Big-Red-Sat/High-Altitude-Student-Platform/HAB Test Data/Battery_Power_Test.txt

Created file at epoch: 1167
(Timestamp: 1169) Temperature Readings: [30.65, 30.65, 244.84, 29.35, 30.00, -26.45, 30.00, -21.94], Solar Cell 1: [Voltage: 0.01V, Current: 0.33mA], Solar Cell 2: [Voltage: 0.01V, Current: 0.65mA]
(Timestamp: 1672) Temperature Readings: [24.19, 22.26, 35.16, 23.23, 23.55, 28.06, 24.19, 28.71], Solar Cell 1: [Voltage: 0.00V, Current: 0.65mA], Solar Cell 2: [Voltage: 0.01V, Current: 0.65mA]
(Timestamp: 2174) Temperature Readings: [24.19, 22.90, 33.23, 23.23, 23.87, 28.71, 24.19, 28.71], Solar Cell 1: [Voltage: 0.00V, Current: 0.65mA], Solar Cell 2: [Voltage: 0.01V, Current: 0.65mA]
(Timestamp: 2677) Temperature Readings: [24.52, 22.90, 32.58, 23.23, 23.87, 28.71, 23.87, 28.39], Solar Cell 1: [Voltage: 0.01V, Current: 0.65mA], Solar Cell 2: [Voltage: 0.01V, Current: 0.65mA]
(Timestamp: 3180) Temperature Readings: [24.19, 26.77, 32.26, 23.23, 23.55, 28.71, 24.19, 28.06], Solar Cell 1: [Voltage: 0.00V, Current: 0.65mA], Solar Cell 2: [Voltage: 0.01V, Current: 0.65mA]
(Timestamp: 3682) Temperature Readings: [24.19, 23.23, 31.94, 23.23, 23.87, 28.06, 24.19, 28.06], Solar Cell 1: [Voltage: 0.00V, Current: 0.65mA], Solar Cell 2: [Voltage: 0.01V, Current: 0.65mA]
(Timestamp: 4185) Temperature Readings: [24.19, 22.58, 31.61, 23.23, 23.55, 28.06, 24.19, 27.74], Solar Cell 1: [Voltage: 0.00V, Current: 0.33mA], Solar Cell 2: [Voltage: 0.01V, Current: 0.65mA]
(Timestamp: 4688) Temperature Readings: [23.87, 22.90, 31.61, 23.23, 23.87, 27.74, 23.87, 26.13], Solar Cell 1: [Voltage: 0.01V, Current: 0.65mA], Solar Cell 2: [Voltage: 0.01V, Current: 0.65mA]
(Timestamp: 5191) Temperature Readings: [25.16, 22.26, 31.94, 23.23, 23.55, 28.06, 24.19, 27.74], Solar Cell 1: [Voltage: 0.00V, Current: 0.33mA], Solar Cell 2: [Voltage: 0.01V, Current: 0.65mA]
(Timestamp: 5694) Temperature Readings: [24.19, 23.23, 31.29, 22.90, 23.87, 27.42, 24.19, 26.45], Solar Cell 1: [Voltage: 0.00V, Current: 0.65mA], Solar Cell 2: [Voltage: 0.01V, Current: 0.65mA]
(Timestamp: 6196) Temperature Readings: [24.52, 22.90, 31.29, 23.23, 23.55, 27.42, 24.19, 25.81], Solar Cell 1: [Voltage: 0.00V, Current: 0.65mA], Solar Cell 2: [Voltage: 0.01V, Current: 0.98mA]
(Timestamp: 6703) Temperature Readings: [24.52, 24.52, 30.97, 23.23, 23.55, 27.10, 24.19, 25.81], Solar Cell 1: [Voltage: 0.00V, Current: 0.65mA], Solar Cell 2: [Voltage: 0.01V, Current: 0.65mA]
(Timestamp: 7205) Temperature Readings: [24.52, 22.58, 30.97, 23.23, 23.55, 26.77, 24.19, 25.81], Solar Cell 1: [Voltage: 0.00V, Current: 0.65mA], Solar Cell 2: [Voltage: 0.01V, Current: 0.65mA]
(Timestamp: 7708) Temperature Readings: [24.84, 22.58, 30.00, 23.55, 23.23, 27.10, 24.19, 25.48], Solar Cell 1: [Voltage: 0.00V, Current: 0.33mA], Solar Cell 2: [Voltage: 0.01V, Current: 0.65mA]
(Timestamp: 8211) Temperature Readings: [25.16, 29.35, 30.65, 23.23, 23.55, 26.77, 24.19, 25.81], Solar Cell 1: [Voltage: 0.00V, Current: 0.65mA], Solar Cell 2: [Voltage: 0.01V, Current: 0.98mA]
(Timestamp: 8714) Temperature Readings: [24.52, 22.90, 30.97, 22.90, 23.23, 26.77, 24.19, 25.48], Solar Cell 1: [Voltage: 0.00V, Current: 0.98mA], Solar Cell 2: [Voltage: 0.01V, Current: 0.65mA]
(Timestamp: 9217) Temperature Readings: [24.52, 23.23, 30.32, 22.90, 23.55, 26.77, 24.19, 25.16], Solar Cell 1: [Voltage: 0.00V, Current: 0.65mA], Solar Cell 2: [Voltage: 0.01V, Current: 0.65mA]
(Timestamp: 9719) Temperature Readings: [24.52, 22.90, 30.32, 23.23, 23.55, 26.77, 24.19, 25.16], Solar Cell 1: [Voltage: 0.00V, Current: 0.33mA], Solar Cell 2: [Voltage: 0.01V, Current: 0.65mA]
(Timestamp: 10222) Temperature Readings: [24.52, 22.90, 30.00, 23.23, 23.55, 27.10, 23.87, 25.16], Solar Cell 1: [Voltage: 0.00V, Current: 0.65mA], Solar Cell 2: [Voltage: 0.01V, Current: 0.65mA]
(Timestamp: 10725) Temperature Readings: [24.52, 22.90, 30.00, 23.23, 23.55, 26.45, 23.87, 25.16], Solar Cell 1: [Voltage: 0.00V, Current: 0.65mA], Solar Cell 2: [Voltage: 0.01V, Current: 0.65mA]
(Timestamp: 11227) Temperature Readings: [24.19, 22.90, 30.00, 23.23, 23.55, 26.45, 24.19, 25.16], Solar Cell 1: [Voltage: 0.01V, Current: 0.65mA], Solar Cell 2: [Voltage: 0.01V, Current: 0.65mA]
(Timestamp: 11730) Temperature Readings: [24.52, 22.90, 30.00, 23.23, 23.55, 26.45, 24.19, 24.84], Solar Cell 1: [Voltage: 0.00V, Current: 0.65mA], Solar Cell 2: [Voltage: 0.01V, Current: 0.98mA]
(Timestamp: 12236) Temperature Readings: [24.52, 22.90, 29.68, 23.55, 23.55, 26.45, 24.19, 24.84], Solar Cell 1: [Voltage: 0.01V, Current: 0.33mA], Solar Cell 2: [Voltage: 0.01V, Current: 0.98mA]
(Timestamp: 12739) Temperature Readings: [24.52, 22.90, 29.68, 23.23, 23.55, 26.45, 24.19, 24.84], Solar Cell 1: [Voltage: 0.01V, Current: 0.65mA], Solar Cell 2: [Voltage: 0.01V, Current: 0.65mA]
(Timestamp: 13241) Temperature Readings: [24.52, 22.90, 29.35, 23.23, 23.55, 26.13, 24.19, 24.52], Solar Cell 1: [Voltage: 0.00V, Current: 0.65mA], Solar Cell 2: [Voltage: 0.01V, Current: 0.65mA]
(Timestamp: 13744) Temperature Readings: [24.52, 22.90, 29.35, 23.23, 23.55, 26.13, 24.19, 24.52], Solar Cell 1: [Voltage: 0.00V, Current: 0.65mA], Solar Cell 2: [Voltage: 0.02V, Current: 0.98mA]
(Timestamp: 14247) Temperature Readings: [24.52, 22.90, 29.35, 23.23, 23.87, 26.13, 24.19, 24.84], Solar Cell 1: [Voltage: 0.00V, Current: 0.65mA], Solar Cell 2: [Voltage: 0.01V, Current: 0.65mA]
(Timestamp: 14749) Temperature Readings: [24.52, 22.90, 29.35, 23.23, 23.55, 25.81, 23.87, 24.52], Solar Cell 1: [Voltage: 0.01V, Current: 0.33mA], Solar Cell 2: [Voltage: 0.01V, Current: 0.98mA]
(Timestamp: 15252) Temperature Readings: [24.19, 22.90, 29.35, 23.23, 23.55, 25.81, 23.87, 24.52], Solar Cell 1: [Voltage: 0.01V, Current: 0.33mA], Solar Cell 2: [Voltage: 0.01V, Current: 0.65mA]
(Timestamp: 15755) Temperature Readings: [24.52, 22.90, 29.35, 23.23, 23.55, 25.81, 24.19, 24.52], Solar Cell 1: [Voltage: 0.00V, Current: 0.65mA], Solar Cell 2: [Voltage: 0.01V, Current: 0.65mA]
(Timestamp: 16258) Temperature Readings: [24.52, 22.90, 29.03, 23.23, 23.55, 25.81, 24.19, 24.52], Solar Cell 1: [Voltage: 0.00V, Current: 0.65mA], Solar Cell 2: [Voltage: 0.01V, Current: 0.65mA]
(Timestamp: 16761) Temperature Readings: [24.19, 23.23, 29.35, 23.23, 23.87, 25.81, 24.19, 24.52], Solar Cell 1: [Voltage: 0.00V, Current: 0.33mA], Solar Cell 2: [Voltage: 0.01V, Current: 0.65mA]
(Timestamp: 17263) Temperature Readings: [24.52, 22.90, 29.03, 23.23, 23.55, 25.81, 24.19, 24.19], Solar Cell 1: [Voltage: 0.00V, Current: 0.65mA], Solar Cell 2: [Voltage: 0.01V, Current: 0.65mA]
(Timestamp: 17766) Temperature Readings: [24.19, 22.90, 29.03, 23.23, 23.55, 25.81, 24.19, 24.19], Solar Cell 1: [Voltage: 0.00V, Current: 0.65mA], Solar Cell 2: [Voltage: 0.01V, Current: 0.65mA]
(Timestamp: 18272) Temperature Readings: [24.52, 22.90, 29.03, 23.55, 23.55, 25.81, 24.19, 24.19], Solar Cell 1: [Voltage: 0.00V, Current: 0.65mA], Solar Cell 2: [Voltage: 0.01V, Current: 0.65mA]
(Timestamp: 18775) Temperature Readings: [24.52, 23.23, 29.03, 23.55, 23.55, 25.81, 24.19, 24.19], Solar Cell 1: [Voltage: 0.00V, Current: 0.65mA], Solar Cell 2: [Voltage: 0.01V, Current: 0.65mA]
(Timestamp: 19278) Temperature Readings: [24.52, 22.90, 29.03, 23.23, 23.87, 25.81, 24.19, 24.19], Solar Cell 1: [Voltage: 0.00V, Current: 0.65mA], Solar Cell 2: [Voltage: 0.01V, Current: 0.65mA]
(Timestamp: 19781) Temperature Readings: [24.52, 22.90, 29.03, 23.23, 23.55, 25.81, 24.19, 24.52], Solar Cell 1: [Voltage: 0.00V, Current: 0.65mA], Solar Cell 2: [Voltage: 0.01V, Current: 0.98mA]
(Timestamp: 20284) Temperature Readings: [24.52, 22.90, 29.03, 23.23, 23.55, 25.48, 24.19, 24.19], Solar Cell 1: [Voltage: 0.00V, Current: 0.65mA], Solar Cell 2: [Voltage: 0.01V, Current: 0.65mA]
(Timestamp: 20786) Temperature Readings: [24.52, 22.90, 29.03, 23.23, 23.55, 25.48, 24.19, 24.19], Solar Cell 1: [Voltage: 0.00V, Current: 0.33mA], Solar Cell 2: [Voltage: 0.01V, Current: 0.65mA]
(Timestamp: 21289) Temperature Readings: [24.19, 22.90, 29.03, 23.55, 23.87, 25.48, 24.19, 24.52], Solar Cell 1: [Voltage: 1.86V, Current: 3.26mA], Solar Cell 2: [Voltage: 2.15V, Current: 4.90mA]
(Timestamp: 21791) Temperature Readings: [24.52, 22.90, 28.39, 23.23, 23.87, 25.48, 23.87, 25.16], Solar Cell 1: [Voltage: 1.55V, Current: 2.94mA], Solar Cell 2: [Voltage: 0.86V, Current: 75.09mA]
(Timestamp: 22294) Temperature Readings: [24.19, 22.90, 29.03, 23.23, 23.55, 25.16, 24.19, 24.52], Solar Cell 1: [Voltage: 1.88V, Current: 3.59mA], Solar Cell 2: [Voltage: 2.52V, Current: 5.22mA]
(Timestamp: 22796) Temperature Readings: [24.52, 22.90, 28.39, 23.23, 23.55, 25.16, 24.19, 24.19], Solar Cell 1: [Voltage: 2.15V, Current: 3.59mA], Solar Cell 2: [Voltage: 2.65V, Current: 5.55mA]
(Timestamp: 23299) Temperature Readings: [24.52, 22.90, 28.39, 23.23, 23.55, 23.87, 24.19, 23.87], Solar Cell 1: [Voltage: 1.82V, Current: 3.26mA], Solar Cell 2: [Voltage: 1.63V, Current: 4.24mA]
(Timestamp: 23801) Temperature Readings: [24.52, 22.90, 28.71, 23.55, 23.87, 25.16, 24.19, 24.52], Solar Cell 1: [Voltage: 2.21V, Current: 3.59mA], Solar Cell 2: [Voltage: 3.00V, Current: 6.20mA]
(Timestamp: 24308) Temperature Readings: [24.52, 22.90, 28.71, 23.55, 23.55, 24.19, 24.19, 24.19], Solar Cell 1: [Voltage: 2.05V, Current: 3.92mA], Solar Cell 2: [Voltage: 2.73V, Current: 5.55mA]
(Timestamp: 24811) Temperature Readings: [24.52, 22.90, 28.71, 23.55, 23.87, 25.16, 24.19, 24.19], Solar Cell 1: [Voltage: 2.22V, Current: 3.59mA], Solar Cell 2: [Voltage: 2.82V, Current: 5.88mA]
(Timestamp: 25313) Temperature Readings: [24.52, 23.23, 28.39, 23.23, 23.87, 25.81, 24.19, 25.81], Solar Cell 1: [Voltage: 1.96V, Current: 3.26mA], Solar Cell 2: [Voltage: 1.16V, Current: 105.13mA]
(Timestamp: 25816) Temperature Readings: [24.84, 23.23, 28.71, 23.23, 23.55, 25.16, 24.19, 24.19], Solar Cell 1: [Voltage: 2.11V, Current: 3.59mA], Solar Cell 2: [Voltage: 2.79V, Current: 5.88mA]
(Timestamp: 26319) Temperature Readings: [24.52, 22.90, 28.71, 23.23, 23.55, 24.19, 24.19, 24.19], Solar Cell 1: [Voltage: 2.23V, Current: 3.92mA], Solar Cell 2: [Voltage: 2.94V, Current: 5.88mA]
(Timestamp: 26822) Temperature Readings: [24.52, 22.90, 28.06, 23.23, 23.87, 24.52, 24.19, 24.84], Solar Cell 1: [Voltage: 1.86V, Current: 3.26mA], Solar Cell 2: [Voltage: 1.03V, Current: 95.01mA]
(Timestamp: 27324) Temperature Readings: [24.52, 22.90, 28.71, 23.55, 23.87, 23.87, 24.19, 24.19], Solar Cell 1: [Voltage: 2.17V, Current: 3.92mA], Solar Cell 2: [Voltage: 3.00V, Current: 6.20mA]
(Timestamp: 27827) Temperature Readings: [24.52, 23.23, 28.39, 23.23, 23.55, 23.87, 24.19, 23.87], Solar Cell 1: [Voltage: 2.18V, Current: 3.92mA], Solar Cell 2: [Voltage: 2.75V, Current: 5.88mA]
(Timestamp: 28330) Temperature Readings: [24.52, 22.90, 28.06, 23.55, 23.55, 23.87, 24.19, 23.23], Solar Cell 1: [Voltage: 1.90V, Current: 3.59mA], Solar Cell 2: [Voltage: 1.81V, Current: 4.57mA]
(Timestamp: 28833) Temperature Readings: [24.52, 22.58, 28.39, 23.55, 23.87, 23.87, 24.19, 24.19], Solar Cell 1: [Voltage: 2.19V, Current: 3.92mA], Solar Cell 2: [Voltage: 3.02V, Current: 6.20mA]
(Timestamp: 29336) Temperature Readings: [24.52, 22.90, 28.39, 23.23, 23.87, 23.87, 24.19, 23.87], Solar Cell 1: [Voltage: 2.14V, Current: 3.59mA], Solar Cell 2: [Voltage: 2.37V, Current: 5.22mA]
(Timestamp: 29838) Temperature Readings: [24.52, 22.90, 28.39, 23.55, 23.55, 23.87, 24.19, 23.87], Solar Cell 1: [Voltage: 1.98V, Current: 3.92mA], Solar Cell 2: [Voltage: 2.55V, Current: 5.55mA]
(Timestamp: 30345) Temperature Readings: [24.52, 22.90, 28.06, 23.23, 23.87, 24.19, 24.19, 24.84], Solar Cell 1: [Voltage: 1.98V, Current: 3.26mA], Solar Cell 2: [Voltage: 0.98V, Current: 86.52mA]
(Timestamp: 30848) Temperature Readings: [24.52, 23.23, 28.39, 23.55, 23.87, 23.87, 24.19, 23.87], Solar Cell 1: [Voltage: 2.21V, Current: 3.59mA], Solar Cell 2: [Voltage: 2.95V, Current: 6.20mA]
(Timestamp: 31350) Temperature Readings: [24.84, 22.58, 28.39, 23.55, 23.87, 23.87, 24.19, 24.19], Solar Cell 1: [Voltage: 2.34V, Current: 3.92mA], Solar Cell 2: [Voltage: 2.95V, Current: 5.88mA]
(Timestamp: 31853) Temperature Readings: [24.52, 22.90, 27.74, 23.23, 23.87, 23.87, 24.19, 24.84], Solar Cell 1: [Voltage: 2.05V, Current: 3.59mA], Solar Cell 2: [Voltage: 0.95V, Current: 83.26mA]
(Timestamp: 32355) Temperature Readings: [24.84, 23.23, 28.06, 23.55, 23.55, 23.55, 24.19, 23.87], Solar Cell 1: [Voltage: 2.24V, Current: 3.92mA], Solar Cell 2: [Voltage: 2.94V, Current: 5.88mA]
(Timestamp: 32858) Temperature Readings: [24.52, 22.90, 28.39, 23.55, 23.87, 24.19, 24.19, 23.87], Solar Cell 1: [Voltage: 2.33V, Current: 3.92mA], Solar Cell 2: [Voltage: 2.94V, Current: 5.88mA]
(Timestamp: 33360) Temperature Readings: [24.52, 23.23, 27.74, 23.23, 23.87, 23.87, 24.19, 24.84], Solar Cell 1: [Voltage: 2.02V, Current: 3.59mA], Solar Cell 2: [Voltage: 0.95V, Current: 83.58mA]
(Timestamp: 33863) Temperature Readings: [24.84, 22.90, 28.06, 23.55, 23.55, 23.55, 24.19, 23.87], Solar Cell 1: [Voltage: 2.19V, Current: 3.92mA], Solar Cell 2: [Voltage: 2.93V, Current: 5.88mA]
(Timestamp: 34366) Temperature Readings: [24.52, 22.90, 28.39, 23.55, 23.87, 23.55, 24.19, 24.19], Solar Cell 1: [Voltage: 2.26V, Current: 3.92mA], Solar Cell 2: [Voltage: 2.95V, Current: 5.88mA]
(Timestamp: 34868) Temperature Readings: [24.52, 22.90, 27.74, 23.23, 23.55, 23.87, 24.19, 24.52], Solar Cell 1: [Voltage: 1.90V, Current: 3.26mA], Solar Cell 2: [Voltage: 1.02V, Current: 93.38mA]
(Timestamp: 35371) Temperature Readings: [24.52, 22.90, 27.74, 23.23, 23.55, 23.55, 24.19, 23.87], Solar Cell 1: [Voltage: 2.16V, Current: 3.92mA], Solar Cell 2: [Voltage: 2.99V, Current: 6.20mA]
(Timestamp: 35878) Temperature Readings: [24.52, 22.90, 28.06, 23.23, 23.87, 23.23, 24.19, 23.23], Solar Cell 1: [Voltage: 1.97V, Current: 3.59mA], Solar Cell 2: [Voltage: 2.45V, Current: 5.22mA]
(Timestamp: 36380) Temperature Readings: [24.52, 22.90, 28.06, 23.55, 23.87, 23.55, 24.19, 23.87], Solar Cell 1: [Voltage: 2.23V, Current: 3.92mA], Solar Cell 2: [Voltage: 3.03V, Current: 6.20mA]
(Timestamp: 36883) Temperature Readings: [24.52, 22.90, 28.06, 23.55, 23.87, 23.23, 24.19, 23.23], Solar Cell 1: [Voltage: 2.12V, Current: 3.59mA], Solar Cell 2: [Voltage: 1.86V, Current: 4.57mA]
(Timestamp: 37386) Temperature Readings: [24.52, 22.90, 27.74, 23.55, 23.87, 23.23, 24.19, 23.87], Solar Cell 1: [Voltage: 2.06V, Current: 3.92mA], Solar Cell 2: [Voltage: 2.75V, Current: 5.88mA]
(Timestamp: 37889) Temperature Readings: [24.52, 23.23, 28.06, 23.55, 23.55, 23.23, 24.19, 23.87], Solar Cell 1: [Voltage: 2.26V, Current: 3.92mA], Solar Cell 2: [Voltage: 3.00V, Current: 6.20mA]
(Timestamp: 38392) Temperature Readings: [24.52, 22.90, 27.74, 23.55, 23.87, 23.23, 24.19, 24.19], Solar Cell 1: [Voltage: 2.02V, Current: 3.59mA], Solar Cell 2: [Voltage: 1.29V, Current: 115.58mA]
(Timestamp: 38894) Temperature Readings: [24.84, 22.90, 27.74, 23.55, 23.87, 23.23, 24.19, 23.87], Solar Cell 1: [Voltage: 2.10V, Current: 3.92mA], Solar Cell 2: [Voltage: 2.87V, Current: 5.88mA]
(Timestamp: 39397) Temperature Readings: [24.52, 22.90, 27.74, 23.55, 23.87, 23.23, 24.19, 23.87], Solar Cell 1: [Voltage: 2.24V, Current: 3.92mA], Solar Cell 2: [Voltage: 2.96V, Current: 5.88mA]
(Timestamp: 39900) Temperature Readings: [24.84, 23.23, 27.74, 23.23, 23.87, 23.87, 24.19, 24.19], Solar Cell 1: [Voltage: 1.99V, Current: 3.26mA], Solar Cell 2: [Voltage: 0.95V, Current: 83.91mA]
(Timestamp: 40403) Temperature Readings: [24.84, 23.23, 28.06, 23.55, 23.87, 23.23, 24.19, 23.87], Solar Cell 1: [Voltage: 2.17V, Current: 3.59mA], Solar Cell 2: [Voltage: 2.93V, Current: 5.88mA]
(Timestamp: 40905) Temperature Readings: [24.52, 23.23, 27.74, 23.55, 23.55, 23.23, 24.19, 23.87], Solar Cell 1: [Voltage: 2.23V, Current: 3.92mA], Solar Cell 2: [Voltage: 2.85V, Current: 5.88mA]
(Timestamp: 41408) Temperature Readings: [24.52, 22.90, 27.42, 23.55, 23.87, 23.87, 24.19, 25.16], Solar Cell 1: [Voltage: 1.90V, Current: 3.59mA], Solar Cell 2: [Voltage: 1.26V, Current: 115.91mA]
(Timestamp: 41914) Temperature Readings: [24.52, 23.23, 27.42, 23.55, 23.87, 23.23, 24.19, 23.23], Solar Cell 1: [Voltage: 2.17V, Current: 3.59mA], Solar Cell 2: [Voltage: 2.48V, Current: 5.22mA]
(Timestamp: 42417) Temperature Readings: [24.52, 23.23, 27.42, 23.55, 23.87, 23.23, 24.19, 22.90], Solar Cell 1: [Voltage: 1.95V, Current: 3.59mA], Solar Cell 2: [Voltage: 2.14V, Current: 4.90mA]
(Timestamp: 42919) Temperature Readings: [24.84, 23.23, 27.74, 23.55, 23.87, 23.23, 24.19, 23.87], Solar Cell 1: [Voltage: 2.19V, Current: 3.92mA], Solar Cell 2: [Voltage: 2.86V, Current: 5.88mA]
(Timestamp: 43422) Temperature Readings: [24.52, 22.90, 27.74, 23.55, 23.87, 23.23, 24.19, 23.23], Solar Cell 1: [Voltage: 2.16V, Current: 3.92mA], Solar Cell 2: [Voltage: 2.41V, Current: 5.22mA]
(Timestamp: 43925) Temperature Readings: [24.52, 23.23, 27.74, 23.55, 23.87, 23.23, 24.19, 22.90], Solar Cell 1: [Voltage: 1.93V, Current: 3.59mA], Solar Cell 2: [Voltage: 2.05V, Current: 4.90mA]
(Timestamp: 44427) Temperature Readings: [24.84, 23.23, 27.74, 23.55, 23.87, 23.23, 24.19, 23.87], Solar Cell 1: [Voltage: 2.17V, Current: 4.24mA], Solar Cell 2: [Voltage: 3.01V, Current: 6.20mA]
(Timestamp: 44930) Temperature Readings: [24.84, 22.90, 27.74, 23.55, 23.55, 23.23, 24.19, 23.23], Solar Cell 1: [Voltage: 2.13V, Current: 3.59mA], Solar Cell 2: [Voltage: 2.33V, Current: 5.22mA]
(Timestamp: 45433) Temperature Readings: [24.84, 23.23, 27.42, 23.55, 23.87, 23.23, 24.19, 23.23], Solar Cell 1: [Voltage: 1.95V, Current: 3.59mA], Solar Cell 2: [Voltage: 2.45V, Current: 5.22mA]
(Timestamp: 45935) Temperature Readings: [24.84, 22.90, 27.74, 23.55, 23.87, 22.90, 24.19, 23.87], Solar Cell 1: [Voltage: 2.17V, Current: 3.92mA], Solar Cell 2: [Voltage: 3.03V, Current: 6.20mA]
(Timestamp: 46438) Temperature Readings: [24.52, 22.90, 27.42, 23.23, 23.87, 22.58, 24.19, 22.58], Solar Cell 1: [Voltage: 2.04V, Current: 3.59mA], Solar Cell 2: [Voltage: 1.68V, Current: 4.24mA]
(Timestamp: 46941) Temperature Readings: [24.52, 23.23, 27.42, 23.55, 23.55, 23.23, 24.19, 23.23], Solar Cell 1: [Voltage: 2.03V, Current: 3.59mA], Solar Cell 2: [Voltage: 2.84V, Current: 5.88mA]
(Timestamp: 47444) Temperature Readings: [24.52, 22.90, 27.74, 23.55, 23.55, 23.23, 24.19, 23.23], Solar Cell 1: [Voltage: 2.18V, Current: 3.59mA], Solar Cell 2: [Voltage: 3.01V, Current: 6.20mA]
(Timestamp: 47950) Temperature Readings: [24.52, 23.23, 27.42, 23.55, 23.87, 23.23, 24.19, 23.23], Solar Cell 1: [Voltage: 2.14V, Current: 3.92mA], Solar Cell 2: [Voltage: 2.99V, Current: 6.20mA]
(Timestamp: 48453) Temperature Readings: [24.52, 23.23, 27.42, 23.55, 23.87, 23.23, 24.19, 23.23], Solar Cell 1: [Voltage: 2.14V, Current: 3.59mA], Solar Cell 2: [Voltage: 2.72V, Current: 5.55mA]
(Timestamp: 48956) Temperature Readings: [24.84, 23.23, 27.42, 23.23, 23.87, 22.58, 24.19, 22.58], Solar Cell 1: [Voltage: 1.90V, Current: 3.59mA], Solar Cell 2: [Voltage: 2.01V, Current: 4.90mA]
(Timestamp: 49458) Temperature Readings: [24.52, 22.90, 27.42, 23.55, 23.87, 23.23, 24.19, 23.55], Solar Cell 1: [Voltage: 2.17V, Current: 3.92mA], Solar Cell 2: [Voltage: 3.06V, Current: 6.20mA]
(Timestamp: 49961) Temperature Readings: [24.84, 22.90, 27.42, 23.55, 23.55, 22.58, 24.19, 22.90], Solar Cell 1: [Voltage: 2.10V, Current: 3.59mA], Solar Cell 2: [Voltage: 2.28V, Current: 5.22mA]
(Timestamp: 50464) Temperature Readings: [24.84, 23.23, 27.42, 23.55, 23.87, 22.90, 24.19, 23.23], Solar Cell 1: [Voltage: 1.97V, Current: 3.92mA], Solar Cell 2: [Voltage: 2.69V, Current: 5.55mA]
(Timestamp: 50967) Temperature Readings: [24.52, 23.23, 27.42, 23.55, 23.87, 22.90, 24.19, 23.55], Solar Cell 1: [Voltage: 2.17V, Current: 3.92mA], Solar Cell 2: [Voltage: 3.07V, Current: 6.20mA]
(Timestamp: 51469) Temperature Readings: [24.52, 22.90, 27.42, 23.55, 23.87, 22.58, 24.19, 22.26], Solar Cell 1: [Voltage: 2.00V, Current: 3.59mA], Solar Cell 2: [Voltage: 1.39V, Current: 34.28mA]
(Timestamp: 51972) Temperature Readings: [24.84, 23.23, 27.42, 23.55, 23.55, 22.90, 24.19, 23.23], Solar Cell 1: [Voltage: 2.05V, Current: 3.59mA], Solar Cell 2: [Voltage: 2.94V, Current: 5.88mA]
(Timestamp: 52475) Temperature Readings: [24.84, 22.90, 27.42, 23.55, 23.87, 22.58, 24.19, 23.87], Solar Cell 1: [Voltage: 1.03V, Current: 112.32mA], Solar Cell 2: [Voltage: 3.05V, Current: 5.88mA]
(Timestamp: 52977) Temperature Readings: [24.84, 23.23, 27.42, 23.55, 23.87, 23.23, 24.19, 24.84], Solar Cell 1: [Voltage: 1.99V, Current: 3.59mA], Solar Cell 2: [Voltage: 1.17V, Current: 106.77mA]
(Timestamp: 53483) Temperature Readings: [24.84, 23.23, 27.42, 23.55, 23.55, 22.58, 24.19, 23.23], Solar Cell 1: [Voltage: 2.21V, Current: 3.92mA], Solar Cell 2: [Voltage: 2.86V, Current: 5.88mA]
(Timestamp: 53986) Temperature Readings: [24.84, 23.23, 27.10, 23.55, 23.87, 23.23, 24.19, 24.84], Solar Cell 1: [Voltage: 1.86V, Current: 3.59mA], Solar Cell 2: [Voltage: 1.30V, Current: 95.01mA]
(Timestamp: 54489) Temperature Readings: [24.84, 23.23, 27.42, 23.55, 23.87, 22.58, 24.19, 23.23], Solar Cell 1: [Voltage: 2.16V, Current: 3.92mA], Solar Cell 2: [Voltage: 3.03V, Current: 6.20mA]
(Timestamp: 54991) Temperature Readings: [24.84, 23.23, 27.42, 23.55, 23.87, 22.58, 24.19, 23.23], Solar Cell 1: [Voltage: 2.21V, Current: 3.92mA], Solar Cell 2: [Voltage: 2.86V, Current: 5.88mA]
(Timestamp: 55494) Temperature Readings: [24.84, 23.23, 27.10, 23.55, 23.87, 22.58, 24.19, 22.26], Solar Cell 1: [Voltage: 1.89V, Current: 3.59mA], Solar Cell 2: [Voltage: 1.54V, Current: 4.24mA]
(Timestamp: 55997) Temperature Readings: [24.84, 23.23, 27.42, 23.55, 23.87, 22.58, 24.19, 23.23], Solar Cell 1: [Voltage: 2.20V, Current: 3.92mA], Solar Cell 2: [Voltage: 3.05V, Current: 6.20mA]
(Timestamp: 56499) Temperature Readings: [24.84, 23.23, 27.42, 23.55, 23.87, 22.90, 24.19, 22.90], Solar Cell 1: [Voltage: 2.15V, Current: 3.92mA], Solar Cell 2: [Voltage: 2.57V, Current: 5.55mA]
(Timestamp: 57002) Temperature Readings: [24.84, 23.23, 27.10, 23.55, 23.87, 22.58, 24.19, 22.90], Solar Cell 1: [Voltage: 1.95V, Current: 3.59mA], Solar Cell 2: [Voltage: 2.42V, Current: 5.22mA]
(Timestamp: 57505) Temperature Readings: [24.84, 23.23, 27.42, 23.23, 23.87, 22.58, 24.19, 23.23], Solar Cell 1: [Voltage: 2.21V, Current: 3.59mA], Solar Cell 2: [Voltage: 3.06V, Current: 6.20mA]
(Timestamp: 58008) Temperature Readings: [24.84, 23.23, 27.42, 23.55, 23.87, 22.58, 24.19, 22.26], Solar Cell 1: [Voltage: 2.09V, Current: 3.59mA], Solar Cell 2: [Voltage: 1.86V, Current: 4.24mA]
(Timestamp: 58510) Temperature Readings: [24.84, 23.23, 27.10, 23.55, 23.87, 22.26, 24.19, 22.90], Solar Cell 1: [Voltage: 2.06V, Current: 3.92mA], Solar Cell 2: [Voltage: 2.83V, Current: 5.88mA]
(Timestamp: 59013) Temperature Readings: [24.84, 23.55, 27.42, 23.55, 23.87, 22.58, 24.19, 23.23], Solar Cell 1: [Voltage: 2.23V, Current: 3.92mA], Solar Cell 2: [Voltage: 3.04V, Current: 6.20mA]
(Timestamp: 59520) Temperature Readings: [25.16, 23.23, 27.10, 23.55, 23.87, 22.58, 24.19, 23.23], Solar Cell 1: [Voltage: 2.17V, Current: 3.92mA], Solar Cell 2: [Voltage: 3.02V, Current: 6.20mA]
(Timestamp: 60022) Temperature Readings: [24.84, 23.23, 27.42, 23.55, 23.87, 22.58, 24.52, 23.23], Solar Cell 1: [Voltage: 2.20V, Current: 3.92mA], Solar Cell 2: [Voltage: 2.83V, Current: 5.88mA]
(Timestamp: 60525) Temperature Readings: [24.84, 23.23, 27.10, 23.55, 23.87, 22.58, 24.19, 22.26], Solar Cell 1: [Voltage: 1.90V, Current: 3.59mA], Solar Cell 2: [Voltage: 1.79V, Current: 4.57mA]
(Timestamp: 61028) Temperature Readings: [24.84, 22.90, 27.10, 23.55, 23.87, 22.58, 24.19, 23.23], Solar Cell 1: [Voltage: 2.24V, Current: 3.92mA], Solar Cell 2: [Voltage: 3.07V, Current: 6.20mA]
(Timestamp: 61531) Temperature Readings: [24.84, 23.23, 27.10, 23.55, 23.87, 22.58, 24.19, 22.90], Solar Cell 1: [Voltage: 2.15V, Current: 3.92mA], Solar Cell 2: [Voltage: 2.48V, Current: 5.22mA]
(Timestamp: 62033) Temperature Readings: [24.84, 23.23, 27.10, 23.55, 23.87, 22.58, 24.19, 22.58], Solar Cell 1: [Voltage: 2.00V, Current: 3.92mA], Solar Cell 2: [Voltage: 2.54V, Current: 5.55mA]
(Timestamp: 62536) Temperature Readings: [24.84, 23.23, 27.10, 23.55, 23.87, 22.58, 24.19, 22.90], Solar Cell 1: [Voltage: 2.24V, Current: 3.92mA], Solar Cell 2: [Voltage: 2.25V, Current: 5.22mA]
(Timestamp: 63039) Temperature Readings: [24.84, 23.23, 27.10, 23.55, 23.87, 22.26, 24.19, 22.58], Solar Cell 1: [Voltage: 2.13V, Current: 3.92mA], Solar Cell 2: [Voltage: 1.83V, Current: 4.57mA]
(Timestamp: 63541) Temperature Readings: [24.84, 23.23, 27.10, 23.55, 23.87, 22.58, 24.19, 22.90], Solar Cell 1: [Voltage: 1.96V, Current: 3.59mA], Solar Cell 2: [Voltage: 2.50V, Current: 5.55mA]
(Timestamp: 64044) Temperature Readings: [25.16, 23.23, 27.42, 23.55, 23.87, 22.58, 24.19, 23.23], Solar Cell 1: [Voltage: 2.20V, Current: 3.92mA], Solar Cell 2: [Voltage: 3.12V, Current: 6.20mA]
(Timestamp: 64546) Temperature Readings: [25.16, 23.23, 27.10, 23.55, 23.87, 22.58, 24.19, 22.26], Solar Cell 1: [Voltage: 2.10V, Current: 3.59mA], Solar Cell 2: [Voltage: 2.20V, Current: 4.90mA]
(Timestamp: 65049) Temperature Readings: [24.84, 23.23, 27.10, 23.55, 23.87, 22.58, 24.19, 22.90], Solar Cell 1: [Voltage: 1.97V, Current: 3.59mA], Solar Cell 2: [Voltage: 2.59V, Current: 5.55mA]
(Timestamp: 65555) Temperature Readings: [24.84, 23.23, 27.10, 23.55, 23.87, 22.90, 24.19, 24.52], Solar Cell 1: [Voltage: 2.00V, Current: 3.59mA], Solar Cell 2: [Voltage: 1.25V, Current: 112.64mA]
(Timestamp: 66058) Temperature Readings: [25.16, 23.23, 27.10, 23.55, 23.87, 22.58, 24.19, 22.90], Solar Cell 1: [Voltage: 2.08V, Current: 3.92mA], Solar Cell 2: [Voltage: 2.99V, Current: 6.20mA]
(Timestamp: 66560) Temperature Readings: [24.84, 23.23, 27.10, 23.55, 24.19, 22.58, 24.19, 22.90], Solar Cell 1: [Voltage: 2.21V, Current: 3.92mA], Solar Cell 2: [Voltage: 3.05V, Current: 6.20mA]
(Timestamp: 67063) Temperature Readings: [24.84, 23.55, 26.77, 23.55, 23.87, 22.58, 24.19, 23.55], Solar Cell 1: [Voltage: 1.88V, Current: 3.26mA], Solar Cell 2: [Voltage: 0.94V, Current: 82.93mA]
(Timestamp: 67566) Temperature Readings: [24.84, 23.23, 27.10, 23.55, 23.87, 22.58, 24.19, 22.58], Solar Cell 1: [Voltage: 2.13V, Current: 3.92mA], Solar Cell 2: [Voltage: 3.07V, Current: 6.20mA]
(Timestamp: 68069) Temperature Readings: [25.16, 23.23, 27.10, 23.55, 23.55, 22.58, 24.19, 22.90], Solar Cell 1: [Voltage: 2.18V, Current: 3.92mA], Solar Cell 2: [Voltage: 2.92V, Current: 5.88mA]
(Timestamp: 68572) Temperature Readings: [24.84, 23.23, 26.77, 23.55, 23.87, 22.26, 24.19, 21.61], Solar Cell 1: [Voltage: 1.86V, Current: 3.59mA], Solar Cell 2: [Voltage: 1.60V, Current: 4.24mA]
(Timestamp: 69074) Temperature Readings: [24.84, 23.55, 27.10, 23.55, 23.87, 22.58, 24.19, 22.90], Solar Cell 1: [Voltage: 2.19V, Current: 3.92mA], Solar Cell 2: [Voltage: 3.11V, Current: 6.20mA]
(Timestamp: 69577) Temperature Readings: [25.16, 23.23, 27.10, 23.55, 23.87, 22.58, 24.19, 22.90], Solar Cell 1: [Voltage: 2.17V, Current: 3.92mA], Solar Cell 2: [Voltage: 2.57V, Current: 5.55mA]
(Timestamp: 70080) Temperature Readings: [25.16, 23.23, 27.10, 23.55, 23.87, 22.26, 24.19, 22.26], Solar Cell 1: [Voltage: 1.95V, Current: 3.59mA], Solar Cell 2: [Voltage: 2.46V, Current: 5.55mA]
(Timestamp: 70583) Temperature Readings: [25.16, 23.55, 27.10, 23.55, 23.87, 22.58, 24.19, 22.90], Solar Cell 1: [Voltage: 2.23V, Current: 3.92mA], Solar Cell 2: [Voltage: 3.12V, Current: 6.20mA]
(Timestamp: 71085) Temperature Readings: [25.16, 23.55, 26.77, 23.55, 23.87, 22.26, 24.19, 22.26], Solar Cell 1: [Voltage: 2.05V, Current: 3.59mA], Solar Cell 2: [Voltage: 1.90V, Current: 4.57mA]
(Timestamp: 71592) Temperature Readings: [25.16, 23.23, 27.10, 23.55, 23.87, 22.26, 24.19, 22.58], Solar Cell 1: [Voltage: 2.20V, Current: 3.92mA], Solar Cell 2: [Voltage: 3.03V, Current: 6.20mA]
(Timestamp: 72095) Temperature Readings: [25.16, 23.23, 26.77, 23.55, 23.87, 22.58, 24.19, 23.23], Solar Cell 1: [Voltage: 1.84V, Current: 3.59mA], Solar Cell 2: [Voltage: 1.01V, Current: 91.75mA]
(Timestamp: 72597) Temperature Readings: [25.16, 23.55, 27.10, 23.55, 23.87, 22.26, 24.52, 22.90], Solar Cell 1: [Voltage: 2.12V, Current: 3.92mA], Solar Cell 2: [Voltage: 3.07V, Current: 6.20mA]
(Timestamp: 73100) Temperature Readings: [25.16, 23.55, 27.42, 23.55, 23.87, 22.26, 24.19, 22.58], Solar Cell 1: [Voltage: 2.17V, Current: 3.92mA], Solar Cell 2: [Voltage: 2.93V, Current: 5.88mA]
(Timestamp: 73602) Temperature Readings: [25.16, 23.23, 26.77, 23.55, 23.87, 22.58, 24.19, 24.19], Solar Cell 1: [Voltage: 1.85V, Current: 3.59mA], Solar Cell 2: [Voltage: 1.19V, Current: 111.34mA]
(Timestamp: 74105) Temperature Readings: [25.48, 23.55, 26.77, 23.87, 23.87, 21.94, 24.19, 22.90], Solar Cell 1: [Voltage: 2.13V, Current: 3.92mA], Solar Cell 2: [Voltage: 3.07V, Current: 6.20mA]
(Timestamp: 74608) Temperature Readings: [24.84, 23.55, 27.10, 23.55, 23.87, 22.26, 24.19, 22.90], Solar Cell 1: [Voltage: 2.18V, Current: 3.92mA], Solar Cell 2: [Voltage: 2.90V, Current: 5.88mA]
(Timestamp: 75110) Temperature Readings: [25.16, 23.23, 26.77, 23.55, 23.87, 22.90, 24.19, 24.19], Solar Cell 1: [Voltage: 1.83V, Current: 3.59mA], Solar Cell 2: [Voltage: 1.19V, Current: 111.99mA]
(Timestamp: 75613) Temperature Readings: [25.48, 23.55, 26.77, 23.55, 23.87, 22.26, 24.19, 22.58], Solar Cell 1: [Voltage: 2.11V, Current: 3.92mA], Solar Cell 2: [Voltage: 3.06V, Current: 6.20mA]
(Timestamp: 76116) Temperature Readings: [24.84, 23.55, 27.10, 23.55, 24.19, 22.26, 23.87, 22.90], Solar Cell 1: [Voltage: 2.16V, Current: 3.59mA], Solar Cell 2: [Voltage: 2.92V, Current: 5.88mA]
(Timestamp: 76618) Temperature Readings: [25.16, 23.55, 26.45, 23.55, 23.87, 21.94, 24.19, 21.29], Solar Cell 1: [Voltage: 1.83V, Current: 3.59mA], Solar Cell 2: [Voltage: 1.51V, Current: 4.24mA]
(Timestamp: 77125) Temperature Readings: [25.16, 23.55, 26.77, 23.55, 23.87, 21.94, 24.19, 22.26], Solar Cell 1: [Voltage: 2.05V, Current: 3.59mA], Solar Cell 2: [Voltage: 1.94V, Current: 4.57mA]
(Timestamp: 77628) Temperature Readings: [25.16, 23.23, 26.77, 23.55, 23.87, 22.26, 24.19, 22.58], Solar Cell 1: [Voltage: 2.01V, Current: 3.92mA], Solar Cell 2: [Voltage: 2.83V, Current: 5.88mA]
(Timestamp: 78130) Temperature Readings: [25.16, 23.23, 26.77, 23.87, 24.19, 22.26, 24.19, 22.90], Solar Cell 1: [Voltage: 2.17V, Current: 3.92mA], Solar Cell 2: [Voltage: 3.10V, Current: 6.20mA]
(Timestamp: 78633) Temperature Readings: [25.16, 23.55, 26.77, 23.55, 23.87, 21.94, 24.19, 22.26], Solar Cell 1: [Voltage: 1.95V, Current: 3.59mA], Solar Cell 2: [Voltage: 1.32V, Current: 115.91mA]
(Timestamp: 79136) Temperature Readings: [25.48, 23.55, 26.77, 23.55, 24.19, 22.26, 24.19, 22.58], Solar Cell 1: [Voltage: 2.04V, Current: 3.92mA], Solar Cell 2: [Voltage: 2.95V, Current: 5.88mA]
(Timestamp: 79639) Temperature Readings: [25.16, 23.23, 27.10, 23.87, 23.87, 22.58, 24.19, 22.58], Solar Cell 1: [Voltage: 2.17V, Current: 3.92mA], Solar Cell 2: [Voltage: 3.08V, Current: 6.20mA]
(Timestamp: 80141) Temperature Readings: [25.16, 23.55, 26.45, 23.55, 24.19, 22.58, 24.19, 23.87], Solar Cell 1: [Voltage: 1.87V, Current: 3.26mA], Solar Cell 2: [Voltage: 0.97V, Current: 85.87mA]
(Timestamp: 80644) Temperature Readings: [25.48, 23.55, 26.77, 23.87, 23.87, 22.26, 24.19, 22.58], Solar Cell 1: [Voltage: 2.06V, Current: 3.92mA], Solar Cell 2: [Voltage: 3.03V, Current: 6.20mA]
(Timestamp: 81147) Temperature Readings: [25.16, 23.23, 26.77, 23.87, 23.87, 22.26, 24.19, 22.90], Solar Cell 1: [Voltage: 2.17V, Current: 3.92mA], Solar Cell 2: [Voltage: 3.03V, Current: 6.20mA]
(Timestamp: 81650) Temperature Readings: [25.16, 23.55, 26.45, 23.55, 23.87, 22.26, 24.19, 23.55], Solar Cell 1: [Voltage: 1.81V, Current: 3.59mA], Solar Cell 2: [Voltage: 0.98V, Current: 89.46mA]
(Timestamp: 82152) Temperature Readings: [25.16, 23.55, 26.77, 23.55, 23.87, 22.26, 24.19, 22.90], Solar Cell 1: [Voltage: 2.11V, Current: 3.92mA], Solar Cell 2: [Voltage: 3.06V, Current: 6.20mA]
(Timestamp: 82655) Temperature Readings: [25.48, 23.23, 27.10, 23.87, 23.87, 22.26, 24.52, 22.58], Solar Cell 1: [Voltage: 2.17V, Current: 3.92mA], Solar Cell 2: [Voltage: 2.90V, Current: 5.88mA]
(Timestamp: 83162) Temperature Readings: [25.16, 23.23, 26.77, 23.55, 23.87, 22.26, 24.19, 22.90], Solar Cell 1: [Voltage: 2.16V, Current: 3.92mA], Solar Cell 2: [Voltage: 3.11V, Current: 6.20mA]
(Timestamp: 83664) Temperature Readings: [25.16, 23.55, 26.77, 23.87, 23.87, 22.26, 24.19, 22.26], Solar Cell 1: [Voltage: 2.08V, Current: 3.92mA], Solar Cell 2: [Voltage: 2.34V, Current: 5.22mA]
(Timestamp: 84167) Temperature Readings: [25.48, 23.55, 26.45, 23.55, 23.87, 21.94, 24.19, 21.94], Solar Cell 1: [Voltage: 1.90V, Current: 3.92mA], Solar Cell 2: [Voltage: 2.39V, Current: 5.22mA]
(Timestamp: 84669) Temperature Readings: [25.48, 23.23, 26.77, 23.87, 23.87, 21.94, 24.19, 22.90], Solar Cell 1: [Voltage: 2.15V, Current: 3.92mA], Solar Cell 2: [Voltage: 3.10V, Current: 6.20mA]
(Timestamp: 85172) Temperature Readings: [25.16, 23.55, 26.77, 23.87, 23.87, 21.94, 24.19, 22.26], Solar Cell 1: [Voltage: 2.10V, Current: 3.59mA], Solar Cell 2: [Voltage: 2.48V, Current: 5.22mA]
(Timestamp: 85674) Temperature Readings: [25.16, 23.55, 26.45, 23.55, 24.19, 21.94, 24.19, 21.94], Solar Cell 1: [Voltage: 1.88V, Current: 3.59mA], Solar Cell 2: [Voltage: 2.18V, Current: 5.22mA]
(Timestamp: 86177) Temperature Readings: [25.16, 23.23, 26.77, 23.87, 24.19, 22.26, 24.19, 22.90], Solar Cell 1: [Voltage: 2.16V, Current: 3.92mA], Solar Cell 2: [Voltage: 3.09V, Current: 6.20mA]
(Timestamp: 86680) Temperature Readings: [25.48, 23.55, 26.77, 23.87, 24.19, 21.94, 24.19, 22.26], Solar Cell 1: [Voltage: 2.12V, Current: 3.92mA], Solar Cell 2: [Voltage: 2.57V, Current: 5.55mA]
(Timestamp: 87183) Temperature Readings: [25.48, 23.55, 26.45, 23.55, 23.87, 22.26, 24.19, 21.94], Solar Cell 1: [Voltage: 1.92V, Current: 3.59mA], Solar Cell 2: [Voltage: 2.35V, Current: 5.22mA]
(Timestamp: 87685) Temperature Readings: [25.48, 23.23, 26.77, 23.87, 23.87, 21.94, 24.19, 22.58], Solar Cell 1: [Voltage: 2.17V, Current: 3.92mA], Solar Cell 2: [Voltage: 3.10V, Current: 6.20mA]
(Timestamp: 88188) Temperature Readings: [25.16, 23.55, 26.77, 23.55, 23.87, 21.94, 24.19, 21.94], Solar Cell 1: [Voltage: 2.07V, Current: 3.59mA], Solar Cell 2: [Voltage: 2.19V, Current: 4.90mA]
(Timestamp: 88691) Temperature Readings: [25.48, 23.23, 26.45, 23.87, 23.87, 21.94, 24.19, 22.26], Solar Cell 1: [Voltage: 1.94V, Current: 3.92mA], Solar Cell 2: [Voltage: 2.70V, Current: 5.55mA]
(Timestamp: 89197) Temperature Readings: [25.48, 23.55, 26.45, 23.87, 23.87, 22.26, 24.19, 23.55], Solar Cell 1: [Voltage: 1.87V, Current: 3.26mA], Solar Cell 2: [Voltage: 0.96V, Current: 84.24mA]
(Timestamp: 89700) Temperature Readings: [25.48, 23.23, 26.77, 23.87, 24.19, 21.94, 24.19, 22.90], Solar Cell 1: [Voltage: 2.07V, Current: 3.92mA], Solar Cell 2: [Voltage: 3.02V, Current: 5.88mA]
(Timestamp: 90203) Temperature Readings: [25.48, 23.55, 26.77, 23.87, 23.87, 21.94, 24.19, 22.90], Solar Cell 1: [Voltage: 2.18V, Current: 3.92mA], Solar Cell 2: [Voltage: 3.01V, Current: 6.20mA]
(Timestamp: 90705) Temperature Readings: [25.48, 23.55, 26.45, 23.87, 23.87, 22.26, 24.19, 23.23], Solar Cell 1: [Voltage: 1.81V, Current: 3.26mA], Solar Cell 2: [Voltage: 0.96V, Current: 87.18mA]
(Timestamp: 91208) Temperature Readings: [25.48, 23.55, 26.77, 23.87, 24.19, 21.94, 24.19, 22.90], Solar Cell 1: [Voltage: 2.26V, Current: 3.92mA], Solar Cell 2: [Voltage: 2.21V, Current: 4.90mA]
(Timestamp: 91711) Temperature Readings: [25.48, 23.55, 26.77, 23.55, 23.87, 21.94, 24.52, 22.26], Solar Cell 1: [Voltage: 2.17V, Current: 3.92mA], Solar Cell 2: [Voltage: 2.19V, Current: 4.90mA]
(Timestamp: 92214) Temperature Readings: [25.48, 23.55, 26.45, 23.87, 23.87, 22.26, 24.52, 23.87], Solar Cell 1: [Voltage: 1.81V, Current: 3.59mA], Solar Cell 2: [Voltage: 1.17V, Current: 109.38mA]
(Timestamp: 92717) Temperature Readings: [25.81, 23.55, 26.77, 23.55, 24.19, 21.94, 24.19, 22.58], Solar Cell 1: [Voltage: 2.13V, Current: 3.92mA], Solar Cell 2: [Voltage: 2.39V, Current: 5.22mA]
(Timestamp: 93219) Temperature Readings: [25.81, 23.55, 26.77, 23.87, 23.87, 21.94, 24.52, 22.26], Solar Cell 1: [Voltage: 2.13V, Current: 3.92mA], Solar Cell 2: [Voltage: 2.05V, Current: 4.90mA]
(Timestamp: 93722) Temperature Readings: [25.81, 23.55, 26.45, 23.87, 24.19, 21.61, 24.52, 21.61], Solar Cell 1: [Voltage: 1.84V, Current: 3.59mA], Solar Cell 2: [Voltage: 1.82V, Current: 4.24mA]
(Timestamp: 94225) Temperature Readings: [25.48, 23.55, 26.77, 23.87, 23.87, 21.94, 24.19, 22.26], Solar Cell 1: [Voltage: 2.13V, Current: 3.92mA], Solar Cell 2: [Voltage: 2.15V, Current: 4.90mA]
(Timestamp: 94727) Temperature Readings: [25.48, 23.55, 26.77, 23.87, 24.19, 21.94, 24.19, 22.26], Solar Cell 1: [Voltage: 2.18V, Current: 3.92mA], Solar Cell 2: [Voltage: 2.06V, Current: 4.90mA]
(Timestamp: 95233) Temperature Readings: [25.48, 23.55, 26.77, 23.87, 24.19, 21.94, 24.52, 22.26], Solar Cell 1: [Voltage: 2.15V, Current: 3.92mA], Solar Cell 2: [Voltage: 2.24V, Current: 4.90mA]
(Timestamp: 95736) Temperature Readings: [25.48, 23.55, 26.77, 23.87, 23.87, 21.94, 24.19, 22.26], Solar Cell 1: [Voltage: 2.08V, Current: 3.59mA], Solar Cell 2: [Voltage: 1.92V, Current: 4.57mA]
(Timestamp: 96238) Temperature Readings: [25.48, 23.87, 26.45, 23.87, 24.19, 21.94, 24.52, 21.29], Solar Cell 1: [Voltage: 1.88V, Current: 3.92mA], Solar Cell 2: [Voltage: 2.16V, Current: 4.90mA]
(Timestamp: 96741) Temperature Readings: [25.48, 23.55, 26.77, 23.87, 23.87, 21.94, 24.52, 22.58], Solar Cell 1: [Voltage: 2.14V, Current: 4.24mA], Solar Cell 2: [Voltage: 3.12V, Current: 6.20mA]
(Timestamp: 97244) Temperature Readings: [25.48, 23.55, 26.77, 23.87, 23.87, 21.94, 24.52, 22.26], Solar Cell 1: [Voltage: 2.12V, Current: 3.92mA], Solar Cell 2: [Voltage: 2.63V, Current: 5.55mA]
(Timestamp: 97747) Temperature Readings: [25.48, 23.55, 26.45, 23.87, 24.19, 21.94, 24.19, 21.94], Solar Cell 1: [Voltage: 1.88V, Current: 3.92mA], Solar Cell 2: [Voltage: 2.31V, Current: 5.22mA]
(Timestamp: 98249) Temperature Readings: [25.48, 23.55, 26.77, 23.87, 23.87, 21.94, 24.52, 22.58], Solar Cell 1: [Voltage: 2.20V, Current: 3.92mA], Solar Cell 2: [Voltage: 3.13V, Current: 6.20mA]
(Timestamp: 98752) Temperature Readings: [25.48, 23.87, 26.45, 23.87, 24.19, 21.94, 24.52, 21.94], Solar Cell 1: [Voltage: 2.08V, Current: 3.59mA], Solar Cell 2: [Voltage: 2.24V, Current: 4.90mA]
(Timestamp: 99255) Temperature Readings: [25.48, 23.87, 26.45, 23.87, 24.19, 21.94, 24.52, 21.94], Solar Cell 1: [Voltage: 1.95V, Current: 3.92mA], Solar Cell 2: [Voltage: 2.67V, Current: 5.55mA]
(Timestamp: 99758) Temperature Readings: [25.81, 23.55, 26.45, 23.87, 24.19, 21.94, 24.19, 22.90], Solar Cell 1: [Voltage: 2.17V, Current: 3.92mA], Solar Cell 2: [Voltage: 3.14V, Current: 6.20mA]
(Timestamp: 100260) Temperature Readings: [25.81, 23.87, 26.45, 23.87, 24.19, 21.94, 24.52, 21.61], Solar Cell 1: [Voltage: 2.04V, Current: 3.59mA], Solar Cell 2: [Voltage: 1.86V, Current: 4.57mA]
(Timestamp: 100767) Temperature Readings: [25.48, 23.87, 26.77, 23.87, 24.19, 21.94, 24.52, 22.58], Solar Cell 1: [Voltage: 2.19V, Current: 3.92mA], Solar Cell 2: [Voltage: 3.09V, Current: 6.20mA]
(Timestamp: 101270) Temperature Readings: [25.48, 23.55, 26.45, 23.87, 24.19, 21.94, 24.52, 22.90], Solar Cell 1: [Voltage: 1.81V, Current: 3.59mA], Solar Cell 2: [Voltage: 0.93V, Current: 82.28mA]
(Timestamp: 101772) Temperature Readings: [25.81, 23.55, 26.45, 23.87, 23.87, 21.94, 24.52, 22.90], Solar Cell 1: [Voltage: 2.09V, Current: 3.92mA], Solar Cell 2: [Voltage: 3.08V, Current: 6.20mA]
(Timestamp: 102275) Temperature Readings: [25.81, 23.55, 26.45, 23.87, 24.19, 21.94, 24.19, 22.58], Solar Cell 1: [Voltage: 2.16V, Current: 3.92mA], Solar Cell 2: [Voltage: 2.98V, Current: 6.20mA]
(Timestamp: 102778) Temperature Readings: [25.48, 23.87, 26.45, 23.87, 24.19, 22.26, 24.19, 23.87], Solar Cell 1: [Voltage: 1.79V, Current: 3.59mA], Solar Cell 2: [Voltage: 1.20V, Current: 112.64mA]
(Timestamp: 103281) Temperature Readings: [25.81, 23.87, 26.77, 23.87, 24.19, 21.94, 24.52, 22.90], Solar Cell 1: [Voltage: 2.10V, Current: 3.92mA], Solar Cell 2: [Voltage: 3.10V, Current: 6.20mA]
(Timestamp: 103783) Temperature Readings: [25.48, 23.87, 26.45, 23.87, 23.87, 21.94, 24.52, 22.26], Solar Cell 1: [Voltage: 2.13V, Current: 3.92mA], Solar Cell 2: [Voltage: 2.88V, Current: 5.88mA]
(Timestamp: 104286) Temperature Readings: [25.81, 23.87, 26.45, 23.87, 24.19, 21.61, 24.52, 21.61], Solar Cell 1: [Voltage: 1.79V, Current: 3.59mA], Solar Cell 2: [Voltage: 1.55V, Current: 4.24mA]
(Timestamp: 104789) Temperature Readings: [25.48, 23.87, 26.45, 23.87, 24.19, 21.94, 24.52, 22.58], Solar Cell 1: [Voltage: 2.11V, Current: 3.92mA], Solar Cell 2: [Voltage: 3.12V, Current: 6.20mA]
(Timestamp: 105291) Temperature Readings: [25.48, 23.55, 26.77, 23.87, 23.87, 21.94, 24.52, 22.26], Solar Cell 1: [Voltage: 2.14V, Current: 3.92mA], Solar Cell 2: [Voltage: 2.96V, Current: 5.88mA]
(Timestamp: 105794) Temperature Readings: [26.13, 23.55, 26.13, 23.87, 24.19, 22.26, 24.52, 23.87], Solar Cell 1: [Voltage: 1.77V, Current: 3.59mA], Solar Cell 2: [Voltage: 1.21V, Current: 113.62mA]
(Timestamp: 106296) Temperature Readings: [26.13, 23.87, 26.45, 23.87, 23.87, 21.61, 24.52, 22.26], Solar Cell 1: [Voltage: 2.07V, Current: 3.92mA], Solar Cell 2: [Voltage: 3.10V, Current: 6.53mA]
(Timestamp: 106803) Temperature Readings: [25.81, 23.87, 26.13, 23.87, 23.87, 21.61, 24.52, 21.61], Solar Cell 1: [Voltage: 1.81V, Current: 3.59mA], Solar Cell 2: [Voltage: 1.95V, Current: 4.57mA]
(Timestamp: 107305) Temperature Readings: [25.81, 23.55, 26.45, 23.87, 24.19, 21.94, 24.52, 22.90], Solar Cell 1: [Voltage: 2.09V, Current: 3.92mA], Solar Cell 2: [Voltage: 3.14V, Current: 6.20mA]
(Timestamp: 107808) Temperature Readings: [25.81, 23.87, 26.45, 23.55, 24.19, 21.61, 24.52, 22.26], Solar Cell 1: [Voltage: 2.09V, Current: 3.92mA], Solar Cell 2: [Voltage: 2.77V, Current: 5.88mA]
(Timestamp: 108311) Temperature Readings: [25.81, 23.87, 26.45, 23.87, 24.19, 21.61, 24.52, 21.29], Solar Cell 1: [Voltage: 1.79V, Current: 3.92mA], Solar Cell 2: [Voltage: 1.95V, Current: 4.57mA]
(Timestamp: 108813) Temperature Readings: [25.48, 23.87, 26.45, 23.87, 24.19, 21.94, 24.52, 22.26], Solar Cell 1: [Voltage: 2.12V, Current: 3.92mA], Solar Cell 2: [Voltage: 3.14V, Current: 6.53mA]
(Timestamp: 109316) Temperature Readings: [25.81, 23.87, 26.45, 23.87, 24.19, 21.61, 24.52, 22.26], Solar Cell 1: [Voltage: 2.05V, Current: 3.59mA], Solar Cell 2: [Voltage: 2.59V, Current: 5.55mA]
(Timestamp: 109819) Temperature Readings: [25.81, 23.87, 26.13, 24.19, 24.19, 21.61, 24.52, 21.29], Solar Cell 1: [Voltage: 1.84V, Current: 3.59mA], Solar Cell 2: [Voltage: 2.31V, Current: 5.22mA]
(Timestamp: 110322) Temperature Readings: [25.81, 23.87, 26.45, 23.87, 24.19, 21.94, 24.52, 22.58], Solar Cell 1: [Voltage: 2.12V, Current: 3.92mA], Solar Cell 2: [Voltage: 3.15V, Current: 6.53mA]
(Timestamp: 110824) Temperature Readings: [25.81, 23.87, 26.45, 24.19, 24.19, 21.61, 24.52, 21.94], Solar Cell 1: [Voltage: 2.04V, Current: 3.92mA], Solar Cell 2: [Voltage: 2.38V, Current: 5.22mA]
(Timestamp: 111327) Temperature Readings: [25.81, 23.87, 26.45, 23.87, 24.19, 21.94, 24.52, 21.94], Solar Cell 1: [Voltage: 1.88V, Current: 3.59mA], Solar Cell 2: [Voltage: 2.57V, Current: 5.55mA]
(Timestamp: 111830) Temperature Readings: [25.81, 23.87, 26.45, 23.87, 23.87, 21.94, 24.52, 22.26], Solar Cell 1: [Voltage: 2.12V, Current: 3.92mA], Solar Cell 2: [Voltage: 3.15V, Current: 6.20mA]
(Timestamp: 112333) Temperature Readings: [25.81, 23.87, 26.45, 23.87, 24.19, 21.61, 24.52, 21.61], Solar Cell 1: [Voltage: 2.01V, Current: 3.59mA], Solar Cell 2: [Voltage: 2.10V, Current: 4.90mA]
(Timestamp: 112839) Temperature Readings: [25.81, 23.87, 26.45, 24.19, 24.19, 21.94, 24.52, 22.26], Solar Cell 1: [Voltage: 2.14V, Current: 3.92mA], Solar Cell 2: [Voltage: 3.11V, Current: 6.20mA]
(Timestamp: 113342) Temperature Readings: [26.13, 23.87, 26.13, 23.87, 24.19, 21.94, 24.52, 23.23], Solar Cell 1: [Voltage: 1.81V, Current: 3.59mA], Solar Cell 2: [Voltage: 0.95V, Current: 82.60mA]
(Timestamp: 113845) Temperature Readings: [25.81, 23.87, 26.45, 23.87, 24.19, 21.61, 24.52, 22.26], Solar Cell 1: [Voltage: 2.03V, Current: 3.92mA], Solar Cell 2: [Voltage: 3.06V, Current: 6.20mA]
(Timestamp: 114347) Temperature Readings: [26.13, 23.87, 26.45, 23.87, 23.87, 21.61, 24.52, 22.26], Solar Cell 1: [Voltage: 2.14V, Current: 3.92mA], Solar Cell 2: [Voltage: 3.08V, Current: 6.20mA]
(Timestamp: 114850) Temperature Readings: [26.13, 23.87, 26.13, 24.19, 24.19, 21.94, 24.52, 23.23], Solar Cell 1: [Voltage: 1.86V, Current: 3.59mA], Solar Cell 2: [Voltage: 0.98V, Current: 86.52mA]
(Timestamp: 115353) Temperature Readings: [25.81, 23.87, 26.45, 24.19, 24.19, 21.61, 24.52, 22.26], Solar Cell 1: [Voltage: 2.01V, Current: 3.92mA], Solar Cell 2: [Voltage: 3.01V, Current: 6.20mA]
(Timestamp: 115855) Temperature Readings: [25.81, 23.87, 26.45, 24.19, 24.19, 21.61, 24.52, 22.26], Solar Cell 1: [Voltage: 2.16V, Current: 3.92mA], Solar Cell 2: [Voltage: 3.14V, Current: 6.20mA]
(Timestamp: 116358) Temperature Readings: [25.81, 23.87, 26.13, 24.19, 24.19, 21.94, 24.52, 23.87], Solar Cell 1: [Voltage: 1.91V, Current: 3.59mA], Solar Cell 2: [Voltage: 1.24V, Current: 111.66mA]
(Timestamp: 116860) Temperature Readings: [26.13, 23.87, 26.45, 24.19, 24.19, 21.61, 24.52, 22.26], Solar Cell 1: [Voltage: 1.99V, Current: 3.92mA], Solar Cell 2: [Voltage: 2.93V, Current: 5.88mA]
(Timestamp: 117363) Temperature Readings: [26.13, 24.19, 26.45, 24.19, 24.19, 21.94, 24.52, 22.26], Solar Cell 1: [Voltage: 2.15V, Current: 3.92mA], Solar Cell 2: [Voltage: 3.15V, Current: 6.53mA]
(Timestamp: 117866) Temperature Readings: [26.13, 23.87, 26.13, 23.87, 24.19, 21.94, 24.52, 20.97], Solar Cell 1: [Voltage: 1.96V, Current: 3.59mA], Solar Cell 2: [Voltage: 1.55V, Current: 4.24mA]
(Timestamp: 118372) Temperature Readings: [25.81, 23.87, 26.45, 23.87, 24.19, 21.94, 24.52, 22.26], Solar Cell 1: [Voltage: 2.14V, Current: 3.92mA], Solar Cell 2: [Voltage: 3.06V, Current: 6.20mA]
(Timestamp: 118875) Temperature Readings: [26.13, 23.87, 26.13, 23.87, 24.19, 21.94, 24.52, 22.90], Solar Cell 1: [Voltage: 1.75V, Current: 3.26mA], Solar Cell 2: [Voltage: 0.94V, Current: 83.58mA]
(Timestamp: 119378) Temperature Readings: [25.81, 23.87, 26.45, 24.19, 24.19, 21.61, 24.52, 22.26], Solar Cell 1: [Voltage: 2.06V, Current: 3.92mA], Solar Cell 2: [Voltage: 3.09V, Current: 6.20mA]
(Timestamp: 119880) Temperature Readings: [26.13, 23.87, 26.45, 23.87, 24.19, 21.94, 24.52, 22.26], Solar Cell 1: [Voltage: 2.13V, Current: 3.92mA], Solar Cell 2: [Voltage: 3.02V, Current: 6.20mA]
(Timestamp: 120383) Temperature Readings: [26.13, 23.87, 26.13, 24.19, 24.52, 21.94, 24.52, 23.23], Solar Cell 1: [Voltage: 1.75V, Current: 3.26mA], Solar Cell 2: [Voltage: 1.02V, Current: 93.38mA]
(Timestamp: 120886) Temperature Readings: [26.13, 23.87, 26.45, 23.87, 24.19, 21.61, 24.52, 22.26], Solar Cell 1: [Voltage: 2.06V, Current: 3.92mA], Solar Cell 2: [Voltage: 3.10V, Current: 6.20mA]
(Timestamp: 121389) Temperature Readings: [26.13, 23.87, 26.45, 24.19, 24.19, 21.61, 24.52, 22.26], Solar Cell 1: [Voltage: 2.12V, Current: 3.92mA], Solar Cell 2: [Voltage: 2.98V, Current: 5.88mA]
(Timestamp: 121891) Temperature Readings: [25.81, 24.19, 26.13, 24.19, 24.52, 21.94, 24.52, 23.23], Solar Cell 1: [Voltage: 1.74V, Current: 3.26mA], Solar Cell 2: [Voltage: 1.15V, Current: 108.07mA]
(Timestamp: 122394) Temperature Readings: [26.13, 24.19, 26.45, 24.19, 24.19, 21.61, 24.52, 22.26], Solar Cell 1: [Voltage: 2.06V, Current: 3.92mA], Solar Cell 2: [Voltage: 3.12V, Current: 5.88mA]
(Timestamp: 122897) Temperature Readings: [26.13, 23.87, 26.45, 24.19, 24.19, 21.94, 24.52, 22.26], Solar Cell 1: [Voltage: 2.10V, Current: 3.92mA], Solar Cell 2: [Voltage: 2.94V, Current: 5.88mA]
(Timestamp: 123400) Temperature Readings: [26.13, 24.19, 26.13, 24.19, 24.19, 21.94, 24.52, 23.87], Solar Cell 1: [Voltage: 1.74V, Current: 3.59mA], Solar Cell 2: [Voltage: 1.33V, Current: 43.42mA]
(Timestamp: 123902) Temperature Readings: [26.13, 23.87, 26.45, 24.19, 24.19, 21.94, 24.52, 22.26], Solar Cell 1: [Voltage: 2.08V, Current: 3.92mA], Solar Cell 2: [Voltage: 3.12V, Current: 6.20mA]
(Timestamp: 124409) Temperature Readings: [26.13, 24.19, 26.13, 24.19, 24.19, 21.94, 24.52, 21.29], Solar Cell 1: [Voltage: 1.88V, Current: 3.92mA], Solar Cell 2: [Voltage: 2.63V, Current: 5.55mA]
(Timestamp: 124912) Temperature Readings: [26.45, 23.87, 26.45, 24.19, 24.19, 21.61, 24.19, 22.26], Solar Cell 1: [Voltage: 2.12V, Current: 3.92mA], Solar Cell 2: [Voltage: 3.15V, Current: 6.20mA]
(Timestamp: 125414) Temperature Readings: [26.13, 24.19, 26.45, 24.19, 24.19, 21.61, 24.52, 21.61], Solar Cell 1: [Voltage: 2.03V, Current: 3.59mA], Solar Cell 2: [Voltage: 2.27V, Current: 4.90mA]
(Timestamp: 125917) Temperature Readings: [26.13, 23.87, 26.13, 24.19, 24.52, 21.61, 24.52, 21.29], Solar Cell 1: [Voltage: 1.84V, Current: 3.59mA], Solar Cell 2: [Voltage: 2.35V, Current: 5.22mA]
(Timestamp: 126419) Temperature Readings: [26.13, 23.87, 26.45, 24.19, 24.19, 21.61, 24.52, 22.26], Solar Cell 1: [Voltage: 3.08V, Current: 4.90mA], Solar Cell 2: [Voltage: 3.15V, Current: 6.53mA]
(Timestamp: 126922) Temperature Readings: [26.13, 23.87, 26.45, 24.19, 24.19, 21.94, 24.52, 21.94], Solar Cell 1: [Voltage: 3.05V, Current: 4.90mA], Solar Cell 2: [Voltage: 2.68V, Current: 5.55mA]
(Timestamp: 127425) Temperature Readings: [26.13, 23.87, 25.81, 23.87, 24.19, 21.29, 24.52, 20.97], Solar Cell 1: [Voltage: 2.68V, Current: 4.57mA], Solar Cell 2: [Voltage: 1.75V, Current: 4.24mA]
(Timestamp: 127927) Temperature Readings: [25.81, 23.87, 26.45, 24.19, 24.52, 21.94, 24.52, 22.26], Solar Cell 1: [Voltage: 2.09V, Current: 3.92mA], Solar Cell 2: [Voltage: 3.12V, Current: 6.20mA]
(Timestamp: 128430) Temperature Readings: [26.13, 23.87, 26.13, 24.19, 24.19, 21.94, 24.52, 22.26], Solar Cell 1: [Voltage: 2.10V, Current: 3.92mA], Solar Cell 2: [Voltage: 2.85V, Current: 6.20mA]
(Timestamp: 128933) Temperature Readings: [25.81, 24.19, 26.13, 23.87, 24.52, 21.29, 24.52, 20.97], Solar Cell 1: [Voltage: 1.77V, Current: 3.59mA], Solar Cell 2: [Voltage: 1.68V, Current: 4.24mA]
(Timestamp: 129435) Temperature Readings: [26.13, 24.19, 26.45, 24.19, 24.19, 21.61, 24.52, 22.26], Solar Cell 1: [Voltage: 2.10V, Current: 3.92mA], Solar Cell 2: [Voltage: 3.14V, Current: 6.20mA]
(Timestamp: 129938) Temperature Readings: [26.13, 24.19, 26.13, 24.19, 24.52, 21.94, 24.52, 22.26], Solar Cell 1: [Voltage: 2.08V, Current: 3.92mA], Solar Cell 2: [Voltage: 2.75V, Current: 5.88mA]
(Timestamp: 130445) Temperature Readings: [25.81, 23.87, 26.45, 24.19, 24.19, 21.94, 24.52, 22.26], Solar Cell 1: [Voltage: 2.13V, Current: 3.92mA], Solar Cell 2: [Voltage: 3.15V, Current: 6.20mA]
(Timestamp: 130947) Temperature Readings: [26.13, 24.19, 26.13, 24.19, 24.19, 21.29, 26.77, 20.97], Solar Cell 1: [Voltage: 1.96V, Current: 3.59mA], Solar Cell 2: [Voltage: 1.70V, Current: 4.24mA]
(Timestamp: 131450) Temperature Readings: [25.81, 24.19, 26.45, 24.19, 24.19, 21.94, 24.84, 21.94], Solar Cell 1: [Voltage: 1.92V, Current: 3.59mA], Solar Cell 2: [Voltage: 2.86V, Current: 5.88mA]
(Timestamp: 131953) Temperature Readings: [26.13, 24.19, 26.45, 24.19, 24.52, 21.61, 24.52, 22.26], Solar Cell 1: [Voltage: 2.12V, Current: 3.92mA], Solar Cell 2: [Voltage: 3.15V, Current: 6.53mA]
(Timestamp: 132456) Temperature Readings: [26.13, 23.87, 26.13, 24.19, 24.19, 21.29, 24.84, 20.97], Solar Cell 1: [Voltage: 1.94V, Current: 3.59mA], Solar Cell 2: [Voltage: 1.62V, Current: 4.24mA]
(Timestamp: 132958) Temperature Readings: [26.13, 23.87, 26.13, 24.19, 24.52, 21.94, 24.52, 22.26], Solar Cell 1: [Voltage: 1.94V, Current: 3.92mA], Solar Cell 2: [Voltage: 2.88V, Current: 5.88mA]
(Timestamp: 133461) Temperature Readings: [26.13, 24.19, 26.13, 24.19, 24.52, 21.94, 24.52, 22.26], Solar Cell 1: [Voltage: 2.12V, Current: 3.92mA], Solar Cell 2: [Voltage: 3.14V, Current: 6.20mA]
(Timestamp: 133964) Temperature Readings: [26.13, 24.19, 26.13, 24.19, 24.52, 21.61, 24.52, 20.97], Solar Cell 1: [Voltage: 1.91V, Current: 3.26mA], Solar Cell 2: [Voltage: 1.41V, Current: 20.90mA]
(Timestamp: 134467) Temperature Readings: [26.13, 24.19, 26.13, 24.19, 24.52, 21.94, 24.52, 22.26], Solar Cell 1: [Voltage: 1.96V, Current: 3.92mA], Solar Cell 2: [Voltage: 2.94V, Current: 6.20mA]
(Timestamp: 134969) Temperature Readings: [26.13, 24.19, 26.45, 24.19, 24.19, 21.61, 24.52, 22.26], Solar Cell 1: [Voltage: 2.12V, Current: 3.92mA], Solar Cell 2: [Voltage: 3.14V, Current: 6.20mA]
(Timestamp: 135472) Temperature Readings: [26.13, 24.19, 26.13, 24.19, 24.52, 21.29, 24.52, 21.61], Solar Cell 1: [Voltage: 1.89V, Current: 3.59mA], Solar Cell 2: [Voltage: 1.30V, Current: 115.91mA]
(Timestamp: 135975) Temperature Readings: [26.45, 24.19, 26.13, 24.19, 24.19, 21.61, 24.52, 21.29], Solar Cell 1: [Voltage: 1.93V, Current: 3.92mA], Solar Cell 2: [Voltage: 2.86V, Current: 5.88mA]
(Timestamp: 136481) Temperature Readings: [26.13, 24.19, 25.81, 24.19, 24.19, 21.94, 24.52, 23.23], Solar Cell 1: [Voltage: 1.83V, Current: 3.26mA], Solar Cell 2: [Voltage: 1.03V, Current: 91.42mA]
(Timestamp: 136984) Temperature Readings: [26.45, 24.19, 26.45, 24.19, 24.52, 21.61, 24.52, 22.26], Solar Cell 1: [Voltage: 2.00V, Current: 3.92mA], Solar Cell 2: [Voltage: 3.01V, Current: 6.20mA]
(Timestamp: 137486) Temperature Readings: [26.45, 24.19, 26.45, 24.52, 24.52, 21.61, 24.84, 22.26], Solar Cell 1: [Voltage: 2.12V, Current: 3.92mA], Solar Cell 2: [Voltage: 3.13V, Current: 6.20mA]
(Timestamp: 137989) Temperature Readings: [26.45, 24.19, 26.13, 24.19, 24.52, 21.29, 24.52, 20.97], Solar Cell 1: [Voltage: 1.94V, Current: 3.59mA], Solar Cell 2: [Voltage: 1.53V, Current: 4.57mA]
(Timestamp: 138491) Temperature Readings: [26.13, 24.19, 26.13, 24.19, 24.52, 21.61, 24.52, 21.61], Solar Cell 1: [Voltage: 1.91V, Current: 3.59mA], Solar Cell 2: [Voltage: 2.79V, Current: 5.88mA]
(Timestamp: 138994) Temperature Readings: [26.45, 24.19, 26.13, 24.19, 24.52, 21.94, 24.52, 22.26], Solar Cell 1: [Voltage: 2.11V, Current: 3.92mA], Solar Cell 2: [Voltage: 3.15V, Current: 6.20mA]
(Timestamp: 139497) Temperature Readings: [26.13, 24.19, 26.13, 24.19, 24.19, 21.29, 24.84, 20.97], Solar Cell 1: [Voltage: 1.94V, Current: 3.59mA], Solar Cell 2: [Voltage: 1.71V, Current: 4.24mA]
(Timestamp: 139999) Temperature Readings: [26.45, 24.52, 26.13, 24.19, 24.52, 21.61, 24.84, 21.94], Solar Cell 1: [Voltage: 1.92V, Current: 3.92mA], Solar Cell 2: [Voltage: 2.85V, Current: 5.88mA]
(Timestamp: 140502) Temperature Readings: [26.45, 24.19, 26.45, 24.19, 24.52, 21.61, 24.52, 21.94], Solar Cell 1: [Voltage: 2.12V, Current: 3.92mA], Solar Cell 2: [Voltage: 3.14V, Current: 6.53mA]
(Timestamp: 141005) Temperature Readings: [26.13, 24.19, 26.13, 24.19, 24.52, 21.29, 24.84, 20.97], Solar Cell 1: [Voltage: 1.92V, Current: 3.59mA], Solar Cell 2: [Voltage: 1.54V, Current: 4.57mA]
(Timestamp: 141508) Temperature Readings: [26.77, 24.19, 26.13, 24.19, 24.52, 21.61, 24.84, 21.61], Solar Cell 1: [Voltage: 2.94V, Current: 5.22mA], Solar Cell 2: [Voltage: 2.92V, Current: 5.88mA]
(Timestamp: 142014) Temperature Readings: [26.45, 24.19, 25.81, 24.19, 24.52, 21.61, 24.84, 22.58], Solar Cell 1: [Voltage: 2.66V, Current: 4.24mA], Solar Cell 2: [Voltage: 0.92V, Current: 81.30mA]
(Timestamp: 142517) Temperature Readings: [26.45, 24.19, 26.13, 24.19, 24.52, 21.61, 24.84, 22.26], Solar Cell 1: [Voltage: 3.06V, Current: 4.90mA], Solar Cell 2: [Voltage: 3.10V, Current: 6.20mA]
(Timestamp: 143020) Temperature Readings: [26.13, 24.19, 26.13, 24.19, 24.52, 21.61, 24.52, 21.94], Solar Cell 1: [Voltage: 3.14V, Current: 4.90mA], Solar Cell 2: [Voltage: 3.00V, Current: 6.20mA]
(Timestamp: 143522) Temperature Readings: [26.45, 24.19, 25.81, 24.19, 24.52, 21.61, 24.84, 22.90], Solar Cell 1: [Voltage: 2.62V, Current: 4.24mA], Solar Cell 2: [Voltage: 1.10V, Current: 103.17mA]
(Timestamp: 144025) Temperature Readings: [26.77, 24.52, 26.13, 24.19, 24.52, 21.61, 24.52, 22.26], Solar Cell 1: [Voltage: 3.08V, Current: 4.90mA], Solar Cell 2: [Voltage: 3.11V, Current: 6.20mA]
(Timestamp: 144528) Temperature Readings: [26.45, 24.19, 26.13, 24.52, 24.52, 21.61, 24.84, 22.26], Solar Cell 1: [Voltage: 3.12V, Current: 4.90mA], Solar Cell 2: [Voltage: 2.94V, Current: 5.88mA]
(Timestamp: 145031) Temperature Readings: [26.45, 24.52, 25.81, 24.19, 24.52, 21.94, 24.52, 23.23], Solar Cell 1: [Voltage: 2.63V, Current: 4.57mA], Solar Cell 2: [Voltage: 1.31V, Current: 71.50mA]
(Timestamp: 145534) Temperature Readings: [26.45, 24.52, 26.13, 24.19, 24.52, 21.61, 24.84, 22.26], Solar Cell 1: [Voltage: 3.09V, Current: 4.90mA], Solar Cell 2: [Voltage: 3.12V, Current: 6.20mA]
(Timestamp: 146036) Temperature Readings: [26.45, 24.19, 26.13, 24.19, 24.52, 21.61, 24.84, 21.94], Solar Cell 1: [Voltage: 3.14V, Current: 4.90mA], Solar Cell 2: [Voltage: 2.94V, Current: 5.88mA]
(Timestamp: 146539) Temperature Readings: [26.45, 24.19, 25.81, 24.19, 24.52, 21.61, 24.84, 22.90], Solar Cell 1: [Voltage: 2.62V, Current: 4.24mA], Solar Cell 2: [Voltage: 1.12V, Current: 103.83mA]
(Timestamp: 147041) Temperature Readings: [26.45, 24.19, 26.13, 24.52, 24.52, 21.94, 24.84, 21.94], Solar Cell 1: [Voltage: 3.07V, Current: 4.90mA], Solar Cell 2: [Voltage: 3.10V, Current: 6.20mA]
(Timestamp: 147544) Temperature Readings: [26.77, 24.52, 26.13, 24.52, 24.52, 21.61, 24.84, 22.26], Solar Cell 1: [Voltage: 3.14V, Current: 4.90mA], Solar Cell 2: [Voltage: 3.01V, Current: 6.20mA]
(Timestamp: 148050) Temperature Readings: [26.45, 24.52, 26.13, 24.52, 24.52, 21.61, 24.52, 22.26], Solar Cell 1: [Voltage: 3.11V, Current: 5.22mA], Solar Cell 2: [Voltage: 3.14V, Current: 6.20mA]
(Timestamp: 148553) Temperature Readings: [26.45, 24.52, 25.81, 24.52, 24.52, 21.61, 24.84, 21.61], Solar Cell 1: [Voltage: 3.10V, Current: 4.90mA], Solar Cell 2: [Voltage: 2.83V, Current: 5.88mA]
(Timestamp: 149055) Temperature Readings: [26.45, 24.52, 25.81, 24.52, 24.52, 20.97, 24.84, 20.97], Solar Cell 1: [Voltage: 2.67V, Current: 4.90mA], Solar Cell 2: [Voltage: 1.75V, Current: 4.24mA]
(Timestamp: 149558) Temperature Readings: [26.77, 24.19, 26.13, 24.52, 24.52, 21.61, 24.84, 22.26], Solar Cell 1: [Voltage: 3.11V, Current: 4.90mA], Solar Cell 2: [Voltage: 3.14V, Current: 6.20mA]
(Timestamp: 150061) Temperature Readings: [26.45, 24.19, 26.13, 24.52, 24.52, 21.29, 24.52, 21.61], Solar Cell 1: [Voltage: 3.09V, Current: 4.90mA], Solar Cell 2: [Voltage: 2.72V, Current: 5.55mA]
(Timestamp: 150564) Temperature Readings: [26.45, 24.84, 25.81, 24.52, 24.52, 20.97, 24.84, 20.65], Solar Cell 1: [Voltage: 2.70V, Current: 4.57mA], Solar Cell 2: [Voltage: 2.05V, Current: 4.90mA]
(Timestamp: 151066) Temperature Readings: [26.45, 24.52, 26.13, 24.52, 24.52, 21.61, 24.84, 22.26], Solar Cell 1: [Voltage: 3.11V, Current: 5.22mA], Solar Cell 2: [Voltage: 3.14V, Current: 6.53mA]
(Timestamp: 151569) Temperature Readings: [26.45, 24.52, 26.13, 24.19, 24.52, 21.29, 24.84, 21.29], Solar Cell 1: [Voltage: 3.10V, Current: 4.90mA], Solar Cell 2: [Voltage: 2.79V, Current: 5.55mA]
(Timestamp: 152072) Temperature Readings: [26.45, 24.52, 25.81, 24.52, 24.52, 20.97, 24.84, 20.65], Solar Cell 1: [Voltage: 2.67V, Current: 4.57mA], Solar Cell 2: [Voltage: 1.79V, Current: 4.57mA]
(Timestamp: 152574) Temperature Readings: [26.77, 24.52, 26.13, 24.84, 24.52, 21.61, 24.84, 22.26], Solar Cell 1: [Voltage: 3.10V, Current: 4.90mA], Solar Cell 2: [Voltage: 3.13V, Current: 6.53mA]
(Timestamp: 153077) Temperature Readings: [26.45, 24.52, 26.13, 24.52, 24.52, 21.29, 24.52, 21.61], Solar Cell 1: [Voltage: 3.09V, Current: 4.90mA], Solar Cell 2: [Voltage: 2.75V, Current: 5.88mA]
(Timestamp: 153580) Temperature Readings: [26.77, 24.52, 25.81, 24.52, 24.52, 20.97, 24.84, 20.97], Solar Cell 1: [Voltage: 2.67V, Current: 4.57mA], Solar Cell 2: [Voltage: 1.90V, Current: 4.57mA]
(Timestamp: 154086) Temperature Readings: [26.45, 24.84, 26.13, 24.52, 24.52, 20.97, 24.84, 20.97], Solar Cell 1: [Voltage: 2.95V, Current: 4.57mA], Solar Cell 2: [Voltage: 1.80V, Current: 4.57mA]
(Timestamp: 154589) Temperature Readings: [26.77, 24.84, 26.13, 24.52, 24.52, 21.29, 24.84, 21.61], Solar Cell 1: [Voltage: 2.88V, Current: 4.90mA], Solar Cell 2: [Voltage: 2.83V, Current: 5.88mA]
(Timestamp: 155092) Temperature Readings: [26.45, 24.52, 25.81, 24.52, 24.84, 21.29, 25.48, 21.94], Solar Cell 1: [Voltage: 3.15V, Current: 5.22mA], Solar Cell 2: [Voltage: 3.15V, Current: 6.20mA]
(Timestamp: 155595) Temperature Readings: [26.77, 24.52, 25.81, 24.52, 24.84, 20.97, 24.84, 20.97], Solar Cell 1: [Voltage: 2.94V, Current: 4.57mA], Solar Cell 2: [Voltage: 1.69V, Current: 4.24mA]
(Timestamp: 156097) Temperature Readings: [26.77, 24.52, 25.81, 24.52, 24.52, 21.29, 24.84, 21.61], Solar Cell 1: [Voltage: 2.89V, Current: 4.90mA], Solar Cell 2: [Voltage: 2.84V, Current: 5.88mA]
(Timestamp: 156600) Temperature Readings: [26.77, 24.52, 26.13, 24.52, 24.52, 21.61, 24.84, 22.26], Solar Cell 1: [Voltage: 3.15V, Current: 4.90mA], Solar Cell 2: [Voltage: 3.15V, Current: 6.53mA]
(Timestamp: 157103) Temperature Readings: [26.77, 24.52, 26.13, 24.52, 24.52, 21.29, 24.84, 21.61], Solar Cell 1: [Voltage: 3.03V, Current: 4.57mA], Solar Cell 2: [Voltage: 2.32V, Current: 4.90mA]
(Timestamp: 157605) Temperature Readings: [26.77, 24.52, 25.81, 24.52, 24.52, 21.29, 24.84, 21.29], Solar Cell 1: [Voltage: 2.79V, Current: 4.90mA], Solar Cell 2: [Voltage: 2.48V, Current: 5.55mA]
(Timestamp: 158108) Temperature Readings: [26.45, 24.52, 26.13, 24.19, 24.52, 21.29, 24.84, 21.94], Solar Cell 1: [Voltage: 3.14V, Current: 5.22mA], Solar Cell 2: [Voltage: 3.14V, Current: 6.20mA]
(Timestamp: 158610) Temperature Readings: [26.77, 24.52, 26.13, 24.52, 24.52, 21.61, 24.52, 21.61], Solar Cell 1: [Voltage: 3.10V, Current: 4.90mA], Solar Cell 2: [Voltage: 2.77V, Current: 5.88mA]
(Timestamp: 159113) Temperature Readings: [27.10, 24.84, 25.48, 24.52, 24.52, 21.94, 24.84, 22.90], Solar Cell 1: [Voltage: 2.63V, Current: 4.57mA], Solar Cell 2: [Voltage: 1.40V, Current: 10.77mA]
(Timestamp: 159619) Temperature Readings: [26.77, 24.19, 26.13, 24.52, 24.52, 21.29, 24.84, 21.29], Solar Cell 1: [Voltage: 3.03V, Current: 4.57mA], Solar Cell 2: [Voltage: 2.32V, Current: 5.22mA]
(Timestamp: 160122) Temperature Readings: [26.77, 24.52, 25.81, 24.52, 24.52, 21.29, 24.84, 21.29], Solar Cell 1: [Voltage: 2.81V, Current: 4.90mA], Solar Cell 2: [Voltage: 2.59V, Current: 5.55mA]
(Timestamp: 160625) Temperature Readings: [26.45, 24.52, 26.13, 24.52, 24.52, 21.29, 24.84, 22.26], Solar Cell 1: [Voltage: 3.14V, Current: 5.22mA], Solar Cell 2: [Voltage: 3.15V, Current: 6.20mA]
(Timestamp: 161128) Temperature Readings: [26.45, 24.52, 26.13, 24.52, 24.52, 20.97, 24.84, 21.29], Solar Cell 1: [Voltage: 3.02V, Current: 4.57mA], Solar Cell 2: [Voltage: 2.25V, Current: 4.90mA]
(Timestamp: 161630) Temperature Readings: [26.77, 24.84, 25.81, 24.52, 24.52, 20.97, 24.84, 21.29], Solar Cell 1: [Voltage: 2.80V, Current: 4.90mA], Solar Cell 2: [Voltage: 2.57V, Current: 5.55mA]
(Timestamp: 162133) Temperature Readings: [26.77, 24.84, 26.13, 24.52, 24.84, 21.61, 24.84, 22.26], Solar Cell 1: [Voltage: 3.14V, Current: 4.90mA], Solar Cell 2: [Voltage: 3.14V, Current: 6.20mA]
(Timestamp: 162636) Temperature Readings: [26.77, 24.52, 26.13, 24.52, 24.52, 20.97, 24.84, 21.61], Solar Cell 1: [Voltage: 3.03V, Current: 4.57mA], Solar Cell 2: [Voltage: 2.33V, Current: 5.22mA]
(Timestamp: 163139) Temperature Readings: [26.77, 24.84, 25.81, 24.52, 24.52, 20.97, 24.84, 21.61], Solar Cell 1: [Voltage: 2.78V, Current: 4.90mA], Solar Cell 2: [Voltage: 2.49V, Current: 5.55mA]
(Timestamp: 163641) Temperature Readings: [26.77, 24.84, 26.13, 24.52, 24.52, 21.29, 24.84, 21.94], Solar Cell 1: [Voltage: 3.13V, Current: 5.22mA], Solar Cell 2: [Voltage: 3.15V, Current: 6.53mA]
(Timestamp: 164144) Temperature Readings: [26.77, 24.52, 26.13, 24.52, 24.84, 21.29, 24.84, 21.61], Solar Cell 1: [Voltage: 3.04V, Current: 4.57mA], Solar Cell 2: [Voltage: 2.39V, Current: 5.22mA]
(Timestamp: 164647) Temperature Readings: [26.77, 24.52, 25.81, 24.52, 24.52, 20.97, 24.84, 20.97], Solar Cell 1: [Voltage: 2.77V, Current: 4.57mA], Solar Cell 2: [Voltage: 2.45V, Current: 5.55mA]
(Timestamp: 165150) Temperature Readings: [26.77, 24.84, 26.13, 24.52, 24.52, 21.29, 25.16, 21.61], Solar Cell 1: [Voltage: 3.13V, Current: 4.90mA], Solar Cell 2: [Voltage: 3.15V, Current: 6.20mA]
(Timestamp: 165656) Temperature Readings: [26.77, 24.84, 25.81, 24.52, 24.84, 21.29, 24.84, 21.29], Solar Cell 1: [Voltage: 2.93V, Current: 4.90mA], Solar Cell 2: [Voltage: 2.95V, Current: 5.88mA]
(Timestamp: 166159) Temperature Readings: [26.77, 24.84, 26.13, 24.52, 24.52, 21.29, 24.84, 21.94], Solar Cell 1: [Voltage: 3.15V, Current: 5.22mA], Solar Cell 2: [Voltage: 3.14V, Current: 6.20mA]
(Timestamp: 166662) Temperature Readings: [26.77, 24.84, 25.81, 24.52, 24.84, 20.97, 24.84, 21.61], Solar Cell 1: [Voltage: 2.85V, Current: 4.24mA], Solar Cell 2: [Voltage: 1.28V, Current: 115.25mA]
(Timestamp: 167164) Temperature Readings: [27.10, 24.84, 25.81, 24.52, 24.84, 21.29, 24.84, 21.61], Solar Cell 1: [Voltage: 2.90V, Current: 4.90mA], Solar Cell 2: [Voltage: 2.86V, Current: 5.88mA]
(Timestamp: 167667) Temperature Readings: [26.77, 24.84, 26.13, 24.52, 24.84, 21.29, 24.84, 21.94], Solar Cell 1: [Voltage: 3.14V, Current: 4.90mA], Solar Cell 2: [Voltage: 3.15V, Current: 6.20mA]
(Timestamp: 168169) Temperature Readings: [27.10, 24.84, 26.13, 24.52, 24.84, 20.97, 24.84, 20.97], Solar Cell 1: [Voltage: 2.99V, Current: 4.57mA], Solar Cell 2: [Voltage: 2.17V, Current: 4.90mA]
(Timestamp: 168672) Temperature Readings: [27.10, 24.84, 25.81, 24.52, 24.84, 21.29, 24.84, 20.97], Solar Cell 1: [Voltage: 2.74V, Current: 4.90mA], Solar Cell 2: [Voltage: 2.39V, Current: 5.22mA]
(Timestamp: 169175) Temperature Readings: [26.77, 24.84, 26.13, 24.52, 24.52, 21.29, 25.16, 21.94], Solar Cell 1: [Voltage: 3.10V, Current: 4.90mA], Solar Cell 2: [Voltage: 3.14V, Current: 6.20mA]
(Timestamp: 169677) Temperature Readings: [26.77, 24.84, 26.13, 24.52, 24.84, 20.97, 24.84, 21.61], Solar Cell 1: [Voltage: 3.09V, Current: 4.90mA], Solar Cell 2: [Voltage: 2.83V, Current: 5.55mA]
(Timestamp: 170180) Temperature Readings: [26.77, 24.84, 25.81, 24.52, 24.84, 20.97, 24.84, 20.32], Solar Cell 1: [Voltage: 2.62V, Current: 4.57mA], Solar Cell 2: [Voltage: 1.57V, Current: 4.24mA]
(Timestamp: 170683) Temperature Readings: [26.77, 24.84, 26.13, 24.52, 24.84, 21.29, 24.84, 21.94], Solar Cell 1: [Voltage: 3.08V, Current: 4.90mA], Solar Cell 2: [Voltage: 3.13V, Current: 6.20mA]
(Timestamp: 171185) Temperature Readings: [27.10, 24.84, 26.13, 24.52, 24.84, 21.29, 25.16, 21.61], Solar Cell 1: [Voltage: 3.09V, Current: 4.90mA], Solar Cell 2: [Voltage: 2.86V, Current: 5.88mA]
(Timestamp: 171692) Temperature Readings: [27.10, 24.52, 26.13, 24.52, 24.84, 21.29, 24.84, 22.26], Solar Cell 1: [Voltage: 3.12V, Current: 4.90mA], Solar Cell 2: [Voltage: 3.15V, Current: 6.53mA]
(Timestamp: 172195) Temperature Readings: [26.77, 24.84, 25.81, 24.52, 24.84, 20.97, 24.84, 20.97], Solar Cell 1: [Voltage: 2.97V, Current: 4.90mA], Solar Cell 2: [Voltage: 2.10V, Current: 4.90mA]
(Timestamp: 172697) Temperature Readings: [26.77, 24.84, 25.81, 24.84, 24.84, 20.97, 24.84, 21.29], Solar Cell 1: [Voltage: 2.80V, Current: 4.90mA], Solar Cell 2: [Voltage: 2.67V, Current: 5.55mA]
(Timestamp: 173200) Temperature Readings: [26.77, 24.84, 26.13, 24.84, 24.84, 21.29, 24.84, 21.61], Solar Cell 1: [Voltage: 3.12V, Current: 5.22mA], Solar Cell 2: [Voltage: 3.15V, Current: 6.20mA]
(Timestamp: 173703) Temperature Readings: [26.77, 24.84, 25.81, 24.52, 24.84, 20.97, 24.84, 20.97], Solar Cell 1: [Voltage: 2.97V, Current: 4.57mA], Solar Cell 2: [Voltage: 2.10V, Current: 4.90mA]
(Timestamp: 174206) Temperature Readings: [27.10, 24.84, 25.81, 24.52, 24.84, 20.97, 24.84, 21.61], Solar Cell 1: [Voltage: 2.79V, Current: 4.90mA], Solar Cell 2: [Voltage: 2.65V, Current: 5.55mA]
(Timestamp: 174708) Temperature Readings: [26.77, 25.16, 26.13, 24.84, 24.84, 21.29, 25.16, 21.61], Solar Cell 1: [Voltage: 3.11V, Current: 5.22mA], Solar Cell 2: [Voltage: 3.15V, Current: 6.53mA]
(Timestamp: 175211) Temperature Readings: [27.10, 24.84, 25.81, 24.52, 24.84, 20.97, 24.84, 20.97], Solar Cell 1: [Voltage: 2.97V, Current: 4.57mA], Solar Cell 2: [Voltage: 2.15V, Current: 4.90mA]
(Timestamp: 175714) Temperature Readings: [27.42, 24.84, 25.81, 24.52, 24.84, 20.97, 24.84, 21.29], Solar Cell 1: [Voltage: 2.79V, Current: 4.90mA], Solar Cell 2: [Voltage: 2.65V, Current: 5.55mA]
(Timestamp: 176217) Temperature Readings: [27.10, 24.84, 25.81, 24.52, 24.84, 21.61, 24.84, 21.94], Solar Cell 1: [Voltage: 3.10V, Current: 5.22mA], Solar Cell 2: [Voltage: 3.15V, Current: 6.53mA]
(Timestamp: 176720) Temperature Readings: [27.10, 24.84, 26.13, 24.52, 24.84, 20.97, 24.84, 20.97], Solar Cell 1: [Voltage: 2.97V, Current: 4.57mA], Solar Cell 2: [Voltage: 2.14V, Current: 4.90mA]
(Timestamp: 177222) Temperature Readings: [27.10, 24.84, 25.81, 24.52, 24.84, 20.97, 24.84, 20.97], Solar Cell 1: [Voltage: 2.72V, Current: 4.57mA], Solar Cell 2: [Voltage: 2.39V, Current: 5.22mA]
(Timestamp: 177728) Temperature Readings: [27.10, 24.84, 25.81, 24.84, 24.52, 20.97, 25.16, 20.65], Solar Cell 1: [Voltage: 2.89V, Current: 4.57mA], Solar Cell 2: [Voltage: 1.66V, Current: 4.24mA]
(Timestamp: 178231) Temperature Readings: [26.77, 24.84, 25.81, 24.84, 24.84, 20.97, 24.84, 21.61], Solar Cell 1: [Voltage: 2.79V, Current: 4.90mA], Solar Cell 2: [Voltage: 2.71V, Current: 5.55mA]
(Timestamp: 178733) Temperature Readings: [27.10, 24.52, 26.13, 24.84, 24.84, 21.29, 25.16, 21.61], Solar Cell 1: [Voltage: 3.10V, Current: 5.22mA], Solar Cell 2: [Voltage: 3.15V, Current: 6.20mA]
(Timestamp: 179236) Temperature Readings: [26.77, 24.84, 25.81, 24.52, 24.84, 20.97, 24.84, 21.29], Solar Cell 1: [Voltage: 3.01V, Current: 4.57mA], Solar Cell 2: [Voltage: 2.48V, Current: 5.22mA]
(Timestamp: 179738) Temperature Readings: [27.10, 24.84, 25.81, 24.52, 24.84, 20.97, 24.84, 20.65], Solar Cell 1: [Voltage: 2.65V, Current: 4.57mA], Solar Cell 2: [Voltage: 1.97V, Current: 4.57mA]
(Timestamp: 180241) Temperature Readings: [27.10, 24.84, 26.13, 24.84, 24.84, 21.29, 25.16, 21.61], Solar Cell 1: [Voltage: 3.07V, Current: 5.22mA], Solar Cell 2: [Voltage: 3.13V, Current: 6.20mA]
(Timestamp: 180744) Temperature Readings: [27.10, 24.84, 25.81, 24.52, 24.84, 21.29, 25.16, 21.61], Solar Cell 1: [Voltage: 3.05V, Current: 4.90mA], Solar Cell 2: [Voltage: 2.72V, Current: 5.55mA]
(Timestamp: 181247) Temperature Readings: [27.10, 24.84, 25.48, 24.84, 24.84, 20.65, 24.84, 20.32], Solar Cell 1: [Voltage: 2.64V, Current: 4.57mA], Solar Cell 2: [Voltage: 1.90V, Current: 4.57mA]
(Timestamp: 181750) Temperature Readings: [27.10, 25.16, 26.13, 24.84, 24.84, 20.97, 24.84, 21.61], Solar Cell 1: [Voltage: 3.08V, Current: 4.90mA], Solar Cell 2: [Voltage: 3.14V, Current: 6.20mA]
(Timestamp: 182252) Temperature Readings: [27.10, 24.84, 25.81, 24.84, 24.84, 20.97, 24.84, 21.61], Solar Cell 1: [Voltage: 3.06V, Current: 4.90mA], Solar Cell 2: [Voltage: 2.75V, Current: 5.88mA]
(Timestamp: 182755) Temperature Readings: [27.10, 24.84, 25.48, 24.84, 24.84, 20.97, 24.84, 20.32], Solar Cell 1: [Voltage: 2.62V, Current: 4.57mA], Solar Cell 2: [Voltage: 1.77V, Current: 4.57mA]
(Timestamp: 183261) Temperature Readings: [27.10, 24.84, 25.81, 24.84, 24.84, 20.97, 24.84, 20.97], Solar Cell 1: [Voltage: 2.94V, Current: 4.57mA], Solar Cell 2: [Voltage: 1.96V, Current: 4.57mA]
(Timestamp: 183764) Temperature Readings: [27.10, 25.16, 25.81, 24.84, 24.84, 20.97, 25.16, 21.61], Solar Cell 1: [Voltage: 2.83V, Current: 4.90mA], Solar Cell 2: [Voltage: 2.77V, Current: 5.88mA]
(Timestamp: 184267) Temperature Readings: [26.45, 24.84, 26.13, 24.84, 24.84, 21.29, 24.84, 21.61], Solar Cell 1: [Voltage: 3.12V, Current: 4.90mA], Solar Cell 2: [Voltage: 3.15V, Current: 6.20mA]
(Timestamp: 184770) Temperature Readings: [27.10, 25.16, 25.81, 24.84, 24.84, 20.97, 25.16, 20.97], Solar Cell 1: [Voltage: 2.94V, Current: 4.57mA], Solar Cell 2: [Voltage: 1.95V, Current: 4.57mA]
(Timestamp: 185273) Temperature Readings: [27.10, 24.84, 25.81, 24.52, 24.84, 21.29, 24.84, 21.29], Solar Cell 1: [Voltage: 2.81V, Current: 4.90mA], Solar Cell 2: [Voltage: 2.72V, Current: 5.55mA]
(Timestamp: 185775) Temperature Readings: [27.10, 25.16, 26.13, 24.52, 24.84, 20.97, 24.52, 21.61], Solar Cell 1: [Voltage: 3.11V, Current: 4.90mA], Solar Cell 2: [Voltage: 3.14V, Current: 6.20mA]
(Timestamp: 186278) Temperature Readings: [27.10, 24.84, 25.81, 24.84, 24.84, 20.97, 25.16, 20.97], Solar Cell 1: [Voltage: 2.95V, Current: 4.57mA], Solar Cell 2: [Voltage: 2.05V, Current: 4.57mA]
(Timestamp: 186781) Temperature Readings: [27.10, 25.16, 25.81, 24.84, 24.84, 20.97, 24.84, 21.61], Solar Cell 1: [Voltage: 2.80V, Current: 4.90mA], Solar Cell 2: [Voltage: 2.70V, Current: 5.88mA]
(Timestamp: 187284) Temperature Readings: [27.10, 25.16, 25.81, 24.84, 24.84, 21.29, 25.16, 21.61], Solar Cell 1: [Voltage: 3.12V, Current: 5.22mA], Solar Cell 2: [Voltage: 3.15V, Current: 6.20mA]
(Timestamp: 187786) Temperature Readings: [27.10, 25.16, 25.81, 24.84, 24.84, 20.97, 25.16, 20.97], Solar Cell 1: [Voltage: 3.00V, Current: 4.90mA], Solar Cell 2: [Voltage: 2.35V, Current: 5.22mA]
(Timestamp: 188289) Temperature Readings: [27.10, 25.16, 25.48, 24.84, 25.16, 20.97, 25.16, 20.97], Solar Cell 1: [Voltage: 2.68V, Current: 4.57mA], Solar Cell 2: [Voltage: 2.17V, Current: 4.90mA]
(Timestamp: 188792) Temperature Readings: [27.10, 25.16, 26.13, 24.84, 24.84, 21.29, 25.16, 21.61], Solar Cell 1: [Voltage: 3.09V, Current: 5.22mA], Solar Cell 2: [Voltage: 3.14V, Current: 5.88mA]
(Timestamp: 189298) Temperature Readings: [27.42, 25.16, 25.81, 24.84, 24.84, 20.97, 25.16, 21.29], Solar Cell 1: [Voltage: 2.81V, Current: 4.90mA], Solar Cell 2: [Voltage: 2.72V, Current: 5.55mA]
(Timestamp: 189800) Temperature Readings: [27.10, 25.16, 26.13, 24.84, 24.84, 20.97, 25.16, 21.61], Solar Cell 1: [Voltage: 3.10V, Current: 5.22mA], Solar Cell 2: [Voltage: 3.15V, Current: 6.53mA]
(Timestamp: 190303) Temperature Readings: [27.42, 25.16, 25.81, 24.84, 24.84, 20.97, 25.16, 21.61], Solar Cell 1: [Voltage: 3.03V, Current: 4.57mA], Solar Cell 2: [Voltage: 2.55V, Current: 5.55mA]
(Timestamp: 190805) Temperature Readings: [27.10, 25.16, 25.48, 24.84, 24.84, 20.97, 24.84, 20.97], Solar Cell 1: [Voltage: 2.68V, Current: 4.57mA], Solar Cell 2: [Voltage: 2.23V, Current: 4.90mA]
(Timestamp: 191308) Temperature Readings: [27.10, 25.16, 25.81, 24.84, 24.84, 21.29, 25.16, 21.61], Solar Cell 1: [Voltage: 3.10V, Current: 4.90mA], Solar Cell 2: [Voltage: 3.14V, Current: 6.53mA]
(Timestamp: 191811) Temperature Readings: [27.10, 25.16, 25.81, 24.84, 24.84, 20.97, 25.16, 21.29], Solar Cell 1: [Voltage: 3.02V, Current: 4.57mA], Solar Cell 2: [Voltage: 2.55V, Current: 5.55mA]
(Timestamp: 192314) Temperature Readings: [27.74, 25.16, 25.48, 24.84, 24.84, 20.97, 25.16, 20.97], Solar Cell 1: [Voltage: 2.68V, Current: 4.90mA], Solar Cell 2: [Voltage: 2.25V, Current: 4.90mA]
(Timestamp: 192817) Temperature Readings: [27.10, 25.16, 25.81, 24.84, 24.84, 20.97, 24.84, 21.61], Solar Cell 1: [Voltage: 3.09V, Current: 5.22mA], Solar Cell 2: [Voltage: 3.14V, Current: 6.20mA]
(Timestamp: 193319) Temperature Readings: [27.10, 25.16, 26.13, 24.84, 24.84, 20.97, 24.84, 20.97], Solar Cell 1: [Voltage: 3.00V, Current: 4.57mA], Solar Cell 2: [Voltage: 2.45V, Current: 5.22mA]
(Timestamp: 193822) Temperature Readings: [27.42, 25.16, 25.48, 24.84, 24.84, 20.97, 24.84, 20.65], Solar Cell 1: [Voltage: 2.72V, Current: 4.57mA], Solar Cell 2: [Voltage: 2.40V, Current: 5.55mA]
(Timestamp: 194325) Temperature Readings: [27.42, 25.16, 26.13, 24.84, 24.84, 20.97, 25.16, 21.61], Solar Cell 1: [Voltage: 3.09V, Current: 5.22mA], Solar Cell 2: [Voltage: 3.14V, Current: 6.20mA]
(Timestamp: 194828) Temperature Readings: [26.77, 25.16, 25.81, 24.84, 24.84, 20.65, 25.16, 21.61], Solar Cell 1: [Voltage: 2.99V, Current: 4.57mA], Solar Cell 2: [Voltage: 2.40V, Current: 5.22mA]
(Timestamp: 195334) Temperature Readings: [27.42, 25.16, 25.81, 24.84, 24.84, 20.97, 25.16, 21.61], Solar Cell 1: [Voltage: 3.11V, Current: 5.22mA], Solar Cell 2: [Voltage: 3.12V, Current: 6.20mA]
(Timestamp: 195837) Temperature Readings: [27.10, 25.16, 25.81, 24.84, 24.84, 21.61, 25.16, 23.23], Solar Cell 1: [Voltage: 2.75V, Current: 4.24mA], Solar Cell 2: [Voltage: 1.14V, Current: 102.85mA]
(Timestamp: 196340) Temperature Readings: [27.42, 25.16, 25.81, 25.16, 25.16, 20.97, 25.16, 21.61], Solar Cell 1: [Voltage: 2.93V, Current: 4.90mA], Solar Cell 2: [Voltage: 2.99V, Current: 6.20mA]
(Timestamp: 196842) Temperature Readings: [27.42, 25.16, 25.81, 24.84, 24.84, 20.97, 25.16, 21.61], Solar Cell 1: [Voltage: 3.11V, Current: 4.90mA], Solar Cell 2: [Voltage: 3.11V, Current: 6.20mA]
(Timestamp: 197345) Temperature Readings: [27.10, 25.16, 25.48, 24.84, 24.84, 21.29, 24.84, 22.90], Solar Cell 1: [Voltage: 2.71V, Current: 4.24mA], Solar Cell 2: [Voltage: 1.04V, Current: 92.73mA]
(Timestamp: 197848) Temperature Readings: [27.74, 25.16, 25.81, 24.84, 25.16, 20.97, 25.16, 21.61], Solar Cell 1: [Voltage: 2.95V, Current: 4.90mA], Solar Cell 2: [Voltage: 3.02V, Current: 6.20mA]
(Timestamp: 198351) Temperature Readings: [27.42, 25.48, 25.81, 25.16, 24.84, 20.97, 25.16, 21.61], Solar Cell 1: [Voltage: 3.10V, Current: 5.22mA], Solar Cell 2: [Voltage: 3.12V, Current: 6.20mA]
(Timestamp: 198853) Temperature Readings: [27.42, 25.16, 25.16, 24.84, 25.16, 20.65, 25.16, 20.32], Solar Cell 1: [Voltage: 2.84V, Current: 4.24mA], Solar Cell 2: [Voltage: 1.46V, Current: 7.18mA]
(Timestamp: 199356) Temperature Readings: [27.42, 25.16, 25.81, 24.84, 25.16, 20.97, 25.16, 21.61], Solar Cell 1: [Voltage: 2.86V, Current: 4.90mA], Solar Cell 2: [Voltage: 2.88V, Current: 5.88mA]
(Timestamp: 199858) Temperature Readings: [27.42, 25.16, 25.81, 24.84, 25.16, 20.97, 25.16, 21.61], Solar Cell 1: [Voltage: 3.10V, Current: 4.90mA], Solar Cell 2: [Voltage: 3.14V, Current: 6.20mA]
(Timestamp: 200361) Temperature Readings: [27.42, 25.16, 25.81, 24.84, 25.16, 20.97, 25.16, 20.97], Solar Cell 1: [Voltage: 2.95V, Current: 4.90mA], Solar Cell 2: [Voltage: 2.21V, Current: 4.90mA]
(Timestamp: 200867) Temperature Readings: [27.42, 25.16, 25.81, 24.84, 24.84, 20.97, 25.16, 21.61], Solar Cell 1: [Voltage: 3.10V, Current: 5.22mA], Solar Cell 2: [Voltage: 3.14V, Current: 6.20mA]
(Timestamp: 201370) Temperature Readings: [27.42, 25.16, 25.48, 24.84, 24.84, 20.65, 25.16, 21.29], Solar Cell 1: [Voltage: 2.79V, Current: 4.57mA], Solar Cell 2: [Voltage: 1.29V, Current: 115.58mA]
(Timestamp: 201873) Temperature Readings: [27.74, 25.16, 25.81, 24.84, 25.16, 20.97, 25.16, 21.61], Solar Cell 1: [Voltage: 2.90V, Current: 4.90mA], Solar Cell 2: [Voltage: 2.95V, Current: 5.88mA]
(Timestamp: 202375) Temperature Readings: [27.42, 25.48, 25.81, 24.84, 25.16, 20.97, 25.16, 21.61], Solar Cell 1: [Voltage: 3.10V, Current: 5.22mA], Solar Cell 2: [Voltage: 3.13V, Current: 6.20mA]
(Timestamp: 202878) Temperature Readings: [27.42, 25.16, 25.81, 24.84, 24.84, 21.29, 25.16, 23.23], Solar Cell 1: [Voltage: 2.77V, Current: 4.24mA], Solar Cell 2: [Voltage: 1.22V, Current: 110.36mA]
(Timestamp: 203381) Temperature Readings: [27.74, 25.48, 25.81, 24.84, 25.16, 20.97, 25.16, 21.61], Solar Cell 1: [Voltage: 2.90V, Current: 4.90mA], Solar Cell 2: [Voltage: 2.97V, Current: 5.88mA]
(Timestamp: 203884) Temperature Readings: [27.42, 25.48, 25.81, 24.84, 24.84, 20.97, 25.16, 21.61], Solar Cell 1: [Voltage: 3.10V, Current: 4.90mA], Solar Cell 2: [Voltage: 3.12V, Current: 6.20mA]
(Timestamp: 204386) Temperature Readings: [27.42, 25.48, 25.48, 24.84, 24.84, 21.29, 25.16, 23.23], Solar Cell 1: [Voltage: 2.75V, Current: 4.24mA], Solar Cell 2: [Voltage: 1.19V, Current: 108.07mA]
(Timestamp: 204889) Temperature Readings: [27.74, 25.16, 25.81, 24.84, 25.16, 21.29, 25.16, 21.61], Solar Cell 1: [Voltage: 2.91V, Current: 4.90mA], Solar Cell 2: [Voltage: 2.97V, Current: 5.88mA]
(Timestamp: 205392) Temperature Readings: [27.42, 25.48, 25.81, 24.84, 24.84, 21.29, 25.16, 21.61], Solar Cell 1: [Voltage: 3.09V, Current: 5.22mA], Solar Cell 2: [Voltage: 3.12V, Current: 6.53mA]
(Timestamp: 205895) Temperature Readings: [27.42, 25.48, 25.48, 25.16, 25.16, 21.94, 25.16, 22.90], Solar Cell 1: [Voltage: 2.71V, Current: 4.24mA], Solar Cell 2: [Voltage: 1.08V, Current: 96.32mA]
(Timestamp: 206397) Temperature Readings: [27.42, 25.16, 25.81, 24.84, 25.16, 20.97, 25.16, 21.61], Solar Cell 1: [Voltage: 2.92V, Current: 5.22mA], Solar Cell 2: [Voltage: 3.01V, Current: 5.88mA]
(Timestamp: 206904) Temperature Readings: [27.42, 25.16, 25.48, 24.84, 25.16, 21.29, 25.16, 23.23], Solar Cell 1: [Voltage: 2.52V, Current: 4.24mA], Solar Cell 2: [Voltage: 1.23V, Current: 114.93mA]
(Timestamp: 207407) Temperature Readings: [27.42, 25.48, 25.81, 24.84, 24.84, 20.97, 25.16, 21.61], Solar Cell 1: [Voltage: 3.03V, Current: 4.90mA], Solar Cell 2: [Voltage: 3.12V, Current: 6.20mA]
(Timestamp: 207909) Temperature Readings: [27.74, 25.48, 25.81, 24.84, 25.16, 20.97, 25.16, 21.61], Solar Cell 1: [Voltage: 3.05V, Current: 4.90mA], Solar Cell 2: [Voltage: 2.86V, Current: 6.20mA]
(Timestamp: 208412) Temperature Readings: [27.42, 25.48, 25.48, 24.84, 25.16, 21.61, 25.16, 22.90], Solar Cell 1: [Voltage: 2.51V, Current: 4.24mA], Solar Cell 2: [Voltage: 1.19V, Current: 112.32mA]
(Timestamp: 208915) Temperature Readings: [27.74, 25.16, 25.81, 25.16, 24.84, 20.97, 25.16, 21.61], Solar Cell 1: [Voltage: 2.99V, Current: 5.22mA], Solar Cell 2: [Voltage: 3.09V, Current: 6.20mA]
(Timestamp: 209417) Temperature Readings: [28.06, 25.48, 25.81, 24.84, 24.84, 20.97, 25.16, 21.61], Solar Cell 1: [Voltage: 3.08V, Current: 4.90mA], Solar Cell 2: [Voltage: 3.05V, Current: 6.20mA]
(Timestamp: 209920) Temperature Readings: [27.74, 25.48, 25.48, 24.84, 25.16, 20.97, 25.16, 22.26], Solar Cell 1: [Voltage: 2.55V, Current: 4.24mA], Solar Cell 2: [Voltage: 0.88V, Current: 76.40mA]
(Timestamp: 210422) Temperature Readings: [27.42, 25.48, 25.81, 25.16, 25.16, 20.97, 24.84, 21.61], Solar Cell 1: [Voltage: 2.92V, Current: 4.90mA], Solar Cell 2: [Voltage: 3.03V, Current: 6.20mA]
(Timestamp: 210925) Temperature Readings: [27.42, 25.16, 25.81, 24.84, 24.84, 20.97, 25.16, 21.61], Solar Cell 1: [Voltage: 3.06V, Current: 5.22mA], Solar Cell 2: [Voltage: 3.12V, Current: 6.20mA]
(Timestamp: 211428) Temperature Readings: [27.74, 25.16, 25.48, 25.16, 25.16, 21.61, 25.16, 22.90], Solar Cell 1: [Voltage: 2.70V, Current: 4.24mA], Solar Cell 2: [Voltage: 1.10V, Current: 98.93mA]
(Timestamp: 211930) Temperature Readings: [28.06, 25.48, 25.81, 25.16, 25.16, 20.97, 25.16, 21.61], Solar Cell 1: [Voltage: 2.89V, Current: 4.90mA], Solar Cell 2: [Voltage: 2.99V, Current: 5.88mA]
(Timestamp: 212433) Temperature Readings: [27.42, 25.81, 25.81, 25.16, 25.16, 20.97, 25.48, 21.61], Solar Cell 1: [Voltage: 3.08V, Current: 5.22mA], Solar Cell 2: [Voltage: 3.12V, Current: 6.20mA]
(Timestamp: 212940) Temperature Readings: [27.42, 25.48, 25.48, 25.16, 24.84, 20.97, 25.16, 21.61], Solar Cell 1: [Voltage: 3.00V, Current: 4.90mA], Solar Cell 2: [Voltage: 3.10V, Current: 6.20mA]
(Timestamp: 213442) Temperature Readings: [27.74, 25.48, 25.81, 25.16, 25.48, 20.97, 25.16, 21.61], Solar Cell 1: [Voltage: 3.05V, Current: 4.90mA], Solar Cell 2: [Voltage: 2.94V, Current: 5.88mA]
(Timestamp: 213945) Temperature Readings: [27.74, 25.48, 25.48, 25.16, 25.16, 21.29, 25.16, 22.90], Solar Cell 1: [Voltage: 2.49V, Current: 4.24mA], Solar Cell 2: [Voltage: 1.16V, Current: 109.38mA]
(Timestamp: 214448) Temperature Readings: [27.74, 25.48, 25.81, 25.16, 25.16, 20.97, 25.48, 21.61], Solar Cell 1: [Voltage: 3.01V, Current: 4.90mA], Solar Cell 2: [Voltage: 3.10V, Current: 6.20mA]
(Timestamp: 214951) Temperature Readings: [27.42, 25.48, 25.81, 25.16, 25.16, 20.97, 25.16, 21.61], Solar Cell 1: [Voltage: 3.05V, Current: 4.90mA], Solar Cell 2: [Voltage: 2.93V, Current: 5.88mA]
(Timestamp: 215453) Temperature Readings: [27.74, 25.48, 25.48, 25.16, 25.16, 21.29, 25.16, 22.90], Solar Cell 1: [Voltage: 2.50V, Current: 4.24mA], Solar Cell 2: [Voltage: 1.23V, Current: 115.58mA]
(Timestamp: 215956) Temperature Readings: [27.74, 25.81, 25.81, 24.84, 25.16, 20.97, 25.48, 21.61], Solar Cell 1: [Voltage: 3.01V, Current: 5.22mA], Solar Cell 2: [Voltage: 3.11V, Current: 6.20mA]
(Timestamp: 216459) Temperature Readings: [27.74, 25.48, 25.48, 25.16, 25.16, 20.97, 25.16, 21.61], Solar Cell 1: [Voltage: 3.05V, Current: 4.90mA], Solar Cell 2: [Voltage: 2.91V, Current: 5.88mA]
(Timestamp: 216962) Temperature Readings: [27.74, 25.48, 25.48, 25.16, 25.16, 21.29, 25.16, 23.23], Solar Cell 1: [Voltage: 2.50V, Current: 4.57mA], Solar Cell 2: [Voltage: 1.35V, Current: 27.43mA]
(Timestamp: 217465) Temperature Readings: [27.74, 25.48, 25.81, 25.16, 25.16, 20.97, 25.16, 21.94], Solar Cell 1: [Voltage: 3.02V, Current: 4.90mA], Solar Cell 2: [Voltage: 3.12V, Current: 6.20mA]
(Timestamp: 217967) Temperature Readings: [27.74, 25.48, 25.81, 25.16, 25.16, 20.97, 25.48, 21.61], Solar Cell 1: [Voltage: 3.03V, Current: 4.90mA], Solar Cell 2: [Voltage: 2.83V, Current: 5.88mA]
(Timestamp: 218470) Temperature Readings: [27.74, 25.48, 25.48, 25.16, 25.16, 20.65, 25.16, 20.65], Solar Cell 1: [Voltage: 2.54V, Current: 4.57mA], Solar Cell 2: [Voltage: 1.63V, Current: 4.24mA]
(Timestamp: 218976) Temperature Readings: [27.74, 25.48, 25.81, 25.16, 25.16, 25.81, 25.81, 20.65], Solar Cell 1: [Voltage: 2.94V, Current: 4.57mA], Solar Cell 2: [Voltage: 2.30V, Current: 4.90mA]
(Timestamp: 219479) Temperature Readings: [27.42, 25.81, 25.48, 25.16, 25.16, 20.65, 25.16, 20.97], Solar Cell 1: [Voltage: 2.67V, Current: 4.90mA], Solar Cell 2: [Voltage: 2.39V, Current: 5.22mA]
(Timestamp: 219982) Temperature Readings: [27.42, 25.48, 25.81, 24.84, 25.16, 21.29, 25.16, 21.61], Solar Cell 1: [Voltage: 3.06V, Current: 5.22mA], Solar Cell 2: [Voltage: 3.14V, Current: 6.53mA]
(Timestamp: 220484) Temperature Readings: [27.74, 25.81, 25.81, 25.16, 25.16, 20.65, 25.48, 21.29], Solar Cell 1: [Voltage: 2.97V, Current: 4.90mA], Solar Cell 2: [Voltage: 2.53V, Current: 5.22mA]
(Timestamp: 220987) Temperature Readings: [27.42, 25.48, 25.48, 25.16, 25.16, 20.65, 25.16, 20.32], Solar Cell 1: [Voltage: 2.59V, Current: 4.57mA], Solar Cell 2: [Voltage: 2.01V, Current: 4.57mA]
(Timestamp: 221489) Temperature Readings: [28.06, 25.81, 25.81, 25.16, 25.16, 20.97, 25.16, 21.61], Solar Cell 1: [Voltage: 3.03V, Current: 5.22mA], Solar Cell 2: [Voltage: 3.12V, Current: 6.20mA]
(Timestamp: 221992) Temperature Readings: [27.74, 25.48, 25.81, 25.16, 25.16, 20.97, 25.16, 21.29], Solar Cell 1: [Voltage: 3.00V, Current: 4.57mA], Solar Cell 2: [Voltage: 2.70V, Current: 5.55mA]
(Timestamp: 222495) Temperature Readings: [27.74, 25.48, 25.48, 25.16, 25.16, 20.65, 25.16, 20.65], Solar Cell 1: [Voltage: 2.60V, Current: 4.57mA], Solar Cell 2: [Voltage: 2.06V, Current: 4.90mA]
(Timestamp: 222997) Temperature Readings: [27.74, 25.81, 25.81, 25.16, 25.16, 20.97, 25.16, 21.61], Solar Cell 1: [Voltage: 3.03V, Current: 4.90mA], Solar Cell 2: [Voltage: 3.14V, Current: 6.20mA]
(Timestamp: 223500) Temperature Readings: [28.06, 25.81, 25.81, 25.16, 25.16, 20.65, 25.48, 20.97], Solar Cell 1: [Voltage: 2.93V, Current: 4.90mA], Solar Cell 2: [Voltage: 2.37V, Current: 5.22mA]
(Timestamp: 224003) Temperature Readings: [27.74, 25.81, 25.48, 24.84, 25.16, 20.65, 25.48, 20.97], Solar Cell 1: [Voltage: 2.68V, Current: 4.57mA], Solar Cell 2: [Voltage: 2.55V, Current: 5.55mA]
(Timestamp: 224509) Temperature Readings: [28.06, 25.81, 25.48, 25.16, 25.16, 21.29, 25.48, 22.90], Solar Cell 1: [Voltage: 2.66V, Current: 4.24mA], Solar Cell 2: [Voltage: 1.05V, Current: 94.36mA]
(Timestamp: 225012) Temperature Readings: [27.74, 25.81, 25.81, 25.16, 25.16, 20.97, 25.48, 21.61], Solar Cell 1: [Voltage: 2.91V, Current: 4.90mA], Solar Cell 2: [Voltage: 3.03V, Current: 6.20mA]
(Timestamp: 225515) Temperature Readings: [27.74, 25.81, 26.13, 24.84, 25.16, 21.29, 25.16, 21.61], Solar Cell 1: [Voltage: 3.06V, Current: 4.90mA], Solar Cell 2: [Voltage: 3.07V, Current: 6.20mA]
(Timestamp: 226018) Temperature Readings: [27.74, 25.81, 25.48, 25.16, 25.16, 20.97, 25.16, 22.26], Solar Cell 1: [Voltage: 2.52V, Current: 3.92mA], Solar Cell 2: [Voltage: 0.88V, Current: 76.40mA]
(Timestamp: 226520) Temperature Readings: [28.06, 25.81, 25.81, 25.16, 25.16, 20.97, 25.16, 21.61], Solar Cell 1: [Voltage: 2.94V, Current: 5.22mA], Solar Cell 2: [Voltage: 3.07V, Current: 6.20mA]
(Timestamp: 227023) Temperature Readings: [27.74, 25.81, 25.81, 25.16, 25.16, 20.97, 25.16, 21.61], Solar Cell 1: [Voltage: 3.03V, Current: 4.90mA], Solar Cell 2: [Voltage: 3.01V, Current: 5.88mA]
(Timestamp: 227526) Temperature Readings: [28.06, 25.48, 25.48, 25.16, 25.16, 20.97, 25.48, 22.90], Solar Cell 1: [Voltage: 1.57V, Current: 3.26mA], Solar Cell 2: [Voltage: 1.08V, Current: 100.56mA]
(Timestamp: 228029) Temperature Readings: [28.06, 25.81, 25.81, 25.16, 25.16, 20.97, 25.48, 21.29], Solar Cell 1: [Voltage: 3.03V, Current: 5.22mA], Solar Cell 2: [Voltage: 3.10V, Current: 6.20mA]
(Timestamp: 228532) Temperature Readings: [27.42, 25.81, 25.81, 25.16, 25.16, 20.97, 25.48, 21.29], Solar Cell 1: [Voltage: 3.05V, Current: 4.90mA], Solar Cell 2: [Voltage: 2.87V, Current: 5.88mA]
(Timestamp: 229034) Temperature Readings: [28.06, 25.81, 25.48, 25.16, 25.16, 20.65, 25.48, 20.32], Solar Cell 1: [Voltage: 2.54V, Current: 4.57mA], Solar Cell 2: [Voltage: 1.62V, Current: 4.24mA]
(Timestamp: 229537) Temperature Readings: [27.74, 25.48, 25.81, 25.16, 25.48, 20.97, 25.16, 21.61], Solar Cell 1: [Voltage: 3.04V, Current: 4.90mA], Solar Cell 2: [Voltage: 3.11V, Current: 6.20mA]
(Timestamp: 230039) Temperature Readings: [27.74, 25.81, 25.81, 25.16, 25.16, 20.97, 25.16, 21.29], Solar Cell 1: [Voltage: 3.06V, Current: 4.90mA], Solar Cell 2: [Voltage: 2.89V, Current: 5.88mA]
(Timestamp: 230546) Temperature Readings: [27.74, 25.81, 25.81, 25.16, 25.16, 20.97, 25.48, 20.97], Solar Cell 1: [Voltage: 3.09V, Current: 4.90mA], Solar Cell 2: [Voltage: 3.13V, Current: 6.20mA]
(Timestamp: 231049) Temperature Readings: [27.74, 25.81, 25.48, 25.16, 25.16, 20.65, 25.16, 20.32], Solar Cell 1: [Voltage: 2.87V, Current: 4.57mA], Solar Cell 2: [Voltage: 1.75V, Current: 4.24mA]
(Timestamp: 231551) Temperature Readings: [28.06, 25.81, 25.48, 25.16, 25.16, 20.65, 25.16, 21.29], Solar Cell 1: [Voltage: 2.79V, Current: 4.90mA], Solar Cell 2: [Voltage: 2.77V, Current: 5.88mA]
(Timestamp: 232054) Temperature Readings: [28.06, 25.81, 25.48, 25.16, 25.16, 20.97, 25.48, 21.61], Solar Cell 1: [Voltage: 3.08V, Current: 4.90mA], Solar Cell 2: [Voltage: 3.14V, Current: 6.20mA]
(Timestamp: 232557) Temperature Readings: [27.74, 25.81, 25.48, 25.16, 25.48, 20.65, 25.16, 20.65], Solar Cell 1: [Voltage: 2.86V, Current: 4.57mA], Solar Cell 2: [Voltage: 1.74V, Current: 4.24mA]
(Timestamp: 233059) Temperature Readings: [27.74, 25.81, 25.48, 25.16, 25.16, 20.65, 25.48, 20.97], Solar Cell 1: [Voltage: 2.84V, Current: 4.90mA], Solar Cell 2: [Voltage: 2.88V, Current: 5.88mA]
(Timestamp: 233562) Temperature Readings: [27.74, 26.13, 25.81, 25.16, 25.16, 20.97, 25.16, 21.61], Solar Cell 1: [Voltage: 3.09V, Current: 5.22mA], Solar Cell 2: [Voltage: 3.12V, Current: 6.20mA]
(Timestamp: 234065) Temperature Readings: [28.06, 25.81, 25.48, 25.16, 25.16, 21.29, 25.48, 23.23], Solar Cell 1: [Voltage: 2.72V, Current: 4.24mA], Solar Cell 2: [Voltage: 1.14V, Current: 102.85mA]
(Timestamp: 234568) Temperature Readings: [28.39, 25.81, 25.81, 25.16, 25.16, 20.97, 25.16, 21.61], Solar Cell 1: [Voltage: 2.92V, Current: 4.90mA], Solar Cell 2: [Voltage: 3.00V, Current: 6.20mA]
(Timestamp: 235070) Temperature Readings: [28.06, 25.81, 25.81, 25.16, 25.16, 20.97, 25.48, 21.61], Solar Cell 1: [Voltage: 3.08V, Current: 5.22mA], Solar Cell 2: [Voltage: 3.08V, Current: 6.20mA]
(Timestamp: 235573) Temperature Readings: [28.06, 25.81, 25.48, 25.16, 25.48, 20.97, 25.48, 21.61], Solar Cell 1: [Voltage: 2.55V, Current: 3.92mA], Solar Cell 2: [Voltage: 0.88V, Current: 75.75mA]
(Timestamp: 236076) Temperature Readings: [28.06, 25.81, 25.48, 25.16, 25.16, 20.97, 25.48, 21.61], Solar Cell 1: [Voltage: 2.98V, Current: 4.90mA], Solar Cell 2: [Voltage: 3.06V, Current: 6.20mA]
(Timestamp: 236582) Temperature Readings: [27.74, 26.13, 25.48, 25.16, 25.16, 20.65, 25.48, 20.65], Solar Cell 1: [Voltage: 2.65V, Current: 4.57mA], Solar Cell 2: [Voltage: 2.26V, Current: 5.22mA]
(Timestamp: 237085) Temperature Readings: [28.06, 25.81, 25.81, 25.16, 25.16, 20.97, 25.48, 21.61], Solar Cell 1: [Voltage: 3.06V, Current: 4.90mA], Solar Cell 2: [Voltage: 3.13V, Current: 6.20mA]
(Timestamp: 237588) Temperature Readings: [28.06, 26.13, 25.48, 25.16, 25.16, 20.65, 25.48, 20.32], Solar Cell 1: [Voltage: 2.90V, Current: 4.57mA], Solar Cell 2: [Voltage: 2.04V, Current: 4.57mA]
(Timestamp: 238091) Temperature Readings: [28.06, 25.81, 25.48, 25.48, 25.16, 20.97, 25.48, 20.97], Solar Cell 1: [Voltage: 2.77V, Current: 4.90mA], Solar Cell 2: [Voltage: 2.77V, Current: 5.88mA]
(Timestamp: 238594) Temperature Readings: [28.06, 26.13, 25.81, 25.16, 25.16, 20.97, 25.48, 21.61], Solar Cell 1: [Voltage: 3.08V, Current: 4.90mA], Solar Cell 2: [Voltage: 3.14V, Current: 6.20mA]
(Timestamp: 239096) Temperature Readings: [27.74, 25.81, 25.48, 25.16, 25.16, 20.65, 25.48, 20.32], Solar Cell 1: [Voltage: 2.79V, Current: 4.24mA], Solar Cell 2: [Voltage: 1.42V, Current: 16.65mA]
(Timestamp: 239599) Temperature Readings: [27.74, 25.81, 25.48, 25.16, 25.16, 20.97, 25.48, 20.97], Solar Cell 1: [Voltage: 2.82V, Current: 4.90mA], Solar Cell 2: [Voltage: 2.86V, Current: 5.88mA]
(Timestamp: 240101) Temperature Readings: [28.39, 25.81, 25.48, 25.16, 25.16, 20.97, 25.48, 21.61], Solar Cell 1: [Voltage: 3.08V, Current: 5.22mA], Solar Cell 2: [Voltage: 3.14V, Current: 5.88mA]
(Timestamp: 240604) Temperature Readings: [27.74, 26.13, 25.48, 25.16, 25.16, 20.65, 25.48, 20.65], Solar Cell 1: [Voltage: 2.86V, Current: 4.57mA], Solar Cell 2: [Voltage: 1.81V, Current: 4.57mA]
(Timestamp: 241107) Temperature Readings: [28.06, 25.81, 25.48, 25.16, 25.16, 20.97, 25.48, 20.97], Solar Cell 1: [Voltage: 2.80V, Current: 4.90mA], Solar Cell 2: [Voltage: 2.81V, Current: 5.88mA]
(Timestamp: 241609) Temperature Readings: [28.06, 25.81, 25.81, 25.16, 25.48, 20.97, 24.84, 21.61], Solar Cell 1: [Voltage: 3.08V, Current: 4.90mA], Solar Cell 2: [Voltage: 3.14V, Current: 6.53mA]
(Timestamp: 242115) Temperature Readings: [28.06, 26.13, 25.48, 25.48, 25.48, 20.97, 25.16, 21.29], Solar Cell 1: [Voltage: 2.92V, Current: 4.90mA], Solar Cell 2: [Voltage: 3.01V, Current: 6.20mA]
(Timestamp: 242618) Temperature Readings: [28.39, 26.13, 25.81, 25.48, 25.16, 20.97, 25.48, 21.61], Solar Cell 1: [Voltage: 3.07V, Current: 4.90mA], Solar Cell 2: [Voltage: 3.06V, Current: 6.20mA]
(Timestamp: 243121) Temperature Readings: [28.06, 25.81, 25.16, 25.16, 25.16, 20.97, 25.48, 21.61], Solar Cell 1: [Voltage: 2.48V, Current: 4.24mA], Solar Cell 2: [Voltage: 0.89V, Current: 78.03mA]
(Timestamp: 243624) Temperature Readings: [28.06, 26.13, 25.16, 25.16, 25.48, 20.97, 25.48, 21.29], Solar Cell 1: [Voltage: 2.99V, Current: 4.90mA], Solar Cell 2: [Voltage: 3.07V, Current: 6.53mA]
(Timestamp: 244126) Temperature Readings: [28.06, 26.13, 25.81, 25.16, 25.16, 20.65, 25.48, 21.29], Solar Cell 1: [Voltage: 3.05V, Current: 4.90mA], Solar Cell 2: [Voltage: 2.95V, Current: 5.88mA]
(Timestamp: 244629) Temperature Readings: [27.74, 26.13, 25.16, 25.16, 25.48, 20.97, 25.48, 22.90], Solar Cell 1: [Voltage: 2.48V, Current: 4.57mA], Solar Cell 2: [Voltage: 1.26V, Current: 115.58mA]
(Timestamp: 245132) Temperature Readings: [28.06, 26.13, 25.81, 25.16, 25.48, 20.97, 25.81, 21.61], Solar Cell 1: [Voltage: 3.02V, Current: 4.90mA], Solar Cell 2: [Voltage: 3.11V, Current: 6.20mA]
(Timestamp: 245635) Temperature Readings: [28.06, 25.81, 25.81, 25.48, 25.48, 20.97, 25.48, 20.97], Solar Cell 1: [Voltage: 3.02V, Current: 4.90mA], Solar Cell 2: [Voltage: 2.79V, Current: 5.88mA]
(Timestamp: 246138) Temperature Readings: [28.06, 26.13, 25.16, 25.16, 25.48, 20.65, 25.48, 20.65], Solar Cell 1: [Voltage: 2.56V, Current: 4.57mA], Solar Cell 2: [Voltage: 1.86V, Current: 4.57mA]
(Timestamp: 246640) Temperature Readings: [27.74, 25.81, 25.81, 25.48, 25.16, 20.97, 25.48, 21.61], Solar Cell 1: [Voltage: 3.05V, Current: 4.90mA], Solar Cell 2: [Voltage: 3.12V, Current: 6.53mA]
(Timestamp: 247143) Temperature Readings: [28.06, 26.13, 25.81, 25.16, 25.48, 20.65, 25.48, 20.97], Solar Cell 1: [Voltage: 2.97V, Current: 4.57mA], Solar Cell 2: [Voltage: 2.46V, Current: 5.22mA]
(Timestamp: 247646) Temperature Readings: [28.06, 25.81, 25.48, 25.16, 25.16, 20.97, 25.48, 20.97], Solar Cell 1: [Voltage: 2.67V, Current: 4.90mA], Solar Cell 2: [Voltage: 2.49V, Current: 5.55mA]
(Timestamp: 248152) Temperature Readings: [28.06, 26.13, 25.48, 25.48, 25.16, 20.97, 25.48, 22.90], Solar Cell 1: [Voltage: 2.68V, Current: 4.24mA], Solar Cell 2: [Voltage: 1.10V, Current: 98.28mA]
(Timestamp: 248655) Temperature Readings: [28.39, 26.13, 25.48, 25.16, 25.48, 20.97, 25.48, 21.29], Solar Cell 1: [Voltage: 2.92V, Current: 4.90mA], Solar Cell 2: [Voltage: 3.03V, Current: 6.20mA]
(Timestamp: 249158) Temperature Readings: [28.06, 25.81, 25.48, 25.48, 25.48, 20.97, 25.48, 21.61], Solar Cell 1: [Voltage: 3.06V, Current: 4.90mA], Solar Cell 2: [Voltage: 3.06V, Current: 6.20mA]
(Timestamp: 249661) Temperature Readings: [28.39, 26.13, 25.16, 25.48, 25.48, 20.65, 25.48, 21.61], Solar Cell 1: [Voltage: 2.46V, Current: 3.92mA], Solar Cell 2: [Voltage: 0.91V, Current: 80.65mA]
(Timestamp: 250163) Temperature Readings: [28.39, 26.13, 25.48, 25.48, 25.48, 20.65, 25.48, 21.29], Solar Cell 1: [Voltage: 2.95V, Current: 4.90mA], Solar Cell 2: [Voltage: 3.05V, Current: 6.20mA]
(Timestamp: 250666) Temperature Readings: [28.06, 25.48, 25.81, 25.48, 25.48, 20.97, 25.48, 21.61], Solar Cell 1: [Voltage: 3.06V, Current: 5.22mA], Solar Cell 2: [Voltage: 3.07V, Current: 6.20mA]
(Timestamp: 251168) Temperature Readings: [28.39, 26.13, 25.16, 25.16, 25.48, 20.97, 25.48, 21.61], Solar Cell 1: [Voltage: 2.52V, Current: 4.24mA], Solar Cell 2: [Voltage: 0.88V, Current: 76.07mA]
(Timestamp: 251671) Temperature Readings: [27.74, 26.13, 25.81, 25.16, 25.48, 20.65, 25.48, 21.29], Solar Cell 1: [Voltage: 2.93V, Current: 4.57mA], Solar Cell 2: [Voltage: 3.03V, Current: 6.20mA]
(Timestamp: 252173) Temperature Readings: [28.06, 26.13, 25.81, 25.16, 25.48, 20.65, 25.48, 21.61], Solar Cell 1: [Voltage: 3.07V, Current: 4.90mA], Solar Cell 2: [Voltage: 3.08V, Current: 6.20mA]
(Timestamp: 252676) Temperature Readings: [28.39, 26.13, 25.48, 24.84, 25.16, 20.97, 25.48, 22.90], Solar Cell 1: [Voltage: 2.65V, Current: 3.92mA], Solar Cell 2: [Voltage: 1.04V, Current: 92.73mA]
(Timestamp: 253179) Temperature Readings: [27.74, 26.13, 25.48, 25.48, 25.48, 20.65, 25.48, 21.29], Solar Cell 1: [Voltage: 2.91V, Current: 5.22mA], Solar Cell 2: [Voltage: 3.01V, Current: 6.20mA]
(Timestamp: 253682) Temperature Readings: [28.39, 25.81, 25.48, 25.48, 25.48, 20.65, 25.48, 21.29], Solar Cell 1: [Voltage: 3.06V, Current: 4.90mA], Solar Cell 2: [Voltage: 3.07V, Current: 6.20mA]
(Timestamp: 254188) Temperature Readings: [28.06, 26.13, 25.81, 25.48, 25.48, 20.65, 25.48, 21.29], Solar Cell 1: [Voltage: 3.02V, Current: 4.90mA], Solar Cell 2: [Voltage: 3.11V, Current: 6.20mA]
(Timestamp: 254691) Temperature Readings: [28.06, 26.13, 25.81, 25.48, 25.48, 20.65, 25.48, 21.61], Solar Cell 1: [Voltage: 2.99V, Current: 4.57mA], Solar Cell 2: [Voltage: 2.72V, Current: 5.88mA]
(Timestamp: 255193) Temperature Readings: [28.39, 26.13, 25.16, 25.48, 25.48, 20.32, 25.48, 20.32], Solar Cell 1: [Voltage: 2.57V, Current: 4.57mA], Solar Cell 2: [Voltage: 2.03V, Current: 4.57mA]
(Timestamp: 255696) Temperature Readings: [28.39, 26.45, 25.48, 25.16, 25.48, 20.97, 25.48, 21.61], Solar Cell 1: [Voltage: 3.04V, Current: 4.90mA], Solar Cell 2: [Voltage: 3.12V, Current: 6.20mA]
(Timestamp: 256199) Temperature Readings: [28.06, 26.13, 25.48, 25.48, 25.48, 20.65, 25.48, 20.97], Solar Cell 1: [Voltage: 2.93V, Current: 4.57mA], Solar Cell 2: [Voltage: 2.40V, Current: 5.22mA]
(Timestamp: 256702) Temperature Readings: [28.39, 26.13, 25.48, 25.81, 25.48, 20.97, 25.81, 20.97], Solar Cell 1: [Voltage: 2.66V, Current: 4.57mA], Solar Cell 2: [Voltage: 2.50V, Current: 5.22mA]
(Timestamp: 257205) Temperature Readings: [28.39, 26.13, 25.81, 25.48, 25.16, 20.65, 25.48, 21.29], Solar Cell 1: [Voltage: 3.04V, Current: 5.22mA], Solar Cell 2: [Voltage: 3.13V, Current: 6.53mA]
(Timestamp: 257707) Temperature Readings: [28.06, 26.13, 25.48, 25.16, 25.48, 20.65, 25.48, 20.65], Solar Cell 1: [Voltage: 2.86V, Current: 4.57mA], Solar Cell 2: [Voltage: 1.97V, Current: 4.57mA]
(Timestamp: 258210) Temperature Readings: [28.39, 26.45, 25.48, 25.16, 25.48, 20.65, 25.48, 20.97], Solar Cell 1: [Voltage: 2.75V, Current: 4.90mA], Solar Cell 2: [Voltage: 2.76V, Current: 5.88mA]
(Timestamp: 258713) Temperature Readings: [28.39, 26.13, 25.81, 25.48, 25.81, 20.65, 25.48, 21.29], Solar Cell 1: [Voltage: 3.05V, Current: 4.90mA], Solar Cell 2: [Voltage: 3.12V, Current: 6.20mA]
(Timestamp: 259216) Temperature Readings: [28.06, 26.45, 25.16, 25.48, 25.48, 20.65, 25.48, 20.65], Solar Cell 1: [Voltage: 2.78V, Current: 4.24mA], Solar Cell 2: [Voltage: 1.50V, Current: 5.55mA]
(Timestamp: 259718) Temperature Readings: [28.39, 26.13, 25.48, 25.16, 25.48, 20.65, 25.48, 21.29], Solar Cell 1: [Voltage: 2.83V, Current: 4.90mA], Solar Cell 2: [Voltage: 2.92V, Current: 5.88mA]
(Timestamp: 260225) Temperature Readings: [28.06, 26.13, 25.16, 25.48, 25.48, 20.65, 25.81, 22.26], Solar Cell 1: [Voltage: 2.43V, Current: 4.24mA], Solar Cell 2: [Voltage: 1.08V, Current: 100.56mA]
(Timestamp: 260727) Temperature Readings: [28.39, 26.45, 25.48, 25.48, 25.48, 20.32, 25.48, 21.29], Solar Cell 1: [Voltage: 2.96V, Current: 4.90mA], Solar Cell 2: [Voltage: 3.07V, Current: 6.20mA]
(Timestamp: 261230) Temperature Readings: [28.71, 26.45, 25.48, 25.48, 25.48, 20.65, 25.48, 21.61], Solar Cell 1: [Voltage: 3.05V, Current: 4.90mA], Solar Cell 2: [Voltage: 3.03V, Current: 6.20mA]
(Timestamp: 261733) Temperature Readings: [28.39, 26.13, 25.16, 25.48, 25.48, 20.97, 25.48, 21.29], Solar Cell 1: [Voltage: 2.45V, Current: 4.24mA], Solar Cell 2: [Voltage: 0.90V, Current: 79.01mA]
(Timestamp: 262235) Temperature Readings: [28.39, 26.45, 25.48, 25.48, 25.48, 20.65, 25.48, 21.61], Solar Cell 1: [Voltage: 2.94V, Current: 4.90mA], Solar Cell 2: [Voltage: 3.05V, Current: 6.20mA]
(Timestamp: 262738) Temperature Readings: [28.39, 26.13, 25.81, 25.48, 25.48, 20.65, 25.81, 21.61], Solar Cell 1: [Voltage: 3.05V, Current: 5.22mA], Solar Cell 2: [Voltage: 3.06V, Current: 6.20mA]
(Timestamp: 263240) Temperature Readings: [28.39, 26.13, 25.16, 25.48, 25.48, 20.97, 25.48, 22.26], Solar Cell 1: [Voltage: 2.58V, Current: 4.24mA], Solar Cell 2: [Voltage: 0.95V, Current: 83.26mA]
(Timestamp: 263743) Temperature Readings: [28.71, 26.45, 25.48, 25.48, 25.48, 20.65, 25.81, 21.29], Solar Cell 1: [Voltage: 2.92V, Current: 4.90mA], Solar Cell 2: [Voltage: 3.03V, Current: 6.20mA]
(Timestamp: 264246) Temperature Readings: [28.39, 26.45, 25.81, 25.48, 25.48, 20.65, 25.48, 21.61], Solar Cell 1: [Voltage: 3.05V, Current: 5.22mA], Solar Cell 2: [Voltage: 3.05V, Current: 6.20mA]
(Timestamp: 264749) Temperature Readings: [28.39, 26.13, 25.48, 25.48, 25.48, 20.97, 25.48, 21.29], Solar Cell 1: [Voltage: 2.45V, Current: 3.92mA], Solar Cell 2: [Voltage: 0.88V, Current: 77.71mA]
(Timestamp: 265251) Temperature Readings: [28.39, 26.45, 25.48, 25.48, 25.48, 20.65, 25.48, 21.29], Solar Cell 1: [Voltage: 2.95V, Current: 4.90mA], Solar Cell 2: [Voltage: 3.07V, Current: 5.88mA]
(Timestamp: 265758) Temperature Readings: [28.06, 26.13, 25.16, 25.48, 25.48, 20.65, 25.48, 20.32], Solar Cell 1: [Voltage: 2.58V, Current: 4.57mA], Solar Cell 2: [Voltage: 2.13V, Current: 5.22mA]
(Timestamp: 266261) Temperature Readings: [28.39, 26.13, 25.48, 25.48, 25.48, 20.65, 25.48, 21.61], Solar Cell 1: [Voltage: 3.03V, Current: 4.90mA], Solar Cell 2: [Voltage: 3.12V, Current: 6.20mA]
(Timestamp: 266763) Temperature Readings: [28.71, 26.13, 25.48, 25.48, 25.48, 20.65, 25.81, 20.97], Solar Cell 1: [Voltage: 2.90V, Current: 4.57mA], Solar Cell 2: [Voltage: 2.26V, Current: 4.90mA]
(Timestamp: 267266) Temperature Readings: [28.39, 26.45, 25.48, 25.48, 25.16, 20.65, 25.48, 20.97], Solar Cell 1: [Voltage: 2.70V, Current: 4.57mA], Solar Cell 2: [Voltage: 2.63V, Current: 5.55mA]
(Timestamp: 267769) Temperature Readings: [28.71, 26.13, 25.48, 25.48, 25.48, 20.65, 25.81, 21.61], Solar Cell 1: [Voltage: 3.05V, Current: 5.22mA], Solar Cell 2: [Voltage: 3.13V, Current: 6.20mA]
(Timestamp: 268272) Temperature Readings: [28.39, 26.45, 25.48, 25.48, 25.48, 20.65, 25.48, 20.32], Solar Cell 1: [Voltage: 2.83V, Current: 4.57mA], Solar Cell 2: [Voltage: 1.76V, Current: 4.57mA]
(Timestamp: 268774) Temperature Readings: [28.39, 26.45, 25.48, 25.48, 25.48, 20.65, 25.48, 20.97], Solar Cell 1: [Voltage: 2.77V, Current: 4.90mA], Solar Cell 2: [Voltage: 2.83V, Current: 5.88mA]
(Timestamp: 269277) Temperature Readings: [28.39, 26.45, 25.81, 25.48, 25.48, 20.65, 25.48, 21.61], Solar Cell 1: [Voltage: 3.05V, Current: 4.90mA], Solar Cell 2: [Voltage: 3.12V, Current: 6.20mA]
(Timestamp: 269780) Temperature Readings: [28.39, 26.45, 25.48, 25.48, 25.48, 20.65, 25.48, 20.32], Solar Cell 1: [Voltage: 2.75V, Current: 4.24mA], Solar Cell 2: [Voltage: 1.42V, Current: 16.98mA]
(Timestamp: 270283) Temperature Readings: [28.39, 26.45, 25.48, 25.48, 25.48, 20.65, 25.48, 20.97], Solar Cell 1: [Voltage: 2.82V, Current: 4.90mA], Solar Cell 2: [Voltage: 2.92V, Current: 5.88mA]
(Timestamp: 270785) Temperature Readings: [28.71, 26.45, 25.48, 25.48, 25.48, 20.65, 25.48, 21.61], Solar Cell 1: [Voltage: 3.05V, Current: 4.90mA], Solar Cell 2: [Voltage: 3.12V, Current: 6.20mA]
(Timestamp: 271288) Temperature Readings: [28.39, 26.45, 25.48, 25.48, 25.48, 20.65, 25.48, 20.32], Solar Cell 1: [Voltage: 2.84V, Current: 4.57mA], Solar Cell 2: [Voltage: 1.85V, Current: 4.57mA]
(Timestamp: 271794) Temperature Readings: [28.71, 26.45, 25.48, 25.48, 25.48, 20.97, 25.48, 21.29], Solar Cell 1: [Voltage: 3.06V, Current: 4.90mA], Solar Cell 2: [Voltage: 3.10V, Current: 6.20mA]
(Timestamp: 272297) Temperature Readings: [28.71, 26.45, 25.16, 25.48, 25.81, 20.97, 25.48, 22.90], Solar Cell 1: [Voltage: 2.62V, Current: 4.24mA], Solar Cell 2: [Voltage: 1.02V, Current: 90.77mA]
(Timestamp: 272799) Temperature Readings: [28.71, 26.45, 25.48, 25.48, 25.48, 20.65, 25.48, 20.97], Solar Cell 1: [Voltage: 2.86V, Current: 4.90mA], Solar Cell 2: [Voltage: 2.95V, Current: 5.88mA]
(Timestamp: 273302) Temperature Readings: [28.39, 26.45, 25.48, 25.48, 25.81, 20.97, 25.81, 21.61], Solar Cell 1: [Voltage: 3.05V, Current: 4.90mA], Solar Cell 2: [Voltage: 3.11V, Current: 6.20mA]
(Timestamp: 273805) Temperature Readings: [28.39, 26.45, 25.48, 25.48, 25.48, 20.97, 25.81, 23.23], Solar Cell 1: [Voltage: 2.70V, Current: 4.57mA], Solar Cell 2: [Voltage: 1.21V, Current: 109.05mA]
(Timestamp: 274307) Temperature Readings: [28.71, 26.45, 25.48, 25.48, 25.81, 20.65, 25.81, 21.29], Solar Cell 1: [Voltage: 2.86V, Current: 4.90mA], Solar Cell 2: [Voltage: 2.96V, Current: 5.88mA]
(Timestamp: 274810) Temperature Readings: [28.39, 26.77, 25.48, 25.48, 25.48, 20.97, 25.81, 21.29], Solar Cell 1: [Voltage: 3.05V, Current: 4.90mA], Solar Cell 2: [Voltage: 3.10V, Current: 6.20mA]
(Timestamp: 275313) Temperature Readings: [28.39, 26.45, 25.16, 25.48, 25.48, 20.97, 25.48, 22.26], Solar Cell 1: [Voltage: 2.61V, Current: 4.24mA], Solar Cell 2: [Voltage: 1.01V, Current: 89.46mA]
(Timestamp: 275816) Temperature Readings: [28.71, 26.77, 25.48, 25.48, 25.81, 20.65, 25.48, 21.29], Solar Cell 1: [Voltage: 2.89V, Current: 4.90mA], Solar Cell 2: [Voltage: 3.00V, Current: 6.20mA]
(Timestamp: 276319) Temperature Readings: [28.71, 26.45, 25.48, 25.48, 25.81, 20.65, 25.81, 21.61], Solar Cell 1: [Voltage: 3.05V, Current: 4.90mA], Solar Cell 2: [Voltage: 3.08V, Current: 6.20mA]
(Timestamp: 276821) Temperature Readings: [28.71, 26.77, 25.16, 25.48, 25.48, 20.97, 25.48, 21.94], Solar Cell 1: [Voltage: 2.55V, Current: 3.92mA], Solar Cell 2: [Voltage: 0.92V, Current: 79.67mA]
(Timestamp: 277324) Temperature Readings: [28.71, 26.45, 25.48, 25.48, 25.48, 20.65, 25.81, 21.29], Solar Cell 1: [Voltage: 2.91V, Current: 4.90mA], Solar Cell 2: [Voltage: 3.03V, Current: 6.20mA]
(Timestamp: 277830) Temperature Readings: [28.71, 26.45, 24.84, 25.48, 25.48, 20.32, 25.81, 20.32], Solar Cell 1: [Voltage: 2.46V, Current: 4.57mA], Solar Cell 2: [Voltage: 1.50V, Current: 4.24mA]
(Timestamp: 278333) Temperature Readings: [28.71, 26.45, 25.48, 25.48, 25.48, 20.65, 25.81, 21.29], Solar Cell 1: [Voltage: 3.01V, Current: 4.90mA], Solar Cell 2: [Voltage: 3.10V, Current: 6.20mA]
(Timestamp: 278836) Temperature Readings: [28.71, 26.45, 25.48, 25.48, 25.48, 20.65, 25.81, 20.97], Solar Cell 1: [Voltage: 2.99V, Current: 4.90mA], Solar Cell 2: [Voltage: 2.77V, Current: 5.88mA]
(Timestamp: 279422) Temperature Readings: [29.03, 26.45, 23.87, 25.48, 25.81, 20.97, 25.81, 21.29], Solar Cell 1: [Voltage: 2.45V, Current: 4.57mA], Solar Cell 2: [Voltage: 1.43V, Current: 6.53mA]
(Timestamp: 279925) Temperature Readings: [28.71, 26.77, 25.48, 25.48, 25.48, 20.97, 25.81, 21.29], Solar Cell 1: [Voltage: 3.00V, Current: 5.22mA], Solar Cell 2: [Voltage: 3.10V, Current: 6.20mA]
(Timestamp: 280428) Temperature Readings: [28.39, 26.45, 25.48, 25.48, 25.81, 20.65, 25.48, 20.97], Solar Cell 1: [Voltage: 2.93V, Current: 4.57mA], Solar Cell 2: [Voltage: 2.41V, Current: 5.22mA]
(Timestamp: 280931) Temperature Readings: [28.71, 26.45, 25.48, 25.48, 25.81, 20.65, 25.81, 20.65], Solar Cell 1: [Voltage: 2.62V, Current: 4.90mA], Solar Cell 2: [Voltage: 2.37V, Current: 5.22mA]
(Timestamp: 281433) Temperature Readings: [28.39, 26.45, 25.48, 25.48, 25.81, 20.97, 25.81, 21.61], Solar Cell 1: [Voltage: 3.02V, Current: 4.90mA], Solar Cell 2: [Voltage: 3.12V, Current: 6.20mA]
(Timestamp: 281936) Temperature Readings: [28.71, 26.45, 25.48, 25.48, 25.48, 20.65, 25.81, 20.97], Solar Cell 1: [Voltage: 2.98V, Current: 4.90mA], Solar Cell 2: [Voltage: 2.74V, Current: 5.55mA]
(Timestamp: 282439) Temperature Readings: [28.39, 26.45, 25.16, 25.48, 25.81, 20.32, 25.81, 20.32], Solar Cell 1: [Voltage: 2.49V, Current: 4.57mA], Solar Cell 2: [Voltage: 1.70V, Current: 4.24mA]
(Timestamp: 282941) Temperature Readings: [28.71, 26.77, 25.48, 25.81, 25.81, 20.65, 25.81, 21.61], Solar Cell 1: [Voltage: 2.99V, Current: 4.90mA], Solar Cell 2: [Voltage: 3.09V, Current: 6.20mA]
(Timestamp: 283447) Temperature Readings: [28.71, 26.77, 25.16, 25.81, 25.81, 20.65, 25.81, 20.32], Solar Cell 1: [Voltage: 2.61V, Current: 4.57mA], Solar Cell 2: [Voltage: 2.32V, Current: 5.22mA]
(Timestamp: 283950) Temperature Readings: [28.71, 26.45, 25.48, 25.81, 25.48, 20.65, 25.81, 21.61], Solar Cell 1: [Voltage: 3.01V, Current: 4.90mA], Solar Cell 2: [Voltage: 3.11V, Current: 6.20mA]
(Timestamp: 284453) Temperature Readings: [28.71, 26.45, 25.48, 25.16, 25.81, 20.65, 25.81, 20.97], Solar Cell 1: [Voltage: 2.94V, Current: 4.90mA], Solar Cell 2: [Voltage: 2.56V, Current: 5.55mA]
(Timestamp: 284955) Temperature Readings: [28.39, 26.45, 25.16, 25.48, 25.81, 26.13, 25.48, 21.29], Solar Cell 1: [Voltage: 2.57V, Current: 4.57mA], Solar Cell 2: [Voltage: 2.19V, Current: 5.22mA]
(Timestamp: 285458) Temperature Readings: [28.71, 26.77, 25.48, 25.48, 25.48, 20.65, 25.81, 21.61], Solar Cell 1: [Voltage: 3.02V, Current: 4.90mA], Solar Cell 2: [Voltage: 3.12V, Current: 6.20mA]
(Timestamp: 285961) Temperature Readings: [28.71, 26.77, 25.48, 25.48, 25.81, 20.65, 25.48, 20.97], Solar Cell 1: [Voltage: 2.92V, Current: 4.57mA], Solar Cell 2: [Voltage: 2.41V, Current: 5.22mA]
(Timestamp: 286464) Temperature Readings: [28.71, 26.77, 25.16, 25.48, 25.81, 20.65, 25.81, 20.32], Solar Cell 1: [Voltage: 2.62V, Current: 4.90mA], Solar Cell 2: [Voltage: 2.39V, Current: 5.22mA]
(Timestamp: 286967) Temperature Readings: [28.71, 26.45, 25.48, 25.48, 25.81, 20.65, 25.81, 21.61], Solar Cell 1: [Voltage: 3.03V, Current: 4.90mA], Solar Cell 2: [Voltage: 3.12V, Current: 6.20mA]
(Timestamp: 287469) Temperature Readings: [28.71, 26.77, 25.48, 25.48, 25.81, 20.65, 25.81, 20.97], Solar Cell 1: [Voltage: 2.90V, Current: 4.57mA], Solar Cell 2: [Voltage: 2.28V, Current: 5.22mA]
(Timestamp: 287972) Temperature Readings: [28.71, 26.77, 25.16, 25.48, 25.81, 20.65, 25.81, 20.65], Solar Cell 1: [Voltage: 2.65V, Current: 4.90mA], Solar Cell 2: [Voltage: 2.51V, Current: 5.22mA]
(Timestamp: 288475) Temperature Readings: [28.71, 26.77, 25.48, 25.48, 25.81, 20.65, 25.81, 21.61], Solar Cell 1: [Voltage: 3.03V, Current: 4.90mA], Solar Cell 2: [Voltage: 3.12V, Current: 6.20mA]
(Timestamp: 288978) Temperature Readings: [28.71, 26.77, 25.48, 25.48, 25.81, 20.65, 25.81, 20.65], Solar Cell 1: [Voltage: 2.88V, Current: 4.57mA], Solar Cell 2: [Voltage: 2.21V, Current: 4.90mA]
(Timestamp: 289484) Temperature Readings: [28.71, 26.77, 25.48, 25.81, 25.48, 20.65, 25.81, 21.29], Solar Cell 1: [Voltage: 3.05V, Current: 4.90mA], Solar Cell 2: [Voltage: 3.10V, Current: 6.20mA]
(Timestamp: 289987) Temperature Readings: [28.71, 26.77, 25.16, 25.81, 25.81, 20.97, 25.81, 22.58], Solar Cell 1: [Voltage: 2.61V, Current: 4.24mA], Solar Cell 2: [Voltage: 1.03V, Current: 91.75mA]
(Timestamp: 290490) Temperature Readings: [28.71, 26.45, 25.48, 25.48, 25.81, 20.65, 25.81, 21.29], Solar Cell 1: [Voltage: 2.87V, Current: 4.90mA], Solar Cell 2: [Voltage: 2.99V, Current: 6.20mA]
(Timestamp: 290993) Temperature Readings: [29.03, 26.77, 25.48, 25.81, 25.81, 20.65, 25.81, 21.29], Solar Cell 1: [Voltage: 3.04V, Current: 4.90mA], Solar Cell 2: [Voltage: 3.08V, Current: 6.20mA]
(Timestamp: 291495) Temperature Readings: [28.39, 26.77, 25.16, 25.81, 25.48, 20.97, 25.81, 21.94], Solar Cell 1: [Voltage: 2.54V, Current: 4.24mA], Solar Cell 2: [Voltage: 0.92V, Current: 79.01mA]
(Timestamp: 291998) Temperature Readings: [29.03, 26.77, 25.48, 25.81, 25.81, 20.65, 25.81, 20.97], Solar Cell 1: [Voltage: 2.86V, Current: 4.90mA], Solar Cell 2: [Voltage: 2.97V, Current: 6.20mA]
(Timestamp: 292500) Temperature Readings: [29.03, 26.77, 25.48, 25.81, 25.81, 20.65, 25.81, 21.29], Solar Cell 1: [Voltage: 3.05V, Current: 5.22mA], Solar Cell 2: [Voltage: 3.10V, Current: 6.20mA]
(Timestamp: 293003) Temperature Readings: [28.71, 26.45, 25.16, 25.81, 25.81, 20.65, 25.81, 20.32], Solar Cell 1: [Voltage: 2.74V, Current: 4.24mA], Solar Cell 2: [Voltage: 1.42V, Current: 16.65mA]
(Timestamp: 293506) Temperature Readings: [28.71, 26.45, 25.48, 25.81, 25.81, 20.65, 25.81, 20.97], Solar Cell 1: [Voltage: 2.74V, Current: 4.90mA], Solar Cell 2: [Voltage: 2.78V, Current: 5.55mA]
(Timestamp: 294008) Temperature Readings: [28.71, 26.77, 25.48, 25.48, 25.81, 20.65, 25.81, 21.29], Solar Cell 1: [Voltage: 3.03V, Current: 4.90mA], Solar Cell 2: [Voltage: 3.12V, Current: 6.20mA]
(Timestamp: 294511) Temperature Readings: [28.71, 26.77, 25.48, 25.81, 25.81, 20.65, 25.81, 20.97], Solar Cell 1: [Voltage: 2.91V, Current: 4.90mA], Solar Cell 2: [Voltage: 2.39V, Current: 5.22mA]
(Timestamp: 295013) Temperature Readings: [28.71, 26.77, 25.16, 25.81, 25.81, 20.65, 25.81, 20.65], Solar Cell 1: [Voltage: 2.61V, Current: 4.57mA], Solar Cell 2: [Voltage: 2.36V, Current: 5.22mA]
(Timestamp: 295520) Temperature Readings: [28.71, 26.77, 25.16, 25.81, 25.48, 21.29, 25.81, 23.23], Solar Cell 1: [Voltage: 2.68V, Current: 4.24mA], Solar Cell 2: [Voltage: 1.21V, Current: 108.72mA]
(Timestamp: 296023) Temperature Readings: [29.35, 26.77, 25.48, 25.48, 25.81, 20.65, 25.81, 21.29], Solar Cell 1: [Voltage: 2.84V, Current: 4.90mA], Solar Cell 2: [Voltage: 2.95V, Current: 5.88mA]
(Timestamp: 296526) Temperature Readings: [28.71, 26.77, 24.19, 25.81, 25.81, 20.65, 25.81, 21.61], Solar Cell 1: [Voltage: 3.05V, Current: 4.90mA], Solar Cell 2: [Voltage: 3.10V, Current: 6.20mA]
(Timestamp: 297028) Temperature Readings: [29.03, 27.10, 25.16, 25.81, 25.81, 20.97, 26.13, 22.90], Solar Cell 1: [Voltage: 2.66V, Current: 4.24mA], Solar Cell 2: [Voltage: 1.16V, Current: 105.13mA]
(Timestamp: 297531) Temperature Readings: [29.35, 27.10, 25.48, 25.48, 25.81, 20.65, 25.81, 21.61], Solar Cell 1: [Voltage: 2.85V, Current: 4.90mA], Solar Cell 2: [Voltage: 2.95V, Current: 5.88mA]
(Timestamp: 298034) Temperature Readings: [28.71, 26.77, 25.48, 25.81, 25.81, 20.65, 25.81, 21.61], Solar Cell 1: [Voltage: 3.04V, Current: 4.90mA], Solar Cell 2: [Voltage: 3.08V, Current: 6.20mA]
(Timestamp: 298537) Temperature Readings: [29.03, 26.77, 25.16, 25.81, 25.81, 20.97, 25.81, 22.58], Solar Cell 1: [Voltage: 2.63V, Current: 4.24mA], Solar Cell 2: [Voltage: 1.08V, Current: 96.97mA]
(Timestamp: 299039) Temperature Readings: [29.03, 27.10, 25.48, 25.81, 25.81, 20.65, 25.81, 20.97], Solar Cell 1: [Voltage: 2.85V, Current: 4.90mA], Solar Cell 2: [Voltage: 2.97V, Current: 5.88mA]
(Timestamp: 299542) Temperature Readings: [28.71, 26.77, 25.48, 25.48, 25.81, 20.65, 25.81, 21.61], Solar Cell 1: [Voltage: 3.04V, Current: 4.90mA], Solar Cell 2: [Voltage: 3.08V, Current: 6.20mA]
(Timestamp: 300045) Temperature Readings: [29.03, 27.10, 25.16, 25.81, 25.81, 20.97, 25.81, 22.58], Solar Cell 1: [Voltage: 2.61V, Current: 4.24mA], Solar Cell 2: [Voltage: 1.07V, Current: 95.01mA]
(Timestamp: 300548) Temperature Readings: [29.35, 26.77, 25.48, 25.81, 25.81, 20.65, 25.81, 21.29], Solar Cell 1: [Voltage: 2.86V, Current: 4.90mA], Solar Cell 2: [Voltage: 2.97V, Current: 5.88mA]
(Timestamp: 301051) Temperature Readings: [29.03, 26.77, 25.48, 25.81, 25.81, 20.65, 25.81, 21.61], Solar Cell 1: [Voltage: 3.04V, Current: 5.22mA], Solar Cell 2: [Voltage: 3.08V, Current: 6.20mA]
(Timestamp: 301557) Temperature Readings: [28.71, 27.10, 25.48, 25.81, 25.81, 20.65, 25.81, 21.29], Solar Cell 1: [Voltage: 2.96V, Current: 4.90mA], Solar Cell 2: [Voltage: 3.08V, Current: 6.20mA]
(Timestamp: 302060) Temperature Readings: [29.03, 27.10, 25.48, 25.81, 25.81, 20.65, 25.81, 21.29], Solar Cell 1: [Voltage: 3.03V, Current: 4.90mA], Solar Cell 2: [Voltage: 2.97V, Current: 5.88mA]
(Timestamp: 302562) Temperature Readings: [29.35, 26.77, 25.16, 25.81, 25.81, 20.65, 25.81, 21.61], Solar Cell 1: [Voltage: 2.43V, Current: 3.92mA], Solar Cell 2: [Voltage: 0.86V, Current: 73.79mA]
(Timestamp: 303065) Temperature Readings: [29.03, 26.77, 25.48, 25.81, 25.81, 20.65, 25.81, 21.29], Solar Cell 1: [Voltage: 2.89V, Current: 4.90mA], Solar Cell 2: [Voltage: 3.01V, Current: 5.88mA]
(Timestamp: 303567) Temperature Readings: [28.71, 26.77, 25.48, 25.81, 25.81, 20.65, 25.81, 21.29], Solar Cell 1: [Voltage: 3.03V, Current: 5.22mA], Solar Cell 2: [Voltage: 3.05V, Current: 6.20mA]
(Timestamp: 304070) Temperature Readings: [29.03, 27.10, 25.16, 25.81, 25.81, 20.97, 26.13, 22.58], Solar Cell 1: [Voltage: 2.59V, Current: 4.24mA], Solar Cell 2: [Voltage: 1.03V, Current: 92.40mA]
(Timestamp: 304572) Temperature Readings: [28.71, 26.77, 25.48, 25.81, 25.81, 20.65, 25.81, 20.97], Solar Cell 1: [Voltage: 2.81V, Current: 4.90mA], Solar Cell 2: [Voltage: 2.92V, Current: 5.88mA]
(Timestamp: 305075) Temperature Readings: [29.03, 27.10, 25.48, 25.81, 25.81, 20.65, 25.81, 21.29], Solar Cell 1: [Voltage: 3.03V, Current: 5.22mA], Solar Cell 2: [Voltage: 3.10V, Current: 6.20mA]
(Timestamp: 305578) Temperature Readings: [28.71, 27.10, 25.16, 25.81, 25.81, 20.97, 26.13, 22.90], Solar Cell 1: [Voltage: 2.66V, Current: 4.24mA], Solar Cell 2: [Voltage: 1.19V, Current: 106.77mA]
(Timestamp: 306081) Temperature Readings: [29.03, 27.10, 25.48, 25.81, 25.81, 20.65, 25.81, 20.97], Solar Cell 1: [Voltage: 2.83V, Current: 4.90mA], Solar Cell 2: [Voltage: 2.95V, Current: 5.88mA]
(Timestamp: 306584) Temperature Readings: [29.03, 27.10, 25.48, 25.81, 26.13, 20.65, 26.13, 21.29], Solar Cell 1: [Voltage: 3.03V, Current: 4.90mA], Solar Cell 2: [Voltage: 3.08V, Current: 6.53mA]
(Timestamp: 307090) Temperature Readings: [28.71, 26.77, 25.48, 25.81, 25.81, 20.65, 25.81, 21.29], Solar Cell 1: [Voltage: 2.95V, Current: 4.90mA], Solar Cell 2: [Voltage: 3.08V, Current: 6.20mA]
(Timestamp: 307593) Temperature Readings: [29.03, 27.42, 25.48, 25.81, 25.81, 20.65, 26.13, 20.97], Solar Cell 1: [Voltage: 2.99V, Current: 5.22mA], Solar Cell 2: [Voltage: 2.91V, Current: 5.88mA]
(Timestamp: 308096) Temperature Readings: [29.03, 27.42, 23.87, 25.81, 25.81, 20.97, 25.81, 22.90], Solar Cell 1: [Voltage: 2.39V, Current: 4.24mA], Solar Cell 2: [Voltage: 1.20V, Current: 112.64mA]
(Timestamp: 308598) Temperature Readings: [29.35, 27.10, 25.48, 25.81, 25.81, 20.65, 26.13, 21.29], Solar Cell 1: [Voltage: 2.96V, Current: 4.90mA], Solar Cell 2: [Voltage: 3.08V, Current: 6.20mA]
(Timestamp: 309101) Temperature Readings: [29.03, 27.10, 25.48, 25.81, 25.81, 20.65, 25.81, 20.97], Solar Cell 1: [Voltage: 2.98V, Current: 4.90mA], Solar Cell 2: [Voltage: 2.83V, Current: 5.88mA]
(Timestamp: 309604) Temperature Readings: [29.03, 27.10, 24.84, 25.81, 26.13, 20.65, 25.81, 20.32], Solar Cell 1: [Voltage: 2.43V, Current: 4.24mA], Solar Cell 2: [Voltage: 1.53V, Current: 4.24mA]
(Timestamp: 310107) Temperature Readings: [29.35, 26.77, 25.48, 25.81, 25.81, 20.65, 25.81, 21.29], Solar Cell 1: [Voltage: 2.97V, Current: 4.90mA], Solar Cell 2: [Voltage: 3.10V, Current: 6.53mA]
(Timestamp: 310609) Temperature Readings: [29.03, 27.10, 25.48, 25.81, 25.81, 20.65, 25.81, 20.97], Solar Cell 1: [Voltage: 2.97V, Current: 4.57mA], Solar Cell 2: [Voltage: 2.75V, Current: 5.88mA]
(Timestamp: 311112) Temperature Readings: [28.71, 27.10, 25.16, 25.81, 25.81, 20.65, 25.81, 20.32], Solar Cell 1: [Voltage: 2.46V, Current: 4.57mA], Solar Cell 2: [Voltage: 1.75V, Current: 4.24mA]
(Timestamp: 311615) Temperature Readings: [28.71, 27.10, 25.48, 25.81, 25.81, 20.65, 26.13, 21.61], Solar Cell 1: [Voltage: 2.98V, Current: 5.22mA], Solar Cell 2: [Voltage: 3.10V, Current: 6.20mA]
(Timestamp: 312118) Temperature Readings: [28.71, 27.10, 25.48, 26.13, 25.81, 20.65, 25.81, 20.97], Solar Cell 1: [Voltage: 2.94V, Current: 4.57mA], Solar Cell 2: [Voltage: 2.65V, Current: 5.55mA]
(Timestamp: 312620) Temperature Readings: [29.35, 27.10, 23.87, 25.81, 25.81, 20.32, 25.81, 20.32], Solar Cell 1: [Voltage: 2.44V, Current: 4.24mA], Solar Cell 2: [Voltage: 1.59V, Current: 4.24mA]
(Timestamp: 313127) Temperature Readings: [29.03, 27.42, 25.48, 25.81, 25.81, 20.65, 25.81, 20.65], Solar Cell 1: [Voltage: 2.86V, Current: 4.57mA], Solar Cell 2: [Voltage: 2.23V, Current: 5.22mA]
(Timestamp: 313629) Temperature Readings: [29.03, 26.77, 25.16, 25.81, 25.81, 20.65, 26.13, 20.65], Solar Cell 1: [Voltage: 2.64V, Current: 4.57mA], Solar Cell 2: [Voltage: 2.56V, Current: 5.55mA]
(Timestamp: 314132) Temperature Readings: [28.71, 27.10, 25.48, 25.81, 25.81, 20.65, 26.13, 21.29], Solar Cell 1: [Voltage: 2.99V, Current: 4.90mA], Solar Cell 2: [Voltage: 3.12V, Current: 6.20mA]
(Timestamp: 314634) Temperature Readings: [29.03, 27.10, 25.48, 25.81, 25.81, 20.65, 25.81, 20.97], Solar Cell 1: [Voltage: 2.90V, Current: 4.90mA], Solar Cell 2: [Voltage: 2.52V, Current: 5.22mA]
(Timestamp: 315137) Temperature Readings: [29.03, 27.10, 23.87, 25.81, 25.81, 20.32, 26.13, 20.32], Solar Cell 1: [Voltage: 2.48V, Current: 4.90mA], Solar Cell 2: [Voltage: 1.91V, Current: 4.24mA]
(Timestamp: 315640) Temperature Readings: [29.03, 27.10, 25.48, 25.81, 25.81, 20.65, 26.13, 21.29], Solar Cell 1: [Voltage: 2.98V, Current: 4.90mA], Solar Cell 2: [Voltage: 3.10V, Current: 6.20mA]
(Timestamp: 316143) Temperature Readings: [29.03, 27.10, 25.48, 25.81, 26.13, 20.65, 26.13, 20.97], Solar Cell 1: [Voltage: 2.90V, Current: 4.90mA], Solar Cell 2: [Voltage: 2.53V, Current: 5.22mA]
(Timestamp: 316645) Temperature Readings: [28.71, 27.10, 24.19, 25.81, 25.81, 20.65, 25.81, 20.32], Solar Cell 1: [Voltage: 2.54V, Current: 4.57mA], Solar Cell 2: [Voltage: 2.21V, Current: 4.90mA]
(Timestamp: 317148) Temperature Readings: [29.03, 27.10, 25.48, 25.81, 25.81, 20.65, 25.81, 21.29], Solar Cell 1: [Voltage: 2.99V, Current: 4.90mA], Solar Cell 2: [Voltage: 3.11V, Current: 6.20mA]
(Timestamp: 317651) Temperature Readings: [29.03, 27.10, 25.48, 25.81, 26.13, 20.65, 25.81, 20.97], Solar Cell 1: [Voltage: 2.88V, Current: 4.57mA], Solar Cell 2: [Voltage: 2.36V, Current: 5.22mA]
(Timestamp: 318154) Temperature Readings: [29.03, 27.10, 25.16, 25.81, 25.81, 20.32, 25.81, 20.65], Solar Cell 1: [Voltage: 2.60V, Current: 4.57mA], Solar Cell 2: [Voltage: 2.43V, Current: 5.22mA]
(Timestamp: 318657) Temperature Readings: [29.03, 27.10, 25.81, 25.81, 25.81, 20.97, 25.81, 21.29], Solar Cell 1: [Voltage: 2.99V, Current: 4.90mA], Solar Cell 2: [Voltage: 3.11V, Current: 6.20mA]
(Timestamp: 319163) Temperature Readings: [29.03, 27.10, 25.48, 26.13, 26.13, 20.65, 26.13, 21.61], Solar Cell 1: [Voltage: 2.82V, Current: 4.90mA], Solar Cell 2: [Voltage: 2.96V, Current: 5.88mA]
(Timestamp: 319666) Temperature Readings: [29.35, 27.10, 25.48, 25.81, 26.13, 20.65, 25.81, 21.29], Solar Cell 1: [Voltage: 3.01V, Current: 4.90mA], Solar Cell 2: [Voltage: 3.08V, Current: 6.20mA]
(Timestamp: 320169) Temperature Readings: [29.35, 27.10, 25.16, 25.81, 25.81, 20.97, 26.13, 22.26], Solar Cell 1: [Voltage: 2.52V, Current: 4.24mA], Solar Cell 2: [Voltage: 0.95V, Current: 83.26mA]
(Timestamp: 320671) Temperature Readings: [29.35, 27.10, 25.48, 26.13, 26.13, 20.65, 26.13, 20.97], Solar Cell 1: [Voltage: 2.86V, Current: 4.90mA], Solar Cell 2: [Voltage: 3.01V, Current: 5.88mA]
(Timestamp: 321174) Temperature Readings: [29.03, 27.10, 25.48, 25.81, 26.13, 20.65, 25.81, 21.29], Solar Cell 1: [Voltage: 3.00V, Current: 4.90mA], Solar Cell 2: [Voltage: 3.05V, Current: 6.20mA]
(Timestamp: 321677) Temperature Readings: [29.35, 26.77, 25.16, 25.81, 25.81, 20.65, 26.13, 21.61], Solar Cell 1: [Voltage: 2.45V, Current: 4.24mA], Solar Cell 2: [Voltage: 0.88V, Current: 74.77mA]
(Timestamp: 322180) Temperature Readings: [29.35, 27.10, 25.48, 25.81, 25.81, 20.65, 26.13, 21.29], Solar Cell 1: [Voltage: 2.87V, Current: 4.90mA], Solar Cell 2: [Voltage: 3.03V, Current: 6.20mA]
(Timestamp: 322682) Temperature Readings: [28.71, 27.10, 25.48, 26.13, 26.13, 20.65, 25.81, 21.29], Solar Cell 1: [Voltage: 3.00V, Current: 4.90mA], Solar Cell 2: [Voltage: 3.06V, Current: 6.20mA]
(Timestamp: 323185) Temperature Readings: [29.03, 27.42, 25.16, 25.81, 25.81, 20.97, 25.81, 22.90], Solar Cell 1: [Voltage: 2.60V, Current: 4.24mA], Solar Cell 2: [Voltage: 1.10V, Current: 98.93mA]
(Timestamp: 323687) Temperature Readings: [29.35, 27.42, 25.16, 25.81, 25.81, 20.65, 25.81, 21.29], Solar Cell 1: [Voltage: 2.77V, Current: 4.90mA], Solar Cell 2: [Voltage: 2.90V, Current: 6.20mA]
(Timestamp: 324190) Temperature Readings: [29.35, 27.10, 25.48, 25.81, 26.13, 20.65, 26.13, 21.61], Solar Cell 1: [Voltage: 3.01V, Current: 4.90mA], Solar Cell 2: [Voltage: 3.10V, Current: 6.20mA]
(Timestamp: 324696) Temperature Readings: [29.35, 27.10, 25.48, 25.81, 26.13, 20.65, 26.13, 21.29], Solar Cell 1: [Voltage: 2.88V, Current: 4.90mA], Solar Cell 2: [Voltage: 3.02V, Current: 6.20mA]
(Timestamp: 325199) Temperature Readings: [29.35, 27.10, 25.48, 25.48, 25.81, 20.65, 25.81, 21.61], Solar Cell 1: [Voltage: 3.01V, Current: 4.90mA], Solar Cell 2: [Voltage: 3.07V, Current: 6.20mA]
(Timestamp: 325701) Temperature Readings: [29.03, 27.42, 25.16, 25.81, 25.81, 20.97, 25.81, 22.90], Solar Cell 1: [Voltage: 2.61V, Current: 4.24mA], Solar Cell 2: [Voltage: 1.11V, Current: 99.58mA]
(Timestamp: 326204) Temperature Readings: [29.35, 27.10, 25.48, 26.13, 25.81, 20.65, 26.13, 20.97], Solar Cell 1: [Voltage: 2.83V, Current: 4.90mA], Solar Cell 2: [Voltage: 2.97V, Current: 5.88mA]
(Timestamp: 326707) Temperature Readings: [29.35, 27.10, 25.48, 25.81, 26.13, 20.65, 26.13, 21.94], Solar Cell 1: [Voltage: 3.01V, Current: 5.22mA], Solar Cell 2: [Voltage: 3.07V, Current: 6.20mA]
(Timestamp: 327210) Temperature Readings: [29.35, 27.10, 25.16, 25.81, 25.81, 20.65, 26.13, 22.26], Solar Cell 1: [Voltage: 2.54V, Current: 4.24mA], Solar Cell 2: [Voltage: 0.97V, Current: 85.22mA]
(Timestamp: 327713) Temperature Readings: [29.35, 27.10, 25.16, 25.81, 26.13, 20.65, 26.45, 20.97], Solar Cell 1: [Voltage: 2.86V, Current: 4.90mA], Solar Cell 2: [Voltage: 3.00V, Current: 5.88mA]
(Timestamp: 328215) Temperature Readings: [29.35, 27.42, 25.48, 25.81, 26.13, 20.97, 26.13, 21.61], Solar Cell 1: [Voltage: 3.01V, Current: 4.90mA], Solar Cell 2: [Voltage: 3.06V, Current: 6.20mA]
(Timestamp: 328718) Temperature Readings: [29.35, 27.42, 25.16, 25.81, 26.13, 20.65, 26.13, 21.94], Solar Cell 1: [Voltage: 2.50V, Current: 3.92mA], Solar Cell 2: [Voltage: 0.92V, Current: 79.01mA]
(Timestamp: 329221) Temperature Readings: [29.35, 27.42, 25.16, 26.13, 26.13, 20.65, 26.13, 21.29], Solar Cell 1: [Voltage: 2.86V, Current: 4.90mA], Solar Cell 2: [Voltage: 3.01V, Current: 5.88mA]
(Timestamp: 329724) Temperature Readings: [29.35, 27.10, 25.48, 26.13, 25.81, 20.65, 26.13, 21.29], Solar Cell 1: [Voltage: 3.01V, Current: 4.90mA], Solar Cell 2: [Voltage: 3.05V, Current: 6.20mA]
(Timestamp: 330227) Temperature Readings: [29.35, 27.10, 25.16, 25.81, 26.13, 20.65, 26.13, 21.61], Solar Cell 1: [Voltage: 2.48V, Current: 4.24mA], Solar Cell 2: [Voltage: 0.91V, Current: 78.03mA]
(Timestamp: 330733) Temperature Readings: [29.68, 27.10, 25.48, 25.81, 26.13, 20.65, 26.13, 20.97], Solar Cell 1: [Voltage: 2.97V, Current: 4.90mA], Solar Cell 2: [Voltage: 2.85V, Current: 5.88mA]
(Timestamp: 331236) Temperature Readings: [29.35, 27.42, 25.16, 25.81, 26.13, 20.65, 26.13, 20.65], Solar Cell 1: [Voltage: 2.39V, Current: 3.92mA], Solar Cell 2: [Voltage: 1.44V, Current: 5.55mA]
(Timestamp: 331739) Temperature Readings: [29.03, 27.42, 25.48, 25.81, 26.13, 20.65, 26.13, 21.29], Solar Cell 1: [Voltage: 2.95V, Current: 5.22mA], Solar Cell 2: [Voltage: 3.08V, Current: 6.20mA]
(Timestamp: 332241) Temperature Readings: [29.03, 27.42, 25.48, 25.81, 26.13, 20.65, 26.13, 20.97], Solar Cell 1: [Voltage: 2.94V, Current: 4.57mA], Solar Cell 2: [Voltage: 2.79V, Current: 5.88mA]
(Timestamp: 332744) Temperature Readings: [29.35, 27.42, 25.16, 25.81, 25.81, 20.65, 26.13, 19.68], Solar Cell 1: [Voltage: 2.39V, Current: 4.24mA], Solar Cell 2: [Voltage: 1.55V, Current: 4.24mA]
(Timestamp: 333247) Temperature Readings: [29.35, 27.42, 25.48, 25.81, 26.13, 20.65, 26.13, 21.61], Solar Cell 1: [Voltage: 2.92V, Current: 4.90mA], Solar Cell 2: [Voltage: 3.07V, Current: 6.20mA]
(Timestamp: 333749) Temperature Readings: [29.35, 27.10, 25.48, 26.13, 25.81, 20.65, 26.13, 20.97], Solar Cell 1: [Voltage: 2.97V, Current: 4.90mA], Solar Cell 2: [Voltage: 2.95V, Current: 5.88mA]
(Timestamp: 334252) Temperature Readings: [29.03, 27.42, 25.16, 25.81, 26.13, 20.65, 26.13, 21.94], Solar Cell 1: [Voltage: 1.48V, Current: 3.26mA], Solar Cell 2: [Voltage: 0.86V, Current: 74.44mA]
(Timestamp: 334755) Temperature Readings: [29.35, 27.42, 25.48, 25.81, 25.81, 20.65, 26.13, 21.61], Solar Cell 1: [Voltage: 1.92V, Current: 3.92mA], Solar Cell 2: [Voltage: 3.07V, Current: 6.20mA]
(Timestamp: 335258) Temperature Readings: [29.35, 27.42, 25.48, 25.81, 26.13, 20.65, 26.13, 20.97], Solar Cell 1: [Voltage: 1.94V, Current: 3.92mA], Solar Cell 2: [Voltage: 2.92V, Current: 5.88mA]
(Timestamp: 335760) Temperature Readings: [29.35, 27.42, 25.16, 26.13, 26.13, 20.65, 26.13, 21.61], Solar Cell 1: [Voltage: 1.49V, Current: 3.26mA], Solar Cell 2: [Voltage: 0.88V, Current: 76.40mA]
(Timestamp: 336267) Temperature Readings: [29.68, 27.42, 25.48, 26.13, 26.13, 20.65, 26.13, 20.97], Solar Cell 1: [Voltage: 1.88V, Current: 3.59mA], Solar Cell 2: [Voltage: 2.66V, Current: 5.55mA]
(Timestamp: 336770) Temperature Readings: [29.35, 27.42, 25.16, 25.81, 26.13, 20.65, 26.13, 20.65], Solar Cell 1: [Voltage: 1.55V, Current: 3.59mA], Solar Cell 2: [Voltage: 1.88V, Current: 4.57mA]
(Timestamp: 337272) Temperature Readings: [29.35, 27.42, 25.48, 26.13, 26.13, 20.65, 26.13, 21.61], Solar Cell 1: [Voltage: 1.95V, Current: 3.92mA], Solar Cell 2: [Voltage: 3.09V, Current: 6.20mA]
(Timestamp: 337775) Temperature Readings: [29.35, 27.42, 25.48, 25.81, 26.13, 20.65, 26.13, 20.97], Solar Cell 1: [Voltage: 1.90V, Current: 3.92mA], Solar Cell 2: [Voltage: 2.67V, Current: 5.55mA]
(Timestamp: 338278) Temperature Readings: [29.35, 27.42, 23.55, 25.81, 26.13, 20.00, 26.13, 19.68], Solar Cell 1: [Voltage: 1.58V, Current: 3.59mA], Solar Cell 2: [Voltage: 1.79V, Current: 4.57mA]
(Timestamp: 338781) Temperature Readings: [29.35, 27.42, 25.48, 25.81, 25.81, 20.65, 25.81, 21.61], Solar Cell 1: [Voltage: 1.94V, Current: 3.92mA], Solar Cell 2: [Voltage: 3.09V, Current: 5.88mA]
(Timestamp: 339284) Temperature Readings: [29.03, 27.42, 25.48, 26.13, 26.13, 20.32, 26.13, 20.97], Solar Cell 1: [Voltage: 2.81V, Current: 4.90mA], Solar Cell 2: [Voltage: 2.73V, Current: 5.55mA]
(Timestamp: 339786) Temperature Readings: [29.35, 27.42, 25.16, 25.81, 26.13, 20.00, 25.81, 20.00], Solar Cell 1: [Voltage: 2.28V, Current: 4.24mA], Solar Cell 2: [Voltage: 1.61V, Current: 4.24mA]
(Timestamp: 340289) Temperature Readings: [29.35, 27.42, 25.48, 25.81, 26.13, 20.65, 26.13, 21.29], Solar Cell 1: [Voltage: 2.80V, Current: 4.57mA], Solar Cell 2: [Voltage: 3.08V, Current: 6.20mA]
(Timestamp: 340792) Temperature Readings: [29.35, 27.42, 25.48, 26.13, 26.13, 20.32, 26.13, 21.29], Solar Cell 1: [Voltage: 1.94V, Current: 3.92mA], Solar Cell 2: [Voltage: 2.83V, Current: 5.88mA]
(Timestamp: 341295) Temperature Readings: [29.35, 27.42, 25.16, 25.81, 26.13, 20.97, 26.13, 22.90], Solar Cell 1: [Voltage: 1.50V, Current: 3.26mA], Solar Cell 2: [Voltage: 1.23V, Current: 114.93mA]
(Timestamp: 341797) Temperature Readings: [29.68, 27.42, 25.48, 26.13, 26.13, 20.65, 26.13, 20.97], Solar Cell 1: [Voltage: 1.94V, Current: 3.92mA], Solar Cell 2: [Voltage: 3.07V, Current: 6.20mA]
(Timestamp: 342304) Temperature Readings: [29.35, 27.42, 25.16, 25.81, 26.13, 20.65, 26.13, 20.32], Solar Cell 1: [Voltage: 1.63V, Current: 3.59mA], Solar Cell 2: [Voltage: 2.25V, Current: 4.90mA]
(Timestamp: 342807) Temperature Readings: [29.35, 27.42, 25.48, 26.13, 26.13, 20.32, 26.13, 21.61], Solar Cell 1: [Voltage: 1.95V, Current: 3.92mA], Solar Cell 2: [Voltage: 3.10V, Current: 6.20mA]
(Timestamp: 343310) Temperature Readings: [29.68, 27.42, 25.48, 25.81, 26.13, 20.65, 26.13, 20.97], Solar Cell 1: [Voltage: 1.88V, Current: 3.59mA], Solar Cell 2: [Voltage: 2.53V, Current: 5.22mA]
(Timestamp: 343812) Temperature Readings: [29.35, 27.74, 25.16, 26.13, 26.13, 20.00, 26.13, 20.32], Solar Cell 1: [Voltage: 1.53V, Current: 3.59mA], Solar Cell 2: [Voltage: 1.67V, Current: 4.24mA]
(Timestamp: 344315) Temperature Readings: [29.35, 27.42, 25.48, 26.13, 26.13, 20.65, 26.13, 21.29], Solar Cell 1: [Voltage: 1.94V, Current: 3.92mA], Solar Cell 2: [Voltage: 3.08V, Current: 6.20mA]
(Timestamp: 344817) Temperature Readings: [29.68, 27.74, 25.48, 26.13, 26.13, 20.32, 26.13, 20.97], Solar Cell 1: [Voltage: 1.94V, Current: 3.92mA], Solar Cell 2: [Voltage: 2.92V, Current: 5.88mA]
(Timestamp: 345320) Temperature Readings: [29.35, 27.42, 25.16, 26.13, 26.13, 20.65, 26.13, 21.61], Solar Cell 1: [Voltage: 1.52V, Current: 3.26mA], Solar Cell 2: [Voltage: 0.86V, Current: 74.12mA]
(Timestamp: 345823) Temperature Readings: [29.68, 27.42, 25.48, 26.13, 26.13, 20.65, 26.13, 20.97], Solar Cell 1: [Voltage: 1.84V, Current: 3.92mA], Solar Cell 2: [Voltage: 2.99V, Current: 6.20mA]
(Timestamp: 346325) Temperature Readings: [29.03, 27.42, 25.48, 26.13, 26.45, 20.65, 26.13, 21.29], Solar Cell 1: [Voltage: 1.99V, Current: 3.92mA], Solar Cell 2: [Voltage: 3.09V, Current: 6.20mA]
(Timestamp: 346828) Temperature Readings: [29.68, 27.42, 25.16, 26.13, 25.81, 20.32, 26.13, 20.32], Solar Cell 1: [Voltage: 1.66V, Current: 3.26mA], Solar Cell 2: [Voltage: 1.42V, Current: 15.35mA]
(Timestamp: 347331) Temperature Readings: [29.35, 27.42, 25.16, 26.13, 26.13, 20.97, 26.13, 20.97], Solar Cell 1: [Voltage: 1.69V, Current: 3.59mA], Solar Cell 2: [Voltage: 2.81V, Current: 5.88mA]
(Timestamp: 347833) Temperature Readings: [29.68, 27.42, 25.48, 26.13, 26.13, 20.65, 26.13, 21.29], Solar Cell 1: [Voltage: 1.92V, Current: 3.92mA], Solar Cell 2: [Voltage: 3.10V, Current: 6.53mA]
(Timestamp: 348340) Temperature Readings: [29.35, 27.42, 25.48, 26.13, 26.13, 20.65, 26.13, 20.97], Solar Cell 1: [Voltage: 1.80V, Current: 3.92mA], Solar Cell 2: [Voltage: 2.98V, Current: 5.88mA]
(Timestamp: 348843) Temperature Readings: [29.35, 27.42, 25.48, 26.13, 26.13, 20.65, 26.13, 21.29], Solar Cell 1: [Voltage: 1.94V, Current: 3.92mA], Solar Cell 2: [Voltage: 3.06V, Current: 6.20mA]
(Timestamp: 349345) Temperature Readings: [29.68, 27.42, 25.16, 26.13, 26.13, 20.65, 26.13, 22.90], Solar Cell 1: [Voltage: 1.61V, Current: 3.26mA], Solar Cell 2: [Voltage: 1.14V, Current: 102.52mA]
(Timestamp: 349848) Temperature Readings: [29.68, 27.42, 25.48, 26.13, 26.13, 20.65, 26.45, 20.97], Solar Cell 1: [Voltage: 1.74V, Current: 3.59mA], Solar Cell 2: [Voltage: 2.88V, Current: 5.88mA]
(Timestamp: 350351) Temperature Readings: [29.68, 27.42, 25.48, 26.13, 26.13, 20.65, 26.13, 21.29], Solar Cell 1: [Voltage: 1.93V, Current: 3.92mA], Solar Cell 2: [Voltage: 3.08V, Current: 6.20mA]
(Timestamp: 350854) Temperature Readings: [29.35, 27.74, 25.16, 26.13, 26.13, 20.32, 26.13, 20.65], Solar Cell 1: [Voltage: 1.71V, Current: 3.26mA], Solar Cell 2: [Voltage: 1.64V, Current: 4.24mA]
(Timestamp: 351357) Temperature Readings: [29.68, 27.42, 25.16, 26.13, 26.13, 20.65, 26.13, 20.97], Solar Cell 1: [Voltage: 1.66V, Current: 3.92mA], Solar Cell 2: [Voltage: 2.72V, Current: 5.88mA]
(Timestamp: 351859) Temperature Readings: [29.35, 27.74, 24.19, 26.13, 26.13, 20.32, 26.13, 21.29], Solar Cell 1: [Voltage: 1.91V, Current: 3.92mA], Solar Cell 2: [Voltage: 3.08V, Current: 6.20mA]
(Timestamp: 352362) Temperature Readings: [29.35, 27.74, 25.16, 26.13, 26.13, 20.65, 26.13, 20.32], Solar Cell 1: [Voltage: 1.75V, Current: 3.26mA], Solar Cell 2: [Voltage: 1.99V, Current: 4.24mA]
(Timestamp: 352865) Temperature Readings: [29.68, 27.42, 25.16, 26.13, 26.13, 20.65, 26.13, 20.97], Solar Cell 1: [Voltage: 1.62V, Current: 3.59mA], Solar Cell 2: [Voltage: 2.50V, Current: 5.55mA]
(Timestamp: 353368) Temperature Readings: [29.03, 27.42, 25.48, 26.13, 26.13, 20.65, 26.13, 21.61], Solar Cell 1: [Voltage: 1.92V, Current: 3.92mA], Solar Cell 2: [Voltage: 3.10V, Current: 6.53mA]
(Timestamp: 353870) Temperature Readings: [29.68, 27.74, 25.48, 26.13, 26.13, 20.65, 26.13, 20.97], Solar Cell 1: [Voltage: 1.86V, Current: 3.59mA], Solar Cell 2: [Voltage: 2.68V, Current: 5.55mA]
(Timestamp: 354376) Temperature Readings: [29.68, 27.74, 25.48, 26.13, 26.13, 20.65, 26.13, 21.29], Solar Cell 1: [Voltage: 1.91V, Current: 3.92mA], Solar Cell 2: [Voltage: 3.10V, Current: 6.20mA]
(Timestamp: 354879) Temperature Readings: [29.68, 27.74, 25.48, 26.13, 26.13, 20.65, 26.13, 20.97], Solar Cell 1: [Voltage: 1.85V, Current: 3.59mA], Solar Cell 2: [Voltage: 2.61V, Current: 5.55mA]
(Timestamp: 355382) Temperature Readings: [29.68, 27.74, 25.16, 26.13, 26.13, 20.32, 26.13, 20.32], Solar Cell 1: [Voltage: 1.48V, Current: 3.59mA], Solar Cell 2: [Voltage: 1.72V, Current: 4.24mA]
(Timestamp: 355884) Temperature Readings: [29.35, 27.42, 25.48, 26.13, 26.13, 20.65, 26.13, 21.29], Solar Cell 1: [Voltage: 1.88V, Current: 3.59mA], Solar Cell 2: [Voltage: 3.07V, Current: 6.20mA]
(Timestamp: 356387) Temperature Readings: [29.35, 27.42, 25.48, 25.81, 26.45, 20.65, 26.13, 20.97], Solar Cell 1: [Voltage: 1.92V, Current: 3.92mA], Solar Cell 2: [Voltage: 2.98V, Current: 5.88mA]
(Timestamp: 356889) Temperature Readings: [29.68, 27.42, 25.16, 26.13, 26.13, 20.65, 26.13, 21.94], Solar Cell 1: [Voltage: 1.54V, Current: 3.26mA], Solar Cell 2: [Voltage: 0.90V, Current: 78.03mA]
(Timestamp: 357392) Temperature Readings: [29.68, 27.74, 25.48, 26.13, 26.13, 20.32, 26.13, 20.97], Solar Cell 1: [Voltage: 1.81V, Current: 3.59mA], Solar Cell 2: [Voltage: 2.99V, Current: 5.88mA]
(Timestamp: 357895) Temperature Readings: [29.68, 27.74, 25.48, 26.13, 26.13, 20.65, 26.13, 20.97], Solar Cell 1: [Voltage: 1.94V, Current: 3.92mA], Solar Cell 2: [Voltage: 3.06V, Current: 6.20mA]
(Timestamp: 358398) Temperature Readings: [29.68, 27.42, 25.16, 25.81, 26.13, 20.97, 26.13, 22.58], Solar Cell 1: [Voltage: 1.59V, Current: 3.26mA], Solar Cell 2: [Voltage: 1.05V, Current: 93.38mA]
(Timestamp: 358901) Temperature Readings: [30.00, 27.74, 25.48, 26.13, 26.13, 20.65, 26.13, 20.97], Solar Cell 1: [Voltage: 1.76V, Current: 3.92mA], Solar Cell 2: [Voltage: 2.93V, Current: 5.88mA]
(Timestamp: 359403) Temperature Readings: [29.35, 27.74, 25.48, 26.13, 26.13, 20.32, 26.13, 21.61], Solar Cell 1: [Voltage: 1.94V, Current: 3.59mA], Solar Cell 2: [Voltage: 3.09V, Current: 6.20mA]
(Timestamp: 359910) Temperature Readings: [29.68, 27.74, 25.48, 26.13, 26.13, 20.65, 26.45, 21.61], Solar Cell 1: [Voltage: 1.85V, Current: 3.92mA], Solar Cell 2: [Voltage: 3.04V, Current: 6.20mA]
(Timestamp: 360413) Temperature Readings: [29.68, 27.74, 25.48, 26.45, 26.13, 20.65, 26.13, 20.97], Solar Cell 1: [Voltage: 1.92V, Current: 3.92mA], Solar Cell 2: [Voltage: 2.99V, Current: 5.88mA]
(Timestamp: 360915) Temperature Readings: [29.68, 27.74, 23.87, 26.13, 26.13, 20.65, 26.13, 21.61], Solar Cell 1: [Voltage: 1.50V, Current: 3.26mA], Solar Cell 2: [Voltage: 0.86V, Current: 73.46mA]
(Timestamp: 361418) Temperature Readings: [29.68, 27.74, 25.48, 26.13, 26.13, 20.65, 26.13, 20.97], Solar Cell 1: [Voltage: 1.75V, Current: 3.59mA], Solar Cell 2: [Voltage: 3.02V, Current: 6.20mA]
(Timestamp: 361921) Temperature Readings: [29.68, 27.74, 25.48, 26.13, 26.13, 20.65, 26.45, 21.61], Solar Cell 1: [Voltage: 1.86V, Current: 3.92mA], Solar Cell 2: [Voltage: 3.03V, Current: 6.20mA]
(Timestamp: 362424) Temperature Readings: [29.68, 27.74, 25.16, 26.13, 26.13, 20.65, 26.13, 21.61], Solar Cell 1: [Voltage: 1.43V, Current: 3.26mA], Solar Cell 2: [Voltage: 0.88V, Current: 75.75mA]
(Timestamp: 362927) Temperature Readings: [30.00, 27.74, 25.48, 26.13, 26.45, 20.65, 26.45, 20.97], Solar Cell 1: [Voltage: 1.74V, Current: 3.92mA], Solar Cell 2: [Voltage: 2.99V, Current: 6.20mA]
(Timestamp: 363429) Temperature Readings: [29.35, 27.74, 25.48, 26.13, 26.13, 20.65, 26.13, 21.29], Solar Cell 1: [Voltage: 1.86V, Current: 3.59mA], Solar Cell 2: [Voltage: 3.05V, Current: 6.20mA]
(Timestamp: 363932) Temperature Readings: [29.35, 27.74, 23.87, 26.13, 26.13, 20.65, 26.45, 22.26], Solar Cell 1: [Voltage: 1.47V, Current: 3.26mA], Solar Cell 2: [Voltage: 0.94V, Current: 81.62mA]
(Timestamp: 364435) Temperature Readings: [30.00, 27.74, 24.19, 26.13, 26.45, 20.32, 26.13, 20.97], Solar Cell 1: [Voltage: 1.71V, Current: 3.92mA], Solar Cell 2: [Voltage: 2.92V, Current: 5.88mA]
(Timestamp: 364937) Temperature Readings: [29.68, 27.74, 25.48, 26.13, 26.13, 20.65, 25.81, 21.29], Solar Cell 1: [Voltage: 1.88V, Current: 3.59mA], Solar Cell 2: [Voltage: 3.09V, Current: 6.20mA]
(Timestamp: 365440) Temperature Readings: [29.68, 27.74, 25.16, 26.13, 26.13, 20.32, 26.13, 20.32], Solar Cell 1: [Voltage: 1.69V, Current: 3.59mA], Solar Cell 2: [Voltage: 1.94V, Current: 4.57mA]
(Timestamp: 365947) Temperature Readings: [29.68, 27.74, 25.48, 26.45, 26.13, 20.65, 26.13, 20.97], Solar Cell 1: [Voltage: 1.86V, Current: 3.92mA], Solar Cell 2: [Voltage: 2.97V, Current: 5.88mA]
(Timestamp: 366449) Temperature Readings: [29.68, 27.74, 23.87, 26.13, 26.45, 20.65, 26.13, 21.61], Solar Cell 1: [Voltage: 1.46V, Current: 2.94mA], Solar Cell 2: [Voltage: 0.91V, Current: 77.71mA]
(Timestamp: 366952) Temperature Readings: [29.68, 27.74, 25.48, 26.13, 26.13, 20.65, 26.13, 20.97], Solar Cell 1: [Voltage: 1.72V, Current: 3.59mA], Solar Cell 2: [Voltage: 2.94V, Current: 5.88mA]
(Timestamp: 367455) Temperature Readings: [29.68, 27.74, 25.48, 26.13, 26.13, 20.65, 26.13, 20.97], Solar Cell 1: [Voltage: 1.86V, Current: 3.92mA], Solar Cell 2: [Voltage: 3.04V, Current: 6.20mA]
(Timestamp: 367957) Temperature Readings: [30.00, 27.74, 25.16, 26.13, 26.13, 20.65, 26.13, 22.58], Solar Cell 1: [Voltage: 1.51V, Current: 3.26mA], Solar Cell 2: [Voltage: 1.06V, Current: 95.34mA]
(Timestamp: 368460) Temperature Readings: [29.68, 28.06, 25.48, 26.45, 26.13, 20.65, 26.45, 20.97], Solar Cell 1: [Voltage: 1.70V, Current: 3.92mA], Solar Cell 2: [Voltage: 2.95V, Current: 5.88mA]
(Timestamp: 368963) Temperature Readings: [30.00, 27.74, 25.48, 26.13, 26.13, 20.32, 26.13, 20.97], Solar Cell 1: [Voltage: 1.85V, Current: 3.92mA], Solar Cell 2: [Voltage: 3.06V, Current: 6.20mA]
(Timestamp: 369466) Temperature Readings: [30.00, 27.74, 25.48, 26.13, 26.13, 20.65, 26.13, 22.26], Solar Cell 1: [Voltage: 1.48V, Current: 3.26mA], Solar Cell 2: [Voltage: 1.00V, Current: 88.48mA]
(Timestamp: 369969) Temperature Readings: [30.00, 27.74, 25.48, 26.13, 26.13, 20.65, 26.13, 20.97], Solar Cell 1: [Voltage: 1.72V, Current: 3.92mA], Solar Cell 2: [Voltage: 2.97V, Current: 5.88mA]
(Timestamp: 370472) Temperature Readings: [29.68, 27.74, 25.48, 26.45, 26.45, 20.65, 26.13, 21.29], Solar Cell 1: [Voltage: 1.85V, Current: 3.59mA], Solar Cell 2: [Voltage: 3.05V, Current: 6.20mA]
(Timestamp: 370974) Temperature Readings: [29.68, 27.74, 25.16, 26.13, 26.45, 20.65, 26.13, 22.26], Solar Cell 1: [Voltage: 1.46V, Current: 2.94mA], Solar Cell 2: [Voltage: 0.93V, Current: 79.67mA]
(Timestamp: 371477) Temperature Readings: [30.00, 27.74, 25.16, 26.13, 26.13, 20.65, 26.13, 20.97], Solar Cell 1: [Voltage: 1.73V, Current: 3.59mA], Solar Cell 2: [Voltage: 2.99V, Current: 5.88mA]
(Timestamp: 371983) Temperature Readings: [30.00, 28.06, 24.19, 26.13, 26.13, 20.65, 26.13, 20.65], Solar Cell 1: [Voltage: 1.39V, Current: 3.26mA], Solar Cell 2: [Voltage: 1.46V, Current: 4.90mA]
(Timestamp: 372486) Temperature Readings: [29.68, 27.74, 25.48, 26.13, 26.45, 20.65, 26.13, 21.29], Solar Cell 1: [Voltage: 1.83V, Current: 3.59mA], Solar Cell 2: [Voltage: 3.08V, Current: 6.20mA]
(Timestamp: 372989) Temperature Readings: [29.68, 28.06, 25.48, 26.13, 26.45, 20.65, 25.81, 20.97], Solar Cell 1: [Voltage: 1.78V, Current: 3.59mA], Solar Cell 2: [Voltage: 2.73V, Current: 5.88mA]
(Timestamp: 373492) Temperature Readings: [29.68, 27.74, 25.16, 26.45, 26.13, 20.00, 26.13, 20.32], Solar Cell 1: [Voltage: 1.42V, Current: 3.59mA], Solar Cell 2: [Voltage: 1.79V, Current: 4.57mA]
(Timestamp: 373995) Temperature Readings: [30.00, 27.74, 25.16, 26.13, 26.45, 20.32, 26.13, 20.97], Solar Cell 1: [Voltage: 1.81V, Current: 3.92mA], Solar Cell 2: [Voltage: 3.08V, Current: 6.20mA]
(Timestamp: 374497) Temperature Readings: [29.68, 28.06, 25.16, 26.13, 26.13, 20.65, 26.13, 20.97], Solar Cell 1: [Voltage: 1.74V, Current: 3.59mA], Solar Cell 2: [Voltage: 2.55V, Current: 5.55mA]
(Timestamp: 375000) Temperature Readings: [29.68, 27.74, 25.16, 26.13, 26.13, 20.00, 26.13, 20.32], Solar Cell 1: [Voltage: 1.41V, Current: 3.26mA], Solar Cell 2: [Voltage: 1.74V, Current: 4.24mA]
(Timestamp: 375503) Temperature Readings: [29.68, 28.06, 25.16, 26.13, 26.45, 20.32, 26.13, 21.29], Solar Cell 1: [Voltage: 1.81V, Current: 3.59mA], Solar Cell 2: [Voltage: 3.08V, Current: 6.20mA]
(Timestamp: 376005) Temperature Readings: [30.00, 28.06, 25.48, 26.13, 26.45, 20.65, 26.45, 20.97], Solar Cell 1: [Voltage: 1.78V, Current: 3.59mA], Solar Cell 2: [Voltage: 2.74V, Current: 5.88mA]
(Timestamp: 376508) Temperature Readings: [30.00, 28.06, 25.16, 26.13, 26.45, 20.65, 26.45, 20.97], Solar Cell 1: [Voltage: 1.37V, Current: 3.26mA], Solar Cell 2: [Voltage: 1.42V, Current: 6.86mA]
(Timestamp: 377010) Temperature Readings: [29.68, 27.74, 25.48, 26.13, 26.13, 20.65, 26.13, 20.97], Solar Cell 1: [Voltage: 1.80V, Current: 3.59mA], Solar Cell 2: [Voltage: 3.06V, Current: 6.20mA]
(Timestamp: 377517) Temperature Readings: [29.68, 28.06, 25.16, 26.45, 26.45, 20.65, 26.45, 20.32], Solar Cell 1: [Voltage: 1.47V, Current: 3.59mA], Solar Cell 2: [Voltage: 2.15V, Current: 4.90mA]
(Timestamp: 378019) Temperature Readings: [29.68, 27.74, 25.48, 26.45, 26.45, 20.32, 26.13, 21.61], Solar Cell 1: [Voltage: 1.84V, Current: 3.92mA], Solar Cell 2: [Voltage: 3.08V, Current: 6.20mA]
(Timestamp: 378522) Temperature Readings: [29.68, 27.74, 25.16, 26.13, 26.45, 20.65, 26.13, 20.32], Solar Cell 1: [Voltage: 1.70V, Current: 3.59mA], Solar Cell 2: [Voltage: 2.21V, Current: 4.90mA]
(Timestamp: 379025) Temperature Readings: [29.68, 28.06, 25.16, 26.13, 26.45, 20.65, 26.13, 20.65], Solar Cell 1: [Voltage: 1.55V, Current: 3.92mA], Solar Cell 2: [Voltage: 2.54V, Current: 5.55mA]
(Timestamp: 379528) Temperature Readings: [29.35, 28.06, 25.48, 26.13, 26.13, 20.32, 26.45, 20.97], Solar Cell 1: [Voltage: 1.84V, Current: 3.59mA], Solar Cell 2: [Voltage: 3.07V, Current: 6.20mA]
(Timestamp: 380031) Temperature Readings: [29.68, 28.06, 25.16, 26.13, 26.45, 20.00, 26.45, 20.65], Solar Cell 1: [Voltage: 1.65V, Current: 3.26mA], Solar Cell 2: [Voltage: 1.76V, Current: 4.24mA]
(Timestamp: 380533) Temperature Readings: [29.68, 28.06, 25.16, 26.13, 26.45, 20.65, 26.13, 21.29], Solar Cell 1: [Voltage: 1.62V, Current: 3.59mA], Solar Cell 2: [Voltage: 2.77V, Current: 5.88mA]
(Timestamp: 381036) Temperature Readings: [29.68, 28.06, 25.48, 26.45, 26.45, 20.65, 26.13, 21.29], Solar Cell 1: [Voltage: 1.85V, Current: 3.59mA], Solar Cell 2: [Voltage: 3.06V, Current: 6.53mA]
(Timestamp: 381539) Temperature Readings: [30.00, 28.06, 25.16, 26.13, 26.45, 19.68, 26.13, 20.65], Solar Cell 1: [Voltage: 1.57V, Current: 3.26mA], Solar Cell 2: [Voltage: 1.32V, Current: 110.68mA]
(Timestamp: 382042) Temperature Readings: [30.00, 28.06, 25.16, 26.13, 26.45, 20.65, 26.45, 20.97], Solar Cell 1: [Voltage: 1.67V, Current: 3.59mA], Solar Cell 2: [Voltage: 2.89V, Current: 5.88mA]
(Timestamp: 382545) Temperature Readings: [30.00, 28.06, 25.48, 26.45, 26.45, 20.65, 26.45, 21.29], Solar Cell 1: [Voltage: 1.85V, Current: 3.59mA], Solar Cell 2: [Voltage: 3.04V, Current: 6.20mA]
(Timestamp: 383047) Temperature Readings: [29.68, 28.06, 25.16, 26.45, 26.13, 20.97, 26.45, 22.26], Solar Cell 1: [Voltage: 1.50V, Current: 3.26mA], Solar Cell 2: [Voltage: 1.06V, Current: 95.01mA]
(Timestamp: 383554) Temperature Readings: [30.32, 28.06, 25.16, 26.45, 26.45, 20.65, 26.45, 21.29], Solar Cell 1: [Voltage: 1.81V, Current: 3.59mA], Solar Cell 2: [Voltage: 2.87V, Current: 5.88mA]
(Timestamp: 384057) Temperature Readings: [30.00, 28.06, 24.19, 26.45, 26.13, 20.97, 26.45, 22.90], Solar Cell 1: [Voltage: 1.37V, Current: 3.59mA], Solar Cell 2: [Voltage: 1.26V, Current: 115.58mA]
(Timestamp: 384559) Temperature Readings: [30.00, 28.06, 25.48, 26.45, 26.13, 20.00, 26.13, 20.97], Solar Cell 1: [Voltage: 1.79V, Current: 3.92mA], Solar Cell 2: [Voltage: 3.04V, Current: 6.20mA]
(Timestamp: 385062) Temperature Readings: [30.00, 28.06, 25.16, 26.45, 26.45, 20.65, 26.45, 20.97], Solar Cell 1: [Voltage: 1.81V, Current: 3.59mA], Solar Cell 2: [Voltage: 2.85V, Current: 6.20mA]
(Timestamp: 385564) Temperature Readings: [30.00, 28.06, 23.87, 26.45, 26.45, 20.65, 26.45, 21.61], Solar Cell 1: [Voltage: 1.35V, Current: 3.26mA], Solar Cell 2: [Voltage: 1.01V, Current: 93.38mA]
(Timestamp: 386067) Temperature Readings: [30.00, 28.06, 25.48, 26.13, 26.13, 20.65, 26.45, 20.97], Solar Cell 1: [Voltage: 1.77V, Current: 3.59mA], Solar Cell 2: [Voltage: 3.01V, Current: 6.20mA]
(Timestamp: 386570) Temperature Readings: [29.68, 28.06, 25.48, 26.45, 26.45, 20.65, 26.13, 21.61], Solar Cell 1: [Voltage: 2.95V, Current: 4.90mA], Solar Cell 2: [Voltage: 2.94V, Current: 5.88mA]
(Timestamp: 387072) Temperature Readings: [30.00, 27.74, 23.87, 26.45, 26.45, 20.65, 26.45, 21.61], Solar Cell 1: [Voltage: 2.34V, Current: 3.92mA], Solar Cell 2: [Voltage: 0.86V, Current: 73.46mA]
(Timestamp: 387575) Temperature Readings: [30.32, 28.06, 25.48, 26.45, 26.13, 20.65, 26.45, 21.61], Solar Cell 1: [Voltage: 2.83V, Current: 4.90mA], Solar Cell 2: [Voltage: 2.97V, Current: 5.88mA]
(Timestamp: 388077) Temperature Readings: [30.00, 28.06, 25.48, 26.45, 26.45, 20.65, 26.45, 20.97], Solar Cell 1: [Voltage: 2.96V, Current: 4.90mA], Solar Cell 2: [Voltage: 3.01V, Current: 6.20mA]
(Timestamp: 388580) Temperature Readings: [30.00, 28.06, 24.19, 26.45, 26.45, 20.65, 26.45, 21.61], Solar Cell 1: [Voltage: 1.44V, Current: 2.94mA], Solar Cell 2: [Voltage: 0.92V, Current: 79.01mA]
(Timestamp: 389083) Temperature Readings: [30.00, 28.06, 25.16, 26.45, 26.45, 20.65, 26.45, 20.97], Solar Cell 1: [Voltage: 1.72V, Current: 3.59mA], Solar Cell 2: [Voltage: 2.95V, Current: 5.88mA]
(Timestamp: 389589) Temperature Readings: [30.00, 28.06, 25.16, 26.45, 26.45, 20.65, 26.45, 20.00], Solar Cell 1: [Voltage: 1.39V, Current: 3.26mA], Solar Cell 2: [Voltage: 1.50V, Current: 4.24mA]
(Timestamp: 390092) Temperature Readings: [30.00, 28.06, 25.48, 26.45, 26.45, 20.32, 26.45, 20.97], Solar Cell 1: [Voltage: 1.81V, Current: 3.59mA], Solar Cell 2: [Voltage: 3.03V, Current: 6.20mA]
(Timestamp: 390595) Temperature Readings: [30.00, 28.06, 25.48, 26.45, 26.45, 20.65, 26.45, 20.97], Solar Cell 1: [Voltage: 1.79V, Current: 3.59mA], Solar Cell 2: [Voltage: 2.70V, Current: 5.55mA]
(Timestamp: 391098) Temperature Readings: [30.00, 28.06, 25.16, 26.45, 26.45, 20.32, 26.45, 20.32], Solar Cell 1: [Voltage: 1.41V, Current: 3.26mA], Solar Cell 2: [Voltage: 1.65V, Current: 4.24mA]
(Timestamp: 391601) Temperature Readings: [30.00, 28.06, 25.48, 26.45, 26.45, 20.65, 26.45, 20.97], Solar Cell 1: [Voltage: 1.82V, Current: 3.59mA], Solar Cell 2: [Voltage: 3.03V, Current: 6.20mA]
(Timestamp: 392103) Temperature Readings: [30.00, 28.39, 24.19, 26.45, 26.45, 20.65, 26.45, 20.97], Solar Cell 1: [Voltage: 1.77V, Current: 3.59mA], Solar Cell 2: [Voltage: 2.61V, Current: 5.55mA]
(Timestamp: 392606) Temperature Readings: [30.00, 28.06, 23.87, 26.45, 26.45, 20.00, 26.45, 20.32], Solar Cell 1: [Voltage: 1.45V, Current: 3.26mA], Solar Cell 2: [Voltage: 1.90V, Current: 4.57mA]
(Timestamp: 393109) Temperature Readings: [30.00, 28.06, 25.48, 26.45, 26.77, 20.65, 26.45, 20.97], Solar Cell 1: [Voltage: 1.82V, Current: 3.59mA], Solar Cell 2: [Voltage: 2.79V, Current: 5.88mA]
(Timestamp: 393612) Temperature Readings: [30.00, 28.06, 25.16, 26.45, 26.13, 20.65, 26.45, 20.97], Solar Cell 1: [Voltage: 1.74V, Current: 3.59mA], Solar Cell 2: [Voltage: 2.45V, Current: 5.22mA]
(Timestamp: 394115) Temperature Readings: [30.00, 28.06, 24.84, 26.45, 26.45, 20.32, 26.45, 20.32], Solar Cell 1: [Voltage: 1.48V, Current: 3.59mA], Solar Cell 2: [Voltage: 2.14V, Current: 4.90mA]
(Timestamp: 394617) Temperature Readings: [30.00, 28.06, 25.16, 26.45, 26.45, 20.65, 26.45, 20.97], Solar Cell 1: [Voltage: 1.84V, Current: 3.59mA], Solar Cell 2: [Voltage: 2.96V, Current: 5.88mA]
(Timestamp: 395120) Temperature Readings: [30.00, 28.06, 25.16, 26.13, 26.45, 20.65, 26.45, 20.65], Solar Cell 1: [Voltage: 1.74V, Current: 3.59mA], Solar Cell 2: [Voltage: 2.30V, Current: 4.90mA]
(Timestamp: 395626) Temperature Readings: [30.00, 28.06, 24.19, 26.45, 26.45, 20.65, 26.45, 20.97], Solar Cell 1: [Voltage: 1.86V, Current: 3.59mA], Solar Cell 2: [Voltage: 2.96V, Current: 5.88mA]
(Timestamp: 396129) Temperature Readings: [30.00, 28.06, 25.16, 26.45, 26.45, 20.32, 26.45, 20.65], Solar Cell 1: [Voltage: 1.65V, Current: 3.59mA], Solar Cell 2: [Voltage: 1.72V, Current: 4.24mA]
(Timestamp: 396631) Temperature Readings: [30.00, 28.39, 25.16, 26.45, 26.13, 20.00, 26.45, 20.97], Solar Cell 1: [Voltage: 1.56V, Current: 3.59mA], Solar Cell 2: [Voltage: 2.52V, Current: 5.55mA]
(Timestamp: 397134) Temperature Readings: [30.00, 28.06, 25.48, 26.45, 26.45, 20.32, 26.45, 21.29], Solar Cell 1: [Voltage: 1.86V, Current: 3.92mA], Solar Cell 2: [Voltage: 2.95V, Current: 5.88mA]
(Timestamp: 397637) Temperature Readings: [30.00, 28.06, 25.16, 26.77, 26.45, 20.65, 26.45, 20.97], Solar Cell 1: [Voltage: 1.72V, Current: 3.59mA], Solar Cell 2: [Voltage: 2.21V, Current: 4.90mA]
(Timestamp: 398139) Temperature Readings: [30.00, 28.06, 25.16, 26.45, 26.45, 20.65, 26.45, 20.65], Solar Cell 1: [Voltage: 1.49V, Current: 3.26mA], Solar Cell 2: [Voltage: 2.19V, Current: 4.90mA]
(Timestamp: 398642) Temperature Readings: [30.00, 28.39, 25.48, 26.45, 26.45, 20.65, 26.45, 20.97], Solar Cell 1: [Voltage: 1.85V, Current: 3.92mA], Solar Cell 2: [Voltage: 2.97V, Current: 5.88mA]
(Timestamp: 399145) Temperature Readings: [30.00, 28.39, 25.16, 26.13, 26.45, 20.32, 26.45, 20.65], Solar Cell 1: [Voltage: 1.72V, Current: 3.59mA], Solar Cell 2: [Voltage: 2.19V, Current: 5.22mA]
(Timestamp: 399648) Temperature Readings: [30.00, 28.06, 25.16, 26.45, 26.45, 20.32, 26.45, 20.65], Solar Cell 1: [Voltage: 1.55V, Current: 3.59mA], Solar Cell 2: [Voltage: 2.49V, Current: 5.22mA]
(Timestamp: 400151) Temperature Readings: [30.32, 28.06, 25.48, 26.45, 26.45, 20.65, 26.45, 21.29], Solar Cell 1: [Voltage: 1.86V, Current: 3.92mA], Solar Cell 2: [Voltage: 2.97V, Current: 5.88mA]
(Timestamp: 400653) Temperature Readings: [30.00, 28.06, 25.16, 26.45, 26.45, 20.65, 26.45, 20.65], Solar Cell 1: [Voltage: 1.66V, Current: 3.59mA], Solar Cell 2: [Voltage: 1.77V, Current: 4.24mA]
(Timestamp: 401160) Temperature Readings: [30.00, 28.06, 25.48, 26.45, 26.45, 20.65, 26.45, 20.97], Solar Cell 1: [Voltage: 1.85V, Current: 3.59mA], Solar Cell 2: [Voltage: 2.90V, Current: 5.88mA]
(Timestamp: 401663) Temperature Readings: [30.00, 28.39, 23.87, 26.45, 26.45, 20.65, 26.45, 21.29], Solar Cell 1: [Voltage: 1.39V, Current: 2.94mA], Solar Cell 2: [Voltage: 0.85V, Current: 71.83mA]
(Timestamp: 402165) Temperature Readings: [30.32, 28.06, 25.16, 26.13, 26.45, 20.32, 26.45, 20.97], Solar Cell 1: [Voltage: 1.77V, Current: 3.92mA], Solar Cell 2: [Voltage: 2.89V, Current: 5.88mA]
(Timestamp: 402668) Temperature Readings: [30.00, 28.71, 25.16, 26.45, 26.45, 20.65, 26.45, 20.97], Solar Cell 1: [Voltage: 1.85V, Current: 3.59mA], Solar Cell 2: [Voltage: 2.59V, Current: 5.55mA]
(Timestamp: 403171) Temperature Readings: [30.00, 28.39, 23.87, 26.45, 26.45, 20.32, 26.45, 21.94], Solar Cell 1: [Voltage: 1.37V, Current: 2.94mA], Solar Cell 2: [Voltage: 0.99V, Current: 90.77mA]
(Timestamp: 403674) Temperature Readings: [30.32, 28.39, 25.16, 26.45, 26.45, 20.65, 26.45, 20.97], Solar Cell 1: [Voltage: 1.81V, Current: 3.59mA], Solar Cell 2: [Voltage: 2.95V, Current: 5.88mA]
(Timestamp: 404177) Temperature Readings: [30.00, 28.39, 25.16, 26.45, 26.45, 20.65, 26.45, 20.97], Solar Cell 1: [Voltage: 1.83V, Current: 3.59mA], Solar Cell 2: [Voltage: 2.72V, Current: 5.55mA]
(Timestamp: 404679) Temperature Readings: [30.00, 28.39, 23.87, 26.45, 26.45, 20.97, 26.45, 21.29], Solar Cell 1: [Voltage: 1.39V, Current: 3.26mA], Solar Cell 2: [Voltage: 1.41V, Current: 7.84mA]
(Timestamp: 405182) Temperature Readings: [30.00, 28.39, 25.48, 26.13, 26.45, 20.65, 26.45, 20.97], Solar Cell 1: [Voltage: 1.81V, Current: 3.59mA], Solar Cell 2: [Voltage: 3.03V, Current: 6.20mA]
(Timestamp: 405685) Temperature Readings: [30.00, 28.39, 25.16, 26.45, 26.45, 20.65, 26.45, 20.97], Solar Cell 1: [Voltage: 1.77V, Current: 3.59mA], Solar Cell 2: [Voltage: 2.61V, Current: 5.55mA]
(Timestamp: 406188) Temperature Readings: [30.32, 28.39, 23.87, 26.45, 26.45, 20.00, 26.45, 20.00], Solar Cell 1: [Voltage: 1.43V, Current: 3.26mA], Solar Cell 2: [Voltage: 1.66V, Current: 4.24mA]
(Timestamp: 406690) Temperature Readings: [30.00, 28.39, 25.48, 26.45, 26.45, 20.65, 26.45, 20.97], Solar Cell 1: [Voltage: 1.84V, Current: 3.92mA], Solar Cell 2: [Voltage: 3.03V, Current: 6.20mA]
(Timestamp: 407197) Temperature Readings: [30.00, 28.06, 25.16, 26.45, 26.45, 20.65, 26.45, 20.97], Solar Cell 1: [Voltage: 1.68V, Current: 3.92mA], Solar Cell 2: [Voltage: 2.85V, Current: 5.88mA]
(Timestamp: 407699) Temperature Readings: [30.32, 28.39, 25.48, 26.13, 26.45, 20.65, 26.45, 21.29], Solar Cell 1: [Voltage: 1.86V, Current: 3.59mA], Solar Cell 2: [Voltage: 3.05V, Current: 5.88mA]
(Timestamp: 408202) Temperature Readings: [30.00, 28.39, 25.16, 26.45, 26.45, 20.00, 26.45, 20.32], Solar Cell 1: [Voltage: 1.63V, Current: 3.26mA], Solar Cell 2: [Voltage: 1.59V, Current: 4.24mA]
(Timestamp: 408705) Temperature Readings: [30.32, 28.39, 25.16, 26.45, 26.45, 20.65, 26.45, 21.29], Solar Cell 1: [Voltage: 1.62V, Current: 3.59mA], Solar Cell 2: [Voltage: 2.70V, Current: 5.55mA]
(Timestamp: 409207) Temperature Readings: [30.00, 28.39, 25.48, 26.45, 26.45, 20.65, 26.45, 20.97], Solar Cell 1: [Voltage: 1.86V, Current: 3.59mA], Solar Cell 2: [Voltage: 3.07V, Current: 6.20mA]
(Timestamp: 409710) Temperature Readings: [30.32, 28.39, 23.87, 26.45, 26.45, 20.32, 26.45, 20.65], Solar Cell 1: [Voltage: 1.61V, Current: 3.26mA], Solar Cell 2: [Voltage: 1.32V, Current: 111.01mA]
(Timestamp: 410213) Temperature Readings: [30.00, 28.39, 25.16, 26.45, 26.45, 20.65, 26.45, 20.97], Solar Cell 1: [Voltage: 1.71V, Current: 3.59mA], Solar Cell 2: [Voltage: 2.92V, Current: 5.88mA]
(Timestamp: 410716) Temperature Readings: [29.68, 28.06, 25.48, 26.13, 26.77, 20.65, 26.45, 20.97], Solar Cell 1: [Voltage: 1.86V, Current: 3.92mA], Solar Cell 2: [Voltage: 3.05V, Current: 6.20mA]
(Timestamp: 411219) Temperature Readings: [30.32, 28.39, 25.16, 26.45, 26.45, 20.65, 26.45, 21.29], Solar Cell 1: [Voltage: 1.47V, Current: 3.26mA], Solar Cell 2: [Voltage: 0.91V, Current: 78.03mA]
(Timestamp: 411721) Temperature Readings: [30.32, 28.39, 25.16, 26.45, 26.45, 20.65, 26.45, 20.97], Solar Cell 1: [Voltage: 1.75V, Current: 3.59mA], Solar Cell 2: [Voltage: 3.01V, Current: 6.53mA]
(Timestamp: 412224) Temperature Readings: [30.32, 28.39, 25.16, 26.45, 26.77, 20.65, 26.45, 20.97], Solar Cell 1: [Voltage: 1.86V, Current: 3.92mA], Solar Cell 2: [Voltage: 2.97V, Current: 5.88mA]
(Timestamp: 412727) Temperature Readings: [30.32, 28.06, 23.87, 26.45, 26.45, 20.65, 26.45, 21.61], Solar Cell 1: [Voltage: 1.37V, Current: 3.26mA], Solar Cell 2: [Voltage: 0.93V, Current: 83.26mA]
(Timestamp: 413233) Temperature Readings: [30.32, 28.71, 25.16, 26.45, 26.45, 20.65, 26.45, 20.65], Solar Cell 1: [Voltage: 1.75V, Current: 3.59mA], Solar Cell 2: [Voltage: 2.37V, Current: 5.22mA]
(Timestamp: 413736) Temperature Readings: [30.97, 28.39, 23.87, 26.45, 26.45, 20.32, 26.45, 20.32], Solar Cell 1: [Voltage: 1.54V, Current: 3.59mA], Solar Cell 2: [Voltage: 2.45V, Current: 5.22mA]
(Timestamp: 414239) Temperature Readings: [30.00, 28.71, 25.48, 26.45, 26.45, 20.65, 26.45, 20.97], Solar Cell 1: [Voltage: 1.85V, Current: 3.59mA], Solar Cell 2: [Voltage: 3.08V, Current: 6.20mA]
(Timestamp: 414742) Temperature Readings: [30.32, 28.39, 25.16, 26.45, 26.45, 20.00, 26.45, 20.32], Solar Cell 1: [Voltage: 1.64V, Current: 3.26mA], Solar Cell 2: [Voltage: 1.74V, Current: 4.24mA]
(Timestamp: 415245) Temperature Readings: [30.32, 28.39, 25.16, 26.13, 26.45, 20.65, 26.45, 20.97], Solar Cell 1: [Voltage: 1.64V, Current: 3.59mA], Solar Cell 2: [Voltage: 2.81V, Current: 5.88mA]
(Timestamp: 415747) Temperature Readings: [30.00, 28.39, 25.48, 26.45, 26.45, 20.65, 26.45, 20.97], Solar Cell 1: [Voltage: 1.88V, Current: 3.59mA], Solar Cell 2: [Voltage: 3.05V, Current: 6.20mA]
(Timestamp: 416250) Temperature Readings: [30.65, 28.39, 24.84, 26.45, 26.45, 20.00, 26.13, 20.65], Solar Cell 1: [Voltage: 1.58V, Current: 3.26mA], Solar Cell 2: [Voltage: 1.29V, Current: 115.25mA]
(Timestamp: 416752) Temperature Readings: [30.32, 28.39, 25.16, 26.45, 26.45, 20.65, 26.45, 20.97], Solar Cell 1: [Voltage: 1.66V, Current: 3.59mA], Solar Cell 2: [Voltage: 2.77V, Current: 5.88mA]
(Timestamp: 417255) Temperature Readings: [30.00, 28.71, 25.48, 26.77, 26.77, 20.65, 26.45, 20.97], Solar Cell 1: [Voltage: 1.87V, Current: 3.59mA], Solar Cell 2: [Voltage: 2.97V, Current: 5.88mA]
(Timestamp: 417758) Temperature Readings: [30.32, 28.71, 25.16, 26.45, 26.45, 20.65, 26.45, 22.90], Solar Cell 1: [Voltage: 1.56V, Current: 3.26mA], Solar Cell 2: [Voltage: 1.24V, Current: 111.66mA]
(Timestamp: 418260) Temperature Readings: [30.32, 28.39, 25.16, 26.45, 26.45, 20.32, 26.45, 20.97], Solar Cell 1: [Voltage: 1.67V, Current: 3.59mA], Solar Cell 2: [Voltage: 2.78V, Current: 5.55mA]
(Timestamp: 418766) Temperature Readings: [30.32, 28.39, 23.87, 26.45, 26.45, 20.65, 26.45, 21.29], Solar Cell 1: [Voltage: 1.41V, Current: 3.26mA], Solar Cell 2: [Voltage: 0.84V, Current: 71.83mA]
(Timestamp: 419269) Temperature Readings: [30.32, 28.39, 25.16, 26.45, 26.45, 20.65, 26.45, 20.97], Solar Cell 1: [Voltage: 1.77V, Current: 3.59mA], Solar Cell 2: [Voltage: 2.90V, Current: 5.88mA]
(Timestamp: 419772) Temperature Readings: [30.00, 28.39, 25.16, 26.45, 26.77, 20.97, 26.45, 21.61], Solar Cell 1: [Voltage: 1.88V, Current: 3.59mA], Solar Cell 2: [Voltage: 2.89V, Current: 5.88mA]
(Timestamp: 420275) Temperature Readings: [30.32, 28.71, 23.87, 26.45, 26.45, 20.32, 26.77, 21.94], Solar Cell 1: [Voltage: 1.39V, Current: 3.26mA], Solar Cell 2: [Voltage: 0.94V, Current: 83.91mA]
(Timestamp: 420777) Temperature Readings: [30.32, 28.39, 25.48, 26.45, 26.45, 20.65, 26.45, 20.97], Solar Cell 1: [Voltage: 1.83V, Current: 3.59mA], Solar Cell 2: [Voltage: 2.95V, Current: 6.20mA]
(Timestamp: 421280) Temperature Readings: [30.00, 28.71, 25.16, 26.45, 26.45, 20.65, 26.45, 20.97], Solar Cell 1: [Voltage: 1.84V, Current: 3.59mA], Solar Cell 2: [Voltage: 2.75V, Current: 5.55mA]
(Timestamp: 421783) Temperature Readings: [30.32, 28.39, 23.87, 26.45, 26.45, 20.00, 26.45, 20.32], Solar Cell 1: [Voltage: 1.41V, Current: 2.94mA], Solar Cell 2: [Voltage: 1.52V, Current: 4.57mA]
(Timestamp: 422286) Temperature Readings: [30.32, 28.71, 25.16, 26.45, 26.77, 20.65, 26.45, 20.97], Solar Cell 1: [Voltage: 1.84V, Current: 3.59mA], Solar Cell 2: [Voltage: 2.97V, Current: 5.88mA]
(Timestamp: 422789) Temperature Readings: [30.32, 28.39, 25.16, 26.45, 26.77, 20.00, 26.45, 20.97], Solar Cell 1: [Voltage: 1.79V, Current: 3.59mA], Solar Cell 2: [Voltage: 2.52V, Current: 5.22mA]
(Timestamp: 423291) Temperature Readings: [30.32, 28.39, 23.87, 26.45, 26.45, 20.00, 26.45, 20.32], Solar Cell 1: [Voltage: 1.50V, Current: 3.26mA], Solar Cell 2: [Voltage: 2.17V, Current: 4.90mA]
(Timestamp: 423794) Temperature Readings: [30.32, 28.39, 25.16, 26.45, 26.77, 20.65, 26.45, 21.61], Solar Cell 1: [Voltage: 1.87V, Current: 3.59mA], Solar Cell 2: [Voltage: 2.99V, Current: 5.88mA]
(Timestamp: 424297) Temperature Readings: [30.32, 28.39, 25.16, 26.45, 26.45, 20.32, 26.45, 20.32], Solar Cell 1: [Voltage: 1.72V, Current: 3.26mA], Solar Cell 2: [Voltage: 2.01V, Current: 4.90mA]
(Timestamp: 424803) Temperature Readings: [30.65, 28.39, 25.16, 26.45, 26.45, 20.65, 26.45, 21.29], Solar Cell 1: [Voltage: 1.86V, Current: 3.59mA], Solar Cell 2: [Voltage: 2.94V, Current: 5.88mA]
(Timestamp: 425306) Temperature Readings: [30.32, 28.71, 23.87, 26.45, 26.45, 20.65, 26.45, 21.61], Solar Cell 1: [Voltage: 1.41V, Current: 3.26mA], Solar Cell 2: [Voltage: 0.85V, Current: 71.50mA]
(Timestamp: 425809) Temperature Readings: [30.00, 28.71, 25.16, 26.45, 26.45, 20.65, 26.45, 20.97], Solar Cell 1: [Voltage: 1.78V, Current: 3.59mA], Solar Cell 2: [Voltage: 2.92V, Current: 6.20mA]
(Timestamp: 426312) Temperature Readings: [30.65, 28.71, 25.16, 26.77, 26.45, 20.32, 26.45, 20.97], Solar Cell 1: [Voltage: 1.84V, Current: 3.92mA], Solar Cell 2: [Voltage: 2.84V, Current: 6.20mA]
(Timestamp: 426814) Temperature Readings: [30.32, 28.39, 23.87, 26.45, 26.45, 20.65, 26.45, 21.61], Solar Cell 1: [Voltage: 1.38V, Current: 2.94mA], Solar Cell 2: [Voltage: 0.90V, Current: 80.65mA]
(Timestamp: 427317) Temperature Readings: [30.32, 28.71, 25.16, 26.45, 26.77, 20.65, 26.45, 20.97], Solar Cell 1: [Voltage: 1.77V, Current: 3.92mA], Solar Cell 2: [Voltage: 2.97V, Current: 6.20mA]
(Timestamp: 427820) Temperature Readings: [30.32, 28.71, 25.16, 26.77, 26.45, 20.65, 26.45, 20.97], Solar Cell 1: [Voltage: 1.85V, Current: 3.92mA], Solar Cell 2: [Voltage: 2.94V, Current: 5.88mA]
(Timestamp: 428322) Temperature Readings: [30.32, 28.39, 23.87, 26.45, 26.45, 20.65, 26.45, 21.61], Solar Cell 1: [Voltage: 1.37V, Current: 3.26mA], Solar Cell 2: [Voltage: 0.89V, Current: 78.69mA]
(Timestamp: 428825) Temperature Readings: [30.65, 28.71, 25.16, 26.45, 26.77, 20.65, 26.45, 20.97], Solar Cell 1: [Voltage: 1.77V, Current: 3.59mA], Solar Cell 2: [Voltage: 2.97V, Current: 5.88mA]
(Timestamp: 429327) Temperature Readings: [30.65, 28.39, 25.48, 26.45, 26.45, 20.65, 26.45, 20.97], Solar Cell 1: [Voltage: 1.85V, Current: 3.59mA], Solar Cell 2: [Voltage: 2.95V, Current: 5.88mA]
(Timestamp: 429830) Temperature Readings: [30.32, 28.39, 23.55, 26.45, 26.45, 20.65, 26.45, 21.61], Solar Cell 1: [Voltage: 1.37V, Current: 2.94mA], Solar Cell 2: [Voltage: 0.92V, Current: 82.60mA]
(Timestamp: 430333) Temperature Readings: [30.65, 28.39, 25.16, 26.77, 26.77, 20.65, 26.77, 20.97], Solar Cell 1: [Voltage: 1.80V, Current: 3.92mA], Solar Cell 2: [Voltage: 3.00V, Current: 6.20mA]
(Timestamp: 430839) Temperature Readings: [30.32, 28.71, 25.16, 26.77, 26.45, 20.65, 26.45, 20.32], Solar Cell 1: [Voltage: 1.55V, Current: 3.59mA], Solar Cell 2: [Voltage: 2.47V, Current: 5.22mA]
(Timestamp: 431342) Temperature Readings: [30.32, 28.71, 25.16, 26.45, 26.77, 20.65, 26.45, 20.97], Solar Cell 1: [Voltage: 1.87V, Current: 3.92mA], Solar Cell 2: [Voltage: 2.99V, Current: 5.88mA]
(Timestamp: 431845) Temperature Readings: [30.32, 28.71, 25.16, 26.45, 26.77, 20.00, 26.45, 20.32], Solar Cell 1: [Voltage: 1.63V, Current: 3.26mA], Solar Cell 2: [Voltage: 1.56V, Current: 4.24mA]
(Timestamp: 432348) Temperature Readings: [30.32, 28.71, 25.16, 26.45, 26.45, 20.65, 26.45, 20.97], Solar Cell 1: [Voltage: 1.68V, Current: 3.59mA], Solar Cell 2: [Voltage: 2.78V, Current: 5.88mA]
(Timestamp: 432851) Temperature Readings: [30.32, 28.71, 25.48, 26.45, 26.77, 20.65, 26.77, 20.97], Solar Cell 1: [Voltage: 1.86V, Current: 3.92mA], Solar Cell 2: [Voltage: 2.96V, Current: 5.88mA]
(Timestamp: 433353) Temperature Readings: [30.32, 28.71, 23.87, 26.45, 26.45, 20.65, 26.77, 22.26], Solar Cell 1: [Voltage: 1.48V, Current: 3.26mA], Solar Cell 2: [Voltage: 0.95V, Current: 82.28mA]
(Timestamp: 433856) Temperature Readings: [30.65, 28.71, 25.16, 26.45, 26.45, 20.65, 26.77, 20.97], Solar Cell 1: [Voltage: 1.75V, Current: 3.59mA], Solar Cell 2: [Voltage: 2.91V, Current: 5.88mA]
(Timestamp: 434359) Temperature Readings: [30.32, 28.71, 25.16, 26.45, 26.77, 20.65, 26.77, 20.97], Solar Cell 1: [Voltage: 1.85V, Current: 3.59mA], Solar Cell 2: [Voltage: 2.88V, Current: 5.88mA]
(Timestamp: 434862) Temperature Readings: [30.32, 28.71, 23.55, 26.45, 26.77, 20.65, 26.45, 21.61], Solar Cell 1: [Voltage: 1.37V, Current: 3.26mA], Solar Cell 2: [Voltage: 1.01V, Current: 94.03mA]
(Timestamp: 435365) Temperature Readings: [30.65, 28.71, 25.16, 26.45, 26.77, 20.65, 26.45, 20.97], Solar Cell 1: [Voltage: 1.82V, Current: 3.59mA], Solar Cell 2: [Voltage: 2.97V, Current: 5.88mA]
(Timestamp: 435867) Temperature Readings: [30.32, 28.71, 25.16, 26.45, 26.77, 20.32, 26.45, 20.97], Solar Cell 1: [Voltage: 1.79V, Current: 3.59mA], Solar Cell 2: [Voltage: 2.61V, Current: 5.55mA]
(Timestamp: 436370) Temperature Readings: [30.32, 28.71, 23.87, 26.45, 26.45, 20.00, 26.45, 20.65], Solar Cell 1: [Voltage: 1.48V, Current: 3.59mA], Solar Cell 2: [Voltage: 2.08V, Current: 4.90mA]
(Timestamp: 436877) Temperature Readings: [30.32, 28.71, 23.87, 26.77, 26.45, 20.97, 26.77, 22.58], Solar Cell 1: [Voltage: 1.52V, Current: 3.26mA], Solar Cell 2: [Voltage: 1.08V, Current: 96.64mA]
(Timestamp: 437379) Temperature Readings: [30.65, 28.71, 25.16, 26.45, 26.45, 20.65, 26.45, 20.97], Solar Cell 1: [Voltage: 1.70V, Current: 3.59mA], Solar Cell 2: [Voltage: 2.85V, Current: 5.88mA]
(Timestamp: 437882) Temperature Readings: [30.32, 28.39, 25.16, 26.45, 26.77, 20.65, 26.77, 20.97], Solar Cell 1: [Voltage: 1.86V, Current: 3.59mA], Solar Cell 2: [Voltage: 2.96V, Current: 5.88mA]
(Timestamp: 438385) Temperature Readings: [30.32, 28.71, 23.87, 26.45, 26.45, 20.65, 26.45, 21.94], Solar Cell 1: [Voltage: 1.48V, Current: 3.26mA], Solar Cell 2: [Voltage: 0.95V, Current: 83.58mA]
(Timestamp: 438887) Temperature Readings: [30.65, 28.71, 25.16, 26.45, 26.77, 20.65, 26.45, 20.97], Solar Cell 1: [Voltage: 1.74V, Current: 3.59mA], Solar Cell 2: [Voltage: 2.85V, Current: 5.88mA]
(Timestamp: 439390) Temperature Readings: [30.65, 28.39, 25.16, 26.45, 26.45, 20.65, 26.77, 20.97], Solar Cell 1: [Voltage: 1.87V, Current: 3.92mA], Solar Cell 2: [Voltage: 2.95V, Current: 5.88mA]
(Timestamp: 439892) Temperature Readings: [30.32, 29.03, 23.87, 26.45, 26.77, 20.65, 26.77, 22.26], Solar Cell 1: [Voltage: 1.49V, Current: 3.26mA], Solar Cell 2: [Voltage: 0.95V, Current: 83.58mA]
(Timestamp: 440395) Temperature Readings: [30.65, 28.71, 25.16, 26.45, 26.77, 20.65, 26.45, 20.97], Solar Cell 1: [Voltage: 1.77V, Current: 3.92mA], Solar Cell 2: [Voltage: 2.85V, Current: 5.88mA]
(Timestamp: 440898) Temperature Readings: [30.65, 28.71, 25.16, 26.45, 26.45, 20.65, 26.77, 20.97], Solar Cell 1: [Voltage: 1.86V, Current: 3.59mA], Solar Cell 2: [Voltage: 2.87V, Current: 5.88mA]
(Timestamp: 441401) Temperature Readings: [30.32, 28.71, 23.87, 26.45, 26.77, 20.32, 26.77, 21.94], Solar Cell 1: [Voltage: 1.38V, Current: 3.26mA], Solar Cell 2: [Voltage: 1.08V, Current: 100.56mA]
(Timestamp: 441903) Temperature Readings: [30.32, 28.71, 25.16, 26.45, 26.45, 20.65, 26.77, 20.97], Solar Cell 1: [Voltage: 1.84V, Current: 3.92mA], Solar Cell 2: [Voltage: 2.94V, Current: 5.88mA]
(Timestamp: 442410) Temperature Readings: [30.32, 28.71, 23.87, 26.45, 26.77, 20.32, 26.77, 20.97], Solar Cell 1: [Voltage: 1.63V, Current: 3.59mA], Solar Cell 2: [Voltage: 2.63V, Current: 5.22mA]
(Timestamp: 442913) Temperature Readings: [30.32, 28.71, 25.16, 26.45, 26.77, 20.65, 26.77, 20.97], Solar Cell 1: [Voltage: 1.88V, Current: 3.92mA], Solar Cell 2: [Voltage: 2.94V, Current: 5.88mA]
(Timestamp: 443415) Temperature Readings: [30.65, 28.71, 23.87, 26.77, 26.77, 20.65, 26.45, 22.58], Solar Cell 1: [Voltage: 1.56V, Current: 3.26mA], Solar Cell 2: [Voltage: 1.08V, Current: 96.64mA]
(Timestamp: 443918) Temperature Readings: [30.97, 28.71, 25.16, 26.45, 26.77, 20.00, 26.77, 20.97], Solar Cell 1: [Voltage: 1.78V, Current: 3.92mA], Solar Cell 2: [Voltage: 2.86V, Current: 5.88mA]
(Timestamp: 444421) Temperature Readings: [30.65, 28.71, 25.16, 26.13, 26.77, 20.65, 26.45, 20.97], Solar Cell 1: [Voltage: 1.86V, Current: 3.59mA], Solar Cell 2: [Voltage: 2.86V, Current: 5.88mA]
(Timestamp: 444924) Temperature Readings: [30.32, 28.71, 23.87, 26.45, 26.45, 20.32, 26.77, 21.61], Solar Cell 1: [Voltage: 1.38V, Current: 3.26mA], Solar Cell 2: [Voltage: 0.99V, Current: 91.09mA]
(Timestamp: 445427) Temperature Readings: [30.65, 28.71, 25.16, 26.77, 26.77, 20.65, 26.77, 20.97], Solar Cell 1: [Voltage: 1.83V, Current: 3.92mA], Solar Cell 2: [Voltage: 2.90V, Current: 5.88mA]
(Timestamp: 445929) Temperature Readings: [30.65, 28.71, 25.16, 26.45, 26.77, 20.00, 26.77, 20.97], Solar Cell 1: [Voltage: 1.79V, Current: 3.59mA], Solar Cell 2: [Voltage: 2.53V, Current: 5.22mA]
(Timestamp: 446432) Temperature Readings: [30.65, 28.71, 25.16, 26.45, 26.77, 20.00, 26.77, 20.65], Solar Cell 1: [Voltage: 1.51V, Current: 3.59mA], Solar Cell 2: [Voltage: 2.25V, Current: 4.90mA]
(Timestamp: 446935) Temperature Readings: [30.65, 28.71, 25.48, 26.45, 26.45, 20.65, 26.77, 20.97], Solar Cell 1: [Voltage: 1.86V, Current: 3.92mA], Solar Cell 2: [Voltage: 3.05V, Current: 6.20mA]
(Timestamp: 447438) Temperature Readings: [30.65, 29.03, 25.16, 26.45, 27.10, 20.00, 26.45, 20.32], Solar Cell 1: [Voltage: 1.70V, Current: 3.26mA], Solar Cell 2: [Voltage: 1.95V, Current: 4.57mA]
(Timestamp: 447940) Temperature Readings: [30.32, 28.71, 25.16, 26.77, 26.77, 20.32, 26.77, 20.97], Solar Cell 1: [Voltage: 1.59V, Current: 3.59mA], Solar Cell 2: [Voltage: 2.64V, Current: 5.55mA]
(Timestamp: 448446) Temperature Readings: [30.65, 29.03, 23.87, 26.45, 26.77, 20.32, 26.77, 21.94], Solar Cell 1: [Voltage: 1.48V, Current: 3.26mA], Solar Cell 2: [Voltage: 0.95V, Current: 82.28mA]
(Timestamp: 448949) Temperature Readings: [30.65, 28.71, 25.16, 26.45, 26.77, 20.65, 26.77, 20.97], Solar Cell 1: [Voltage: 1.76V, Current: 3.92mA], Solar Cell 2: [Voltage: 3.00V, Current: 6.20mA]
(Timestamp: 449452) Temperature Readings: [30.65, 28.71, 25.16, 26.45, 26.45, 20.65, 26.77, 20.97], Solar Cell 1: [Voltage: 1.86V, Current: 3.92mA], Solar Cell 2: [Voltage: 2.98V, Current: 5.88mA]
(Timestamp: 449954) Temperature Readings: [30.65, 28.71, 24.19, 26.77, 26.77, 20.32, 26.77, 21.29], Solar Cell 1: [Voltage: 1.41V, Current: 3.26mA], Solar Cell 2: [Voltage: 0.84V, Current: 71.50mA]
(Timestamp: 450457) Temperature Readings: [30.97, 28.71, 25.16, 26.45, 26.77, 20.32, 26.45, 20.97], Solar Cell 1: [Voltage: 1.76V, Current: 3.59mA], Solar Cell 2: [Voltage: 2.98V, Current: 6.20mA]
(Timestamp: 450959) Temperature Readings: [30.32, 28.71, 25.16, 26.45, 26.77, 20.32, 26.77, 20.97], Solar Cell 1: [Voltage: 1.83V, Current: 3.92mA], Solar Cell 2: [Voltage: 2.90V, Current: 6.20mA]
(Timestamp: 451462) Temperature Readings: [30.65, 28.71, 23.87, 26.77, 26.77, 20.65, 26.77, 22.58], Solar Cell 1: [Voltage: 1.37V, Current: 3.26mA], Solar Cell 2: [Voltage: 1.21V, Current: 113.30mA]
(Timestamp: 451965) Temperature Readings: [30.65, 28.71, 24.19, 26.77, 26.77, 20.65, 26.77, 20.97], Solar Cell 1: [Voltage: 1.81V, Current: 3.59mA], Solar Cell 2: [Voltage: 3.03V, Current: 6.20mA]
(Timestamp: 452468) Temperature Readings: [30.65, 28.71, 25.16, 26.77, 26.77, 20.32, 26.77, 20.97], Solar Cell 1: [Voltage: 1.77V, Current: 3.59mA], Solar Cell 2: [Voltage: 2.52V, Current: 5.55mA]
(Timestamp: 452971) Temperature Readings: [30.32, 29.03, 25.16, 26.77, 26.77, 20.32, 26.77, 20.32], Solar Cell 1: [Voltage: 1.52V, Current: 3.59mA], Solar Cell 2: [Voltage: 2.33V, Current: 5.22mA]
(Timestamp: 453473) Temperature Readings: [30.65, 28.71, 25.16, 26.45, 26.77, 20.65, 26.77, 20.97], Solar Cell 1: [Voltage: 1.85V, Current: 3.59mA], Solar Cell 2: [Voltage: 3.06V, Current: 6.20mA]
(Timestamp: 453976) Temperature Readings: [30.32, 28.71, 25.16, 26.77, 26.77, 20.00, 26.77, 20.32], Solar Cell 1: [Voltage: 1.63V, Current: 3.26mA], Solar Cell 2: [Voltage: 1.56V, Current: 4.24mA]
(Timestamp: 454483) Temperature Readings: [30.65, 28.71, 25.16, 26.77, 26.77, 20.32, 26.77, 20.97], Solar Cell 1: [Voltage: 1.84V, Current: 3.59mA], Solar Cell 2: [Voltage: 2.92V, Current: 5.88mA]
(Timestamp: 454985) Temperature Readings: [30.65, 28.71, 23.87, 26.77, 26.77, 20.32, 26.77, 22.58], Solar Cell 1: [Voltage: 1.37V, Current: 3.26mA], Solar Cell 2: [Voltage: 1.18V, Current: 111.01mA]
(Timestamp: 455488) Temperature Readings: [30.65, 28.71, 25.16, 26.77, 26.77, 20.32, 26.77, 20.97], Solar Cell 1: [Voltage: 1.81V, Current: 3.59mA], Solar Cell 2: [Voltage: 3.06V, Current: 6.20mA]
(Timestamp: 455991) Temperature Readings: [30.65, 29.03, 25.16, 26.77, 26.77, 20.65, 26.77, 20.97], Solar Cell 1: [Voltage: 1.79V, Current: 3.59mA], Solar Cell 2: [Voltage: 2.56V, Current: 5.55mA]
(Timestamp: 456494) Temperature Readings: [30.65, 28.71, 25.16, 26.77, 26.77, 20.32, 26.77, 20.65], Solar Cell 1: [Voltage: 1.52V, Current: 3.59mA], Solar Cell 2: [Voltage: 2.32V, Current: 5.22mA]
(Timestamp: 456997) Temperature Readings: [30.65, 29.03, 25.16, 26.77, 26.77, 20.32, 26.77, 20.97], Solar Cell 1: [Voltage: 1.86V, Current: 3.92mA], Solar Cell 2: [Voltage: 3.05V, Current: 6.20mA]
(Timestamp: 457499) Temperature Readings: [30.65, 28.39, 25.16, 26.45, 26.77, 20.00, 26.77, 20.32], Solar Cell 1: [Voltage: 1.63V, Current: 3.26mA], Solar Cell 2: [Voltage: 1.55V, Current: 4.24mA]
(Timestamp: 458002) Temperature Readings: [30.65, 28.71, 25.16, 26.45, 26.45, 20.32, 26.77, 20.97], Solar Cell 1: [Voltage: 1.65V, Current: 3.59mA], Solar Cell 2: [Voltage: 2.79V, Current: 5.55mA]
(Timestamp: 458505) Temperature Readings: [30.65, 28.71, 25.16, 26.77, 27.10, 20.65, 26.77, 20.97], Solar Cell 1: [Voltage: 1.86V, Current: 3.92mA], Solar Cell 2: [Voltage: 3.05V, Current: 6.20mA]
(Timestamp: 459007) Temperature Readings: [30.65, 29.03, 25.16, 26.77, 26.77, 20.00, 26.77, 20.97], Solar Cell 1: [Voltage: 1.57V, Current: 3.26mA], Solar Cell 2: [Voltage: 1.28V, Current: 115.25mA]
(Timestamp: 459510) Temperature Readings: [30.97, 28.71, 25.16, 26.77, 26.77, 20.32, 26.77, 20.97], Solar Cell 1: [Voltage: 1.70V, Current: 3.92mA], Solar Cell 2: [Voltage: 2.92V, Current: 5.88mA]
(Timestamp: 460016) Temperature Readings: [30.65, 29.03, 23.87, 26.77, 26.77, 20.65, 26.77, 22.58], Solar Cell 1: [Voltage: 1.37V, Current: 3.26mA], Solar Cell 2: [Voltage: 1.15V, Current: 108.40mA]
(Timestamp: 460519) Temperature Readings: [30.97, 29.03, 25.16, 26.77, 26.77, 20.65, 26.77, 20.97], Solar Cell 1: [Voltage: 1.81V, Current: 3.92mA], Solar Cell 2: [Voltage: 3.02V, Current: 6.20mA]
(Timestamp: 461021) Temperature Readings: [30.65, 28.71, 25.48, 26.77, 26.77, 20.32, 26.77, 20.65], Solar Cell 1: [Voltage: 1.79V, Current: 3.59mA], Solar Cell 2: [Voltage: 2.67V, Current: 5.55mA]
(Timestamp: 461524) Temperature Readings: [30.65, 29.03, 23.87, 26.77, 26.77, 20.00, 26.77, 20.32], Solar Cell 1: [Voltage: 1.48V, Current: 3.26mA], Solar Cell 2: [Voltage: 2.08V, Current: 4.90mA]
(Timestamp: 462027) Temperature Readings: [30.32, 29.03, 25.16, 26.77, 26.77, 20.65, 26.77, 20.97], Solar Cell 1: [Voltage: 1.85V, Current: 3.92mA], Solar Cell 2: [Voltage: 3.06V, Current: 6.20mA]
(Timestamp: 462530) Temperature Readings: [30.65, 28.71, 25.16, 26.77, 26.77, 20.32, 26.77, 20.32], Solar Cell 1: [Voltage: 1.66V, Current: 3.26mA], Solar Cell 2: [Voltage: 1.77V, Current: 3.92mA]
(Timestamp: 463032) Temperature Readings: [30.65, 29.03, 25.16, 26.77, 26.77, 20.32, 26.45, 20.97], Solar Cell 1: [Voltage: 1.65V, Current: 3.59mA], Solar Cell 2: [Voltage: 2.83V, Current: 5.88mA]
(Timestamp: 463535) Temperature Readings: [30.65, 29.03, 25.16, 26.77, 26.77, 20.65, 26.77, 20.97], Solar Cell 1: [Voltage: 1.86V, Current: 3.59mA], Solar Cell 2: [Voltage: 3.05V, Current: 6.20mA]
(Timestamp: 464038) Temperature Readings: [30.65, 29.03, 23.87, 26.77, 26.77, 20.65, 26.77, 21.61], Solar Cell 1: [Voltage: 1.45V, Current: 3.26mA], Solar Cell 2: [Voltage: 0.90V, Current: 76.07mA]
(Timestamp: 464541) Temperature Readings: [30.65, 29.03, 25.16, 26.77, 26.77, 20.65, 26.77, 20.97], Solar Cell 1: [Voltage: 1.78V, Current: 3.92mA], Solar Cell 2: [Voltage: 3.01V, Current: 6.20mA]
(Timestamp: 465044) Temperature Readings: [30.65, 29.03, 25.16, 26.77, 26.77, 20.65, 26.77, 20.97], Solar Cell 1: [Voltage: 1.83V, Current: 3.59mA], Solar Cell 2: [Voltage: 2.90V, Current: 5.88mA]
(Timestamp: 465546) Temperature Readings: [30.65, 28.71, 23.55, 26.45, 26.77, 20.65, 26.77, 22.58], Solar Cell 1: [Voltage: 1.39V, Current: 3.26mA], Solar Cell 2: [Voltage: 1.37V, Current: 17.96mA]
(Timestamp: 466053) Temperature Readings: [30.65, 28.71, 23.87, 26.77, 26.77, 20.00, 26.77, 20.32], Solar Cell 1: [Voltage: 1.63V, Current: 3.26mA], Solar Cell 2: [Voltage: 1.59V, Current: 4.24mA]
(Timestamp: 466556) Temperature Readings: [30.65, 29.03, 24.19, 26.77, 27.10, 20.65, 26.77, 20.65], Solar Cell 1: [Voltage: 1.68V, Current: 3.59mA], Solar Cell 2: [Voltage: 2.89V, Current: 5.88mA]
(Timestamp: 467058) Temperature Readings: [30.65, 29.03, 25.16, 26.77, 26.77, 20.65, 26.77, 20.97], Solar Cell 1: [Voltage: 1.86V, Current: 3.92mA], Solar Cell 2: [Voltage: 3.03V, Current: 5.88mA]
(Timestamp: 467561) Temperature Readings: [30.65, 29.03, 23.87, 26.77, 27.10, 20.65, 26.77, 21.29], Solar Cell 1: [Voltage: 1.41V, Current: 2.94mA], Solar Cell 2: [Voltage: 0.83V, Current: 70.52mA]
(Timestamp: 468064) Temperature Readings: [30.97, 29.03, 25.16, 26.77, 26.77, 20.65, 27.10, 20.97], Solar Cell 1: [Voltage: 1.79V, Current: 3.59mA], Solar Cell 2: [Voltage: 3.03V, Current: 6.20mA]
(Timestamp: 468567) Temperature Readings: [30.97, 29.03, 25.16, 26.77, 26.77, 20.65, 26.77, 20.97], Solar Cell 1: [Voltage: 1.84V, Current: 3.59mA], Solar Cell 2: [Voltage: 2.91V, Current: 5.88mA]
(Timestamp: 469069) Temperature Readings: [30.65, 29.03, 23.55, 26.77, 26.77, 20.65, 26.77, 21.61], Solar Cell 1: [Voltage: 1.37V, Current: 3.26mA], Solar Cell 2: [Voltage: 0.97V, Current: 89.13mA]
(Timestamp: 469572) Temperature Readings: [30.65, 29.03, 25.16, 26.77, 26.77, 20.65, 26.77, 20.97], Solar Cell 1: [Voltage: 1.82V, Current: 3.92mA], Solar Cell 2: [Voltage: 3.05V, Current: 6.20mA]
(Timestamp: 470074) Temperature Readings: [30.65, 29.03, 25.16, 26.77, 26.77, 20.65, 26.77, 20.97], Solar Cell 1: [Voltage: 1.83V, Current: 3.92mA], Solar Cell 2: [Voltage: 2.81V, Current: 5.55mA]
(Timestamp: 470577) Temperature Readings: [30.65, 29.03, 23.87, 26.77, 26.45, 20.65, 26.77, 22.90], Solar Cell 1: [Voltage: 1.39V, Current: 3.26mA], Solar Cell 2: [Voltage: 1.28V, Current: 98.60mA]
(Timestamp: 471080) Temperature Readings: [30.97, 29.03, 25.16, 26.77, 26.77, 20.32, 26.77, 20.97], Solar Cell 1: [Voltage: 1.83V, Current: 3.59mA], Solar Cell 2: [Voltage: 3.05V, Current: 6.20mA]
(Timestamp: 471582) Temperature Readings: [30.65, 29.03, 25.16, 27.10, 26.77, 20.32, 26.77, 20.65], Solar Cell 1: [Voltage: 1.81V, Current: 3.59mA], Solar Cell 2: [Voltage: 2.65V, Current: 5.22mA]
(Timestamp: 472089) Temperature Readings: [30.97, 29.03, 25.16, 26.45, 26.77, 20.65, 26.77, 20.97], Solar Cell 1: [Voltage: 1.86V, Current: 3.59mA], Solar Cell 2: [Voltage: 3.06V, Current: 6.20mA]
(Timestamp: 472592) Temperature Readings: [30.65, 28.71, 23.87, 26.77, 27.10, 20.65, 26.77, 22.26], Solar Cell 1: [Voltage: 1.52V, Current: 3.26mA], Solar Cell 2: [Voltage: 1.05V, Current: 92.73mA]
(Timestamp: 473094) Temperature Readings: [30.97, 29.03, 25.16, 26.77, 26.77, 20.65, 26.77, 20.97], Solar Cell 1: [Voltage: 1.75V, Current: 3.59mA], Solar Cell 2: [Voltage: 2.97V, Current: 6.20mA]
(Timestamp: 473597) Temperature Readings: [30.65, 29.03, 25.16, 26.77, 26.45, 22.26, 26.77, 20.97], Solar Cell 1: [Voltage: 1.86V, Current: 3.59mA], Solar Cell 2: [Voltage: 2.97V, Current: 5.55mA]
(Timestamp: 474100) Temperature Readings: [30.97, 29.03, 23.87, 26.77, 26.77, 20.65, 26.77, 21.61], Solar Cell 1: [Voltage: 1.37V, Current: 3.26mA], Solar Cell 2: [Voltage: 0.94V, Current: 83.91mA]
(Timestamp: 474603) Temperature Readings: [30.65, 29.03, 25.16, 26.77, 26.77, 20.65, 26.77, 20.97], Solar Cell 1: [Voltage: 1.82V, Current: 3.59mA], Solar Cell 2: [Voltage: 3.03V, Current: 6.20mA]
(Timestamp: 475105) Temperature Readings: [30.65, 29.03, 25.16, 26.77, 26.77, 20.32, 26.77, 20.65], Solar Cell 1: [Voltage: 1.81V, Current: 3.59mA], Solar Cell 2: [Voltage: 2.73V, Current: 5.55mA]
(Timestamp: 475608) Temperature Readings: [30.65, 29.03, 23.87, 26.45, 26.77, 20.00, 26.45, 20.00], Solar Cell 1: [Voltage: 1.45V, Current: 3.59mA], Solar Cell 2: [Voltage: 1.89V, Current: 4.57mA]
(Timestamp: 476111) Temperature Readings: [30.65, 29.03, 25.16, 26.77, 26.77, 20.32, 26.77, 20.97], Solar Cell 1: [Voltage: 1.85V, Current: 3.92mA], Solar Cell 2: [Voltage: 3.05V, Current: 6.20mA]
(Timestamp: 476614) Temperature Readings: [30.97, 29.03, 24.84, 26.77, 26.77, 20.00, 26.77, 20.32], Solar Cell 1: [Voltage: 1.70V, Current: 3.59mA], Solar Cell 2: [Voltage: 2.12V, Current: 4.90mA]
(Timestamp: 477117) Temperature Readings: [30.32, 29.03, 25.16, 26.77, 26.77, 20.65, 26.77, 20.65], Solar Cell 1: [Voltage: 1.60V, Current: 3.59mA], Solar Cell 2: [Voltage: 2.66V, Current: 5.55mA]
(Timestamp: 477619) Temperature Readings: [30.65, 29.03, 25.16, 26.77, 26.77, 20.65, 26.77, 20.97], Solar Cell 1: [Voltage: 1.86V, Current: 3.59mA], Solar Cell 2: [Voltage: 3.06V, Current: 6.20mA]
(Timestamp: 478126) Temperature Readings: [30.97, 29.03, 25.16, 26.77, 27.10, 20.65, 26.77, 20.97], Solar Cell 1: [Voltage: 1.78V, Current: 3.59mA], Solar Cell 2: [Voltage: 3.01V, Current: 5.88mA]
(Timestamp: 478628) Temperature Readings: [30.97, 29.03, 25.16, 26.77, 26.77, 20.65, 26.77, 20.97], Solar Cell 1: [Voltage: 1.86V, Current: 3.59mA], Solar Cell 2: [Voltage: 2.95V, Current: 6.20mA]
(Timestamp: 479131) Temperature Readings: [30.97, 28.71, 23.87, 26.77, 27.10, 20.65, 26.77, 21.29], Solar Cell 1: [Voltage: 1.39V, Current: 2.94mA], Solar Cell 2: [Voltage: 0.85V, Current: 72.48mA]
(Timestamp: 479633) Temperature Readings: [30.97, 29.03, 25.16, 26.77, 26.77, 20.65, 26.77, 20.97], Solar Cell 1: [Voltage: 1.77V, Current: 3.59mA], Solar Cell 2: [Voltage: 2.99V, Current: 6.20mA]
(Timestamp: 480136) Temperature Readings: [30.97, 29.03, 25.16, 26.77, 27.10, 20.65, 26.77, 20.97], Solar Cell 1: [Voltage: 1.84V, Current: 3.59mA], Solar Cell 2: [Voltage: 2.93V, Current: 5.88mA]
(Timestamp: 480639) Temperature Readings: [30.97, 29.35, 23.87, 26.77, 26.77, 20.65, 26.77, 21.29], Solar Cell 1: [Voltage: 1.37V, Current: 2.94mA], Solar Cell 2: [Voltage: 0.86V, Current: 74.12mA]
(Timestamp: 481141) Temperature Readings: [30.65, 29.35, 24.84, 26.77, 27.10, 20.65, 26.77, 20.97], Solar Cell 1: [Voltage: 1.77V, Current: 3.59mA], Solar Cell 2: [Voltage: 2.99V, Current: 6.20mA]
(Timestamp: 481644) Temperature Readings: [30.65, 29.03, 25.16, 27.10, 27.10, 20.65, 26.77, 20.97], Solar Cell 1: [Voltage: 1.85V, Current: 3.92mA], Solar Cell 2: [Voltage: 2.96V, Current: 5.88mA]
(Timestamp: 482147) Temperature Readings: [30.97, 29.35, 23.87, 26.77, 27.10, 20.65, 26.77, 21.61], Solar Cell 1: [Voltage: 1.36V, Current: 2.94mA], Solar Cell 2: [Voltage: 0.91V, Current: 81.30mA]
(Timestamp: 482649) Temperature Readings: [31.29, 29.35, 25.16, 26.77, 26.77, 20.65, 26.77, 20.97], Solar Cell 1: [Voltage: 1.80V, Current: 3.59mA], Solar Cell 2: [Voltage: 3.00V, Current: 5.88mA]
(Timestamp: 483152) Temperature Readings: [30.65, 29.03, 25.16, 26.77, 27.10, 20.32, 26.77, 20.97], Solar Cell 1: [Voltage: 1.83V, Current: 3.59mA], Solar Cell 2: [Voltage: 2.75V, Current: 5.88mA]
(Timestamp: 483659) Temperature Readings: [30.97, 29.35, 25.16, 26.77, 27.10, 20.65, 26.77, 20.97], Solar Cell 1: [Voltage: 1.85V, Current: 3.92mA], Solar Cell 2: [Voltage: 3.03V, Current: 6.20mA]
(Timestamp: 484161) Temperature Readings: [30.65, 29.35, 23.87, 26.77, 26.77, 20.00, 26.77, 19.68], Solar Cell 1: [Voltage: 1.61V, Current: 3.26mA], Solar Cell 2: [Voltage: 1.47V, Current: 6.86mA]
(Timestamp: 484664) Temperature Readings: [30.65, 29.03, 25.16, 26.77, 26.77, 20.32, 27.10, 20.97], Solar Cell 1: [Voltage: 1.69V, Current: 3.92mA], Solar Cell 2: [Voltage: 2.83V, Current: 5.88mA]
(Timestamp: 485167) Temperature Readings: [30.97, 29.03, 25.16, 26.77, 26.77, 20.65, 26.77, 20.97], Solar Cell 1: [Voltage: 1.86V, Current: 3.92mA], Solar Cell 2: [Voltage: 3.01V, Current: 5.88mA]
(Timestamp: 485670) Temperature Readings: [30.97, 29.03, 23.87, 26.77, 27.10, 20.32, 26.77, 22.26], Solar Cell 1: [Voltage: 1.50V, Current: 3.26mA], Solar Cell 2: [Voltage: 0.95V, Current: 83.58mA]
(Timestamp: 486173) Temperature Readings: [30.97, 29.03, 25.16, 26.77, 27.10, 20.32, 26.77, 20.97], Solar Cell 1: [Voltage: 1.75V, Current: 3.59mA], Solar Cell 2: [Voltage: 2.94V, Current: 5.88mA]
(Timestamp: 486675) Temperature Readings: [31.29, 29.03, 25.16, 26.77, 26.77, 20.65, 27.10, 20.97], Solar Cell 1: [Voltage: 1.85V, Current: 3.92mA], Solar Cell 2: [Voltage: 2.94V, Current: 5.88mA]
(Timestamp: 487178) Temperature Readings: [30.65, 29.35, 23.87, 26.77, 27.10, 20.32, 26.77, 21.29], Solar Cell 1: [Voltage: 1.37V, Current: 3.26mA], Solar Cell 2: [Voltage: 0.88V, Current: 78.03mA]
(Timestamp: 487681) Temperature Readings: [30.97, 29.03, 25.16, 26.77, 27.10, 20.65, 26.77, 20.97], Solar Cell 1: [Voltage: 1.80V, Current: 3.92mA], Solar Cell 2: [Voltage: 2.99V, Current: 6.20mA]
(Timestamp: 488184) Temperature Readings: [30.97, 29.03, 25.16, 26.77, 26.77, 20.65, 26.77, 20.97], Solar Cell 1: [Voltage: 1.82V, Current: 3.59mA], Solar Cell 2: [Voltage: 2.79V, Current: 5.88mA]
(Timestamp: 488686) Temperature Readings: [31.29, 29.03, 23.87, 27.10, 26.77, 20.00, 27.10, 20.00], Solar Cell 1: [Voltage: 1.39V, Current: 3.26mA], Solar Cell 2: [Voltage: 1.50V, Current: 4.24mA]
(Timestamp: 489189) Temperature Readings: [30.97, 29.03, 25.16, 26.77, 27.10, 20.65, 27.10, 20.97], Solar Cell 1: [Voltage: 1.81V, Current: 3.92mA], Solar Cell 2: [Voltage: 3.01V, Current: 6.20mA]
(Timestamp: 489695) Temperature Readings: [30.97, 29.35, 23.87, 26.77, 27.10, 20.32, 27.10, 20.32], Solar Cell 1: [Voltage: 1.52V, Current: 3.59mA], Solar Cell 2: [Voltage: 2.35V, Current: 5.22mA]
(Timestamp: 490198) Temperature Readings: [30.97, 29.03, 25.16, 26.77, 27.10, 20.32, 26.77, 20.97], Solar Cell 1: [Voltage: 1.85V, Current: 3.59mA], Solar Cell 2: [Voltage: 3.03V, Current: 6.20mA]
(Timestamp: 490700) Temperature Readings: [30.65, 29.03, 25.16, 26.77, 27.10, 20.00, 26.77, 20.32], Solar Cell 1: [Voltage: 1.72V, Current: 3.59mA], Solar Cell 2: [Voltage: 2.22V, Current: 4.90mA]
(Timestamp: 491203) Temperature Readings: [30.97, 29.35, 25.16, 26.77, 27.10, 20.32, 26.77, 20.65], Solar Cell 1: [Voltage: 1.49V, Current: 3.59mA], Solar Cell 2: [Voltage: 2.22V, Current: 4.90mA]
(Timestamp: 491705) Temperature Readings: [30.97, 29.03, 25.16, 26.77, 27.10, 20.00, 26.77, 20.97], Solar Cell 1: [Voltage: 1.86V, Current: 3.92mA], Solar Cell 2: [Voltage: 3.01V, Current: 6.20mA]
(Timestamp: 492208) Temperature Readings: [30.97, 29.03, 25.16, 26.77, 26.77, 20.00, 26.77, 20.32], Solar Cell 1: [Voltage: 1.74V, Current: 3.59mA], Solar Cell 2: [Voltage: 2.32V, Current: 4.90mA]
(Timestamp: 492711) Temperature Readings: [30.97, 29.03, 23.87, 26.77, 26.77, 20.00, 26.77, 20.32], Solar Cell 1: [Voltage: 1.53V, Current: 3.59mA], Solar Cell 2: [Voltage: 2.41V, Current: 5.22mA]
(Timestamp: 493214) Temperature Readings: [30.97, 29.35, 25.16, 26.77, 27.10, 20.65, 26.77, 20.97], Solar Cell 1: [Voltage: 1.86V, Current: 3.59mA], Solar Cell 2: [Voltage: 3.03V, Current: 5.88mA]
(Timestamp: 493717) Temperature Readings: [31.29, 29.35, 23.87, 26.77, 27.10, 20.00, 26.77, 20.32], Solar Cell 1: [Voltage: 1.66V, Current: 3.59mA], Solar Cell 2: [Voltage: 1.79V, Current: 4.24mA]
(Timestamp: 494219) Temperature Readings: [30.97, 29.03, 23.87, 26.77, 27.10, 20.32, 26.77, 20.97], Solar Cell 1: [Voltage: 1.62V, Current: 3.59mA], Solar Cell 2: [Voltage: 2.71V, Current: 5.55mA]
(Timestamp: 494722) Temperature Readings: [30.97, 29.03, 25.16, 26.77, 27.10, 20.65, 26.77, 20.97], Solar Cell 1: [Voltage: 1.86V, Current: 3.59mA], Solar Cell 2: [Voltage: 3.01V, Current: 6.20mA]
(Timestamp: 495225) Temperature Readings: [30.97, 29.35, 23.87, 26.77, 27.10, 20.00, 26.77, 21.29], Solar Cell 1: [Voltage: 1.57V, Current: 3.26mA], Solar Cell 2: [Voltage: 1.27V, Current: 114.27mA]
(Timestamp: 495731) Temperature Readings: [31.29, 29.35, 25.16, 26.77, 27.10, 20.65, 26.77, 20.97], Solar Cell 1: [Voltage: 1.84V, Current: 3.59mA], Solar Cell 2: [Voltage: 2.86V, Current: 5.88mA]
(Timestamp: 496234) Temperature Readings: [30.97, 29.35, 23.55, 26.77, 27.10, 20.65, 26.77, 21.94], Solar Cell 1: [Voltage: 1.37V, Current: 3.26mA], Solar Cell 2: [Voltage: 1.06V, Current: 98.60mA]
(Timestamp: 496737) Temperature Readings: [30.97, 29.35, 25.16, 26.77, 26.77, 20.65, 27.10, 20.97], Solar Cell 1: [Voltage: 1.81V, Current: 3.59mA], Solar Cell 2: [Voltage: 2.97V, Current: 6.20mA]
(Timestamp: 497240) Temperature Readings: [30.97, 29.03, 25.16, 26.45, 27.10, 20.32, 26.77, 20.97], Solar Cell 1: [Voltage: 1.81V, Current: 3.59mA], Solar Cell 2: [Voltage: 2.74V, Current: 5.55mA]
(Timestamp: 497742) Temperature Readings: [31.29, 29.35, 23.87, 26.77, 27.10, 20.00, 27.10, 19.68], Solar Cell 1: [Voltage: 1.41V, Current: 3.26mA], Solar Cell 2: [Voltage: 1.52V, Current: 4.24mA]
(Timestamp: 498245) Temperature Readings: [30.97, 29.68, 25.16, 26.77, 27.10, 20.65, 26.77, 21.29], Solar Cell 1: [Voltage: 1.83V, Current: 3.59mA], Solar Cell 2: [Voltage: 2.99V, Current: 5.88mA]
(Timestamp: 498748) Temperature Readings: [30.65, 29.35, 23.87, 26.77, 27.10, 20.00, 26.77, 20.65], Solar Cell 1: [Voltage: 1.76V, Current: 3.59mA], Solar Cell 2: [Voltage: 2.49V, Current: 5.22mA]
(Timestamp: 499251) Temperature Readings: [30.97, 29.35, 23.87, 26.77, 26.77, 20.00, 27.10, 20.32], Solar Cell 1: [Voltage: 1.48V, Current: 3.59mA], Solar Cell 2: [Voltage: 2.14V, Current: 5.22mA]
(Timestamp: 499753) Temperature Readings: [31.29, 29.35, 25.16, 26.77, 27.10, 20.65, 26.77, 20.97], Solar Cell 1: [Voltage: 1.83V, Current: 3.92mA], Solar Cell 2: [Voltage: 2.99V, Current: 5.88mA]
(Timestamp: 500256) Temperature Readings: [31.29, 29.35, 25.16, 26.77, 27.10, 20.00, 26.77, 20.65], Solar Cell 1: [Voltage: 1.77V, Current: 3.59mA], Solar Cell 2: [Voltage: 2.55V, Current: 5.55mA]
(Timestamp: 500759) Temperature Readings: [30.97, 29.35, 23.55, 26.77, 27.10, 20.00, 26.77, 20.32], Solar Cell 1: [Voltage: 1.45V, Current: 3.26mA], Solar Cell 2: [Voltage: 1.93V, Current: 4.57mA]
(Timestamp: 501265) Temperature Readings: [30.97, 29.35, 23.87, 26.77, 27.10, 20.00, 27.10, 20.00], Solar Cell 1: [Voltage: 1.65V, Current: 3.26mA], Solar Cell 2: [Voltage: 1.70V, Current: 4.24mA]
(Timestamp: 501767) Temperature Readings: [30.97, 29.35, 23.87, 26.77, 26.77, 20.32, 26.77, 20.32], Solar Cell 1: [Voltage: 1.59V, Current: 3.59mA], Solar Cell 2: [Voltage: 2.61V, Current: 5.55mA]
(Timestamp: 502270) Temperature Readings: [30.97, 29.03, 25.16, 26.77, 27.10, 20.32, 26.77, 20.97], Solar Cell 1: [Voltage: 1.86V, Current: 3.92mA], Solar Cell 2: [Voltage: 3.01V, Current: 5.55mA]
(Timestamp: 502773) Temperature Readings: [30.97, 29.03, 23.87, 26.77, 27.10, 20.00, 27.10, 20.32], Solar Cell 1: [Voltage: 1.66V, Current: 3.26mA], Solar Cell 2: [Voltage: 1.85V, Current: 4.57mA]
(Timestamp: 503275) Temperature Readings: [30.97, 29.35, 23.87, 26.77, 27.10, 20.00, 27.10, 20.65], Solar Cell 1: [Voltage: 1.60V, Current: 3.59mA], Solar Cell 2: [Voltage: 2.66V, Current: 5.55mA]
(Timestamp: 503778) Temperature Readings: [30.97, 29.35, 25.16, 26.77, 26.77, 20.32, 27.10, 20.97], Solar Cell 1: [Voltage: 1.85V, Current: 3.92mA], Solar Cell 2: [Voltage: 3.01V, Current: 6.20mA]
(Timestamp: 504281) Temperature Readings: [31.29, 29.35, 23.87, 26.77, 27.10, 20.00, 26.77, 20.32], Solar Cell 1: [Voltage: 1.57V, Current: 3.26mA], Solar Cell 2: [Voltage: 1.32V, Current: 101.54mA]
(Timestamp: 504784) Temperature Readings: [31.29, 29.35, 23.87, 26.77, 27.10, 20.00, 27.10, 20.97], Solar Cell 1: [Voltage: 1.69V, Current: 3.59mA], Solar Cell 2: [Voltage: 2.83V, Current: 5.88mA]
(Timestamp: 505287) Temperature Readings: [30.97, 29.68, 25.16, 26.77, 27.10, 20.65, 27.10, 20.97], Solar Cell 1: [Voltage: 1.87V, Current: 3.92mA], Solar Cell 2: [Voltage: 3.00V, Current: 5.88mA]
(Timestamp: 505789) Temperature Readings: [30.97, 29.68, 23.87, 26.77, 27.10, 20.65, 26.77, 22.26], Solar Cell 1: [Voltage: 1.48V, Current: 3.26mA], Solar Cell 2: [Voltage: 0.97V, Current: 83.91mA]
(Timestamp: 506292) Temperature Readings: [30.97, 29.35, 25.16, 26.77, 27.10, 20.32, 26.77, 20.97], Solar Cell 1: [Voltage: 1.75V, Current: 3.59mA], Solar Cell 2: [Voltage: 2.91V, Current: 5.88mA]
(Timestamp: 506795) Temperature Readings: [31.29, 29.35, 25.16, 26.77, 27.10, 20.65, 26.77, 20.97], Solar Cell 1: [Voltage: 1.85V, Current: 3.59mA], Solar Cell 2: [Voltage: 2.95V, Current: 5.88mA]
(Timestamp: 507301) Temperature Readings: [31.29, 29.35, 25.16, 26.77, 27.10, 20.65, 26.77, 20.97], Solar Cell 1: [Voltage: 1.82V, Current: 3.59mA], Solar Cell 2: [Voltage: 3.01V, Current: 6.20mA]
(Timestamp: 507804) Temperature Readings: [31.29, 29.35, 25.16, 26.77, 27.10, 20.00, 26.77, 20.65], Solar Cell 1: [Voltage: 1.76V, Current: 3.59mA], Solar Cell 2: [Voltage: 2.48V, Current: 5.22mA]
(Timestamp: 508307) Temperature Readings: [30.97, 29.35, 23.87, 27.10, 27.10, 20.00, 27.10, 20.32], Solar Cell 1: [Voltage: 1.48V, Current: 3.59mA], Solar Cell 2: [Voltage: 2.15V, Current: 4.90mA]
(Timestamp: 508810) Temperature Readings: [30.65, 29.35, 25.16, 26.77, 27.10, 20.65, 26.77, 20.97], Solar Cell 1: [Voltage: 1.85V, Current: 3.59mA], Solar Cell 2: [Voltage: 3.03V, Current: 6.20mA]
(Timestamp: 509312) Temperature Readings: [30.97, 29.35, 25.16, 26.77, 27.10, 20.32, 26.77, 20.32], Solar Cell 1: [Voltage: 1.71V, Current: 3.59mA], Solar Cell 2: [Voltage: 2.12V, Current: 4.90mA]
(Timestamp: 509815) Temperature Readings: [30.97, 29.35, 23.87, 26.77, 27.10, 20.00, 27.10, 20.65], Solar Cell 1: [Voltage: 1.54V, Current: 3.59mA], Solar Cell 2: [Voltage: 2.32V, Current: 5.22mA]
(Timestamp: 510318) Temperature Readings: [31.61, 29.35, 25.16, 26.77, 27.10, 20.65, 26.77, 20.97], Solar Cell 1: [Voltage: 1.85V, Current: 3.92mA], Solar Cell 2: [Voltage: 3.02V, Current: 6.20mA]
(Timestamp: 510820) Temperature Readings: [30.97, 29.68, 25.16, 26.77, 27.10, 20.00, 27.10, 20.97], Solar Cell 1: [Voltage: 1.77V, Current: 3.59mA], Solar Cell 2: [Voltage: 2.50V, Current: 5.22mA]
(Timestamp: 511323) Temperature Readings: [30.97, 29.35, 23.87, 26.77, 27.10, 20.00, 27.10, 20.32], Solar Cell 1: [Voltage: 1.46V, Current: 3.59mA], Solar Cell 2: [Voltage: 2.02V, Current: 4.57mA]
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
